mountaineerman/KCP2/Checklists/3_KeyBindings.pdf

d = default, dm = default(mod), nd = not default
Ca tegory | Key | ^ | Effect
| S | d | Rotate part up
| W | d | Rotate part down
| A | d | Rotate part left (flat)
| D | d | Rotate part right (flat)
| Q | d | Rotate part left
| E | d | Rotate part right
| Shift + W/S/A/D/Q/E | d | Rotate parts in 5° instead of 90° steps
| ` (back quote) | d | Search part
| Delete | d | Delete selected part
| L | dm | Toggle day/night mode & part lights (LightsOut)
| U | dm | Toggle all part lights (LightsOut)
| 1 | d | Place Mode
| 2 | d | Offset Mode
| 3 | d | Rotate Mode
| 4 | d | Root Mode
| 5 | dm | Part Scale Mode (TweakScale)
| 6 | dm | Open RCS Build Aid
| I/J/K/L/H/N | dm | Visualize RCS (RCS Build Aid)
| LeftCtrl (hold) | dm | Override “match node size (TweakScale)
| M | dm | Toggle “match node size (TweakScale)
| F | d | In Place mode: Toggle Symmetry between vessel or parent part
| F | d | In Offset mode: Toggle between absolute or load centered offset
| F | d | In Rotate mode: Toggle between absolute or relative rotation
| Ctrl + Z | d | Undo last action
| Ctrl + Y | d | Redo last action
| LeftAlt (hold) | d | Disable surface attach/exclusively use node attach
| Shift + Left-click | d | Move the entire ship
| Control + Left-click | d | Toggle part for snap and show part name
| LeftAlt + Left-click | d | Duplicate part or assembly in VAB
| Page Up/Down | d | Scroll view up/down
| Scroll Wheel | d
| R | d | Toggle Symmetry Method between mirror or radial
| X | d | Cycle symmetry settings (next)
| Shift + X | d | Cycle symmetry settings (previous)
| C | d | Toggle Angle Snap: next
| Shift + C | d | Toggle Angle Snap: previous
| LeftAlt + Shift + Left Click | dm | Strip symmetry from part
| V | dm | Vertically center part
| H | dm | Horizontally center part
| U | dm | ?
| T | dm | Toggle surface/node attachment mode
| Alt + Z | dm | Toggle part clipping
| Space (no part selected) | dm | Reset camera pitch & heading
| In Offset Mode, open EEX > Fine Adjustments, ↑/↓/←/→/Rshift/Rctrl | dm | Move or Rotate part

VAB/SPH Controls

Editor Extensions Redux

Ca tegory | Key | ^ | Effect
| F1 | d | Screenshot
| F2 | d | Toggle UI visibility
| F3 | d | Toggle results screen
| F4 | d | Toggle ship labels & docking target/distance indicators
| F5 | d | Quicksave
| RightShift + F5 | d | Quicksave (choose name)
| F6 | d | Previous action set
| F7 | d | Next action set
| F9 (Hold) | d | Load quicksave
| RightShift + F9 | d | Load a specific quicksave
| F10 | d | Toggle temperature gauges
| RightShift + F10 | dm | Open Contract Configurator window
| F11 | d | Toggle temperatures overlay
| F12 | d | Toggle aerodynamic forces overlay
| LeftAlt + F12 | d | Debug/cheat menu
| Escape | d | Pause Menu
| F (Hold) | d | Invert SAS state
| C | d | Toggle IVA view
| V | d | Toggle camera view (auto/free/orbital/chase)
| ` (back quote) | d | Reset camera
| \ | d | Toggle camera movement with mouse
| LeftAlt + . (period) | d | Forced time warp increase (Physical time warp)
| LeftAlt + , (comma) | d | Forced time warp decrease (Physical time warp)
| / | d | Stop time warp
| - (minus) | nd | Toggle navball
| ] | d | Focus through ships (next)
| [ | d | Cycle through ships (previous)
| 1-9, 0 | d | Activate custom action group 1-10
| LeftAlt + W/S/A/D/Q/E | d | Trim pitch/yaw/roll
| LeftAlt + X | d | Reset trim
| Right-click | d | Open part info window
| LeftAlt + Right-click | d | Open multiple info windows for fuel transfer
| LeftAlt + N | dm | Toggle maneuver node gizmo
| Tab | d | Cycle focus in orbital map
| Shift + Tab | d | Reverse cycle focus in orbital map
| ` (back quote) | d | Reset focus in orbital map
| W | d | Walk/jetpack forward
| S | d | Walk/jetpack backwards
| A | d | Walk/jetpack left
| D | d | Walk/jetpack right
| R | d | Toggle jetpack
| Q | d | Jetpack rotate left
| E | d | Jetpack rotate right
| Left-Shift | d | Jetpack up
| Left-Control | d | Jetpack down
| Left-click and drag left | d | Jet counter clockwise
| Left-click and drag right | d | Jet clockwise
| Left-click and drag up | d | Pitch down by jet
| Left-click and drag down | d | Pitch up by jet
| Space | d | Jetpack - Reorient camera
| Space | d | Jump
| LeftShift (hold) | d | Run
| F | d | Use part
| F | dm | Toggle desire to grab ladder (Easyboard)
| I | d | Toggle EVA Construction Mode
| B | d | Board
| B | dm | Toggle desire to board (Easyboard)
| U | d | Toggle lights
| O | d | Toggle helmet
| P | d | Deploy parachute
| Shift + (W/S/A/D) + Space | d | Jump to different directions when on ladders

Flight – System

Settings

Flight Controls

Map

EVA

Controls
