mountaineerman/KCP2/KCP2-physical/Documentation/ScrewDimensions.png

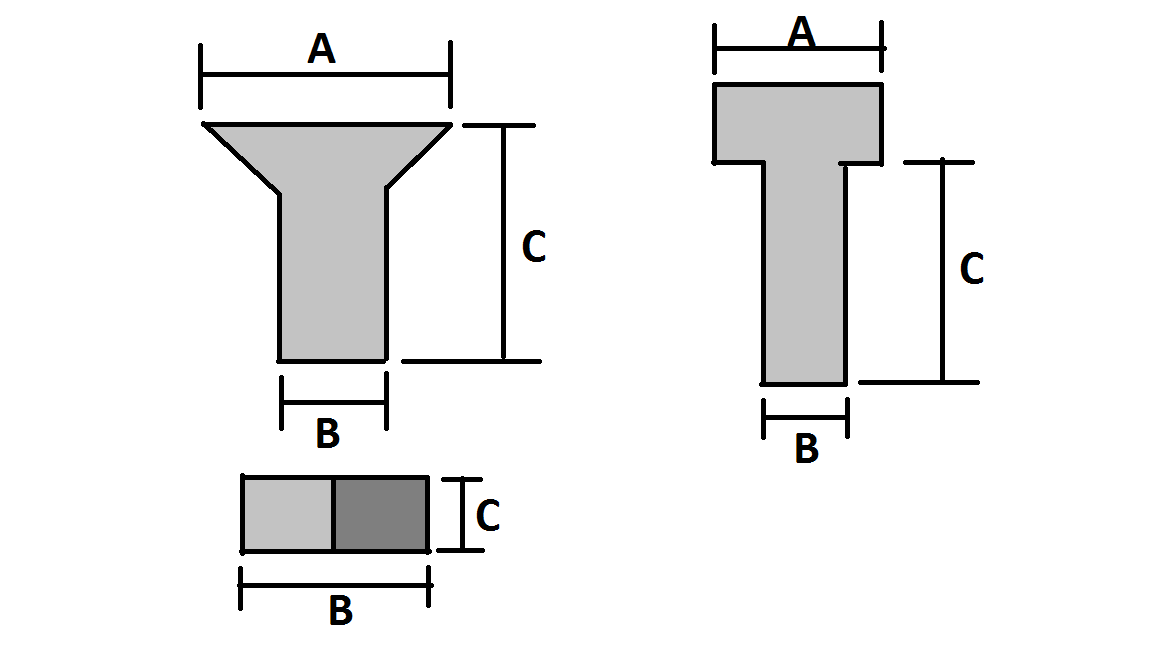
KCP2-physical/Documentation/ScrewDimensions.png
