mountaineerman/KCP2/KCP2-physical/GaugeBackgrounds/Navball.PNG

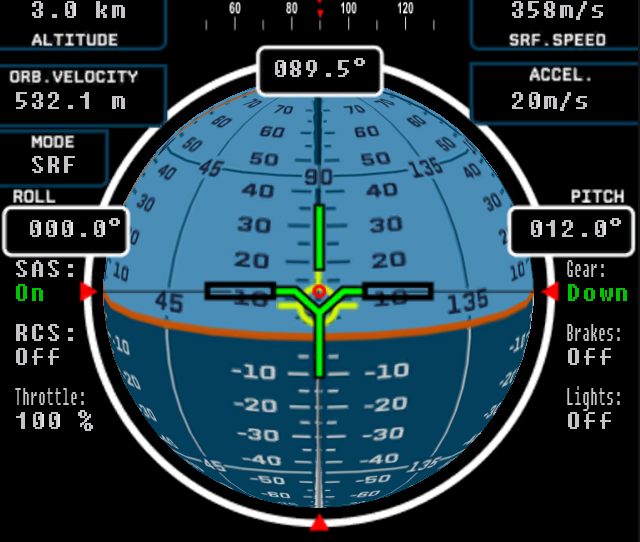
KCP2-physical/GaugeBackgrounds/Navball.PNG
