mountaineerman/KCP2/KCP2-physical/Ideas/deltaV map - new.png

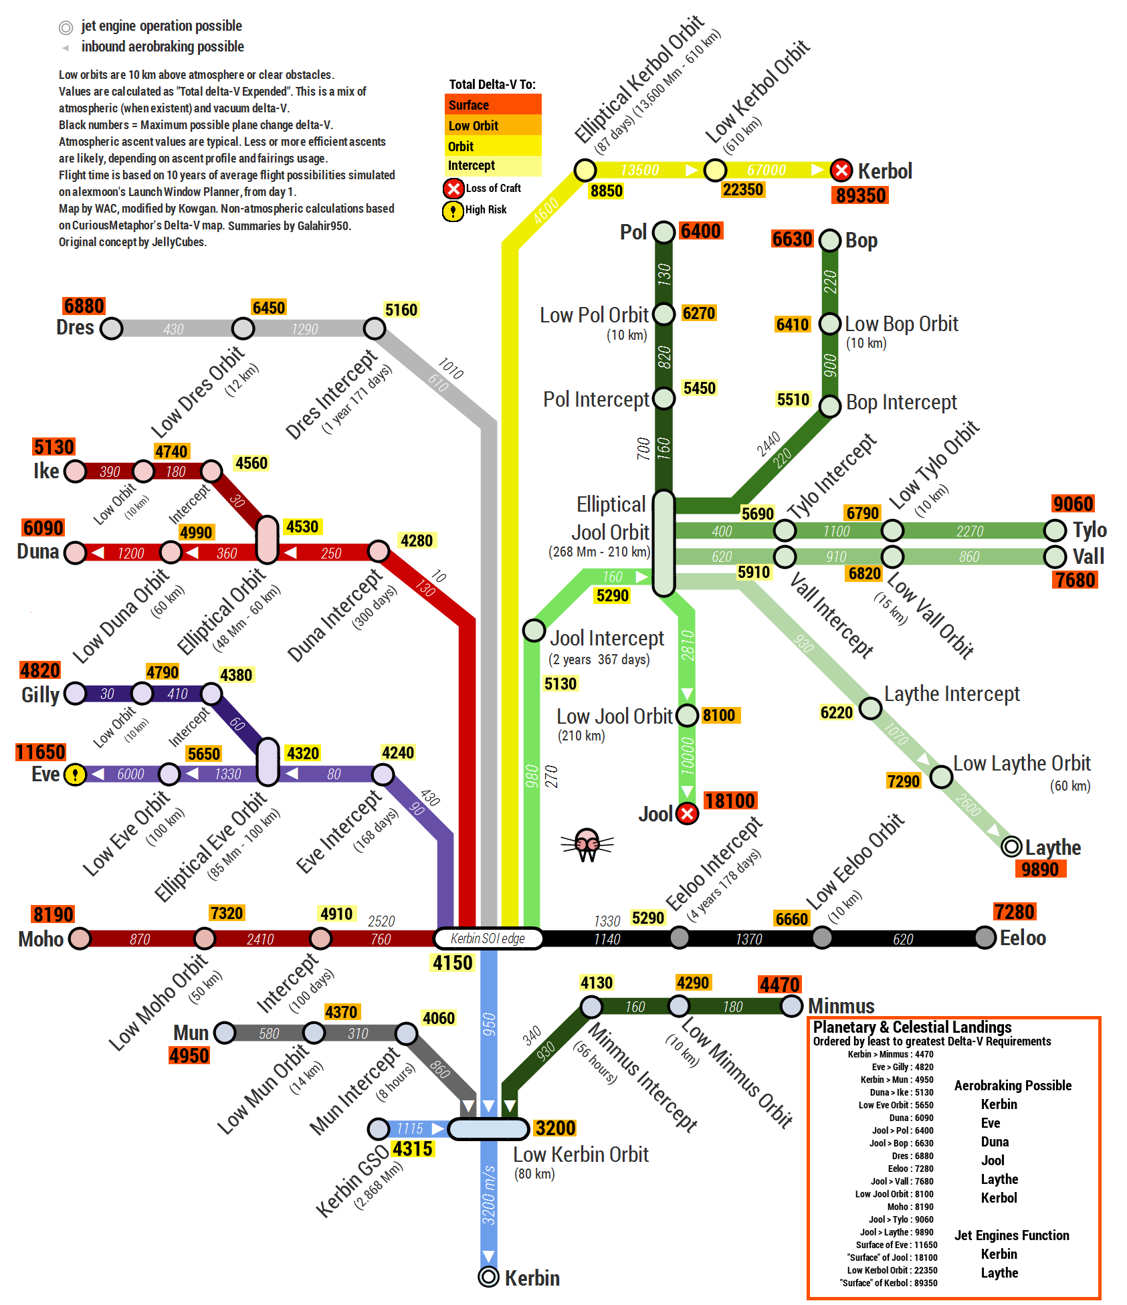
KCP2-physical/Ideas/deltaV map - new.png
