mountaineerman/KCP2/KCP2-physical/Ideas/KSP_reticules.jpg

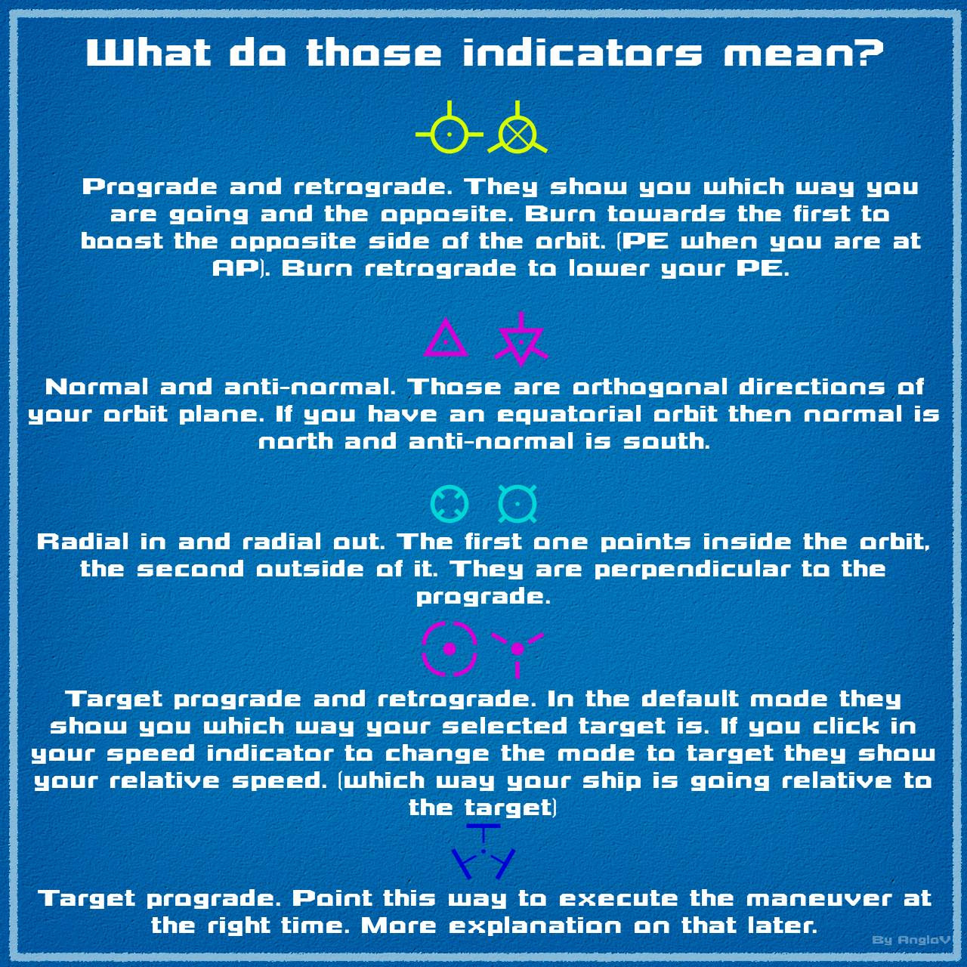
KCP2-physical/Ideas/KSP_reticules.jpg
