mountaineerman/KCP2/KCP2-physical/Photos/2020-05-01.PNG

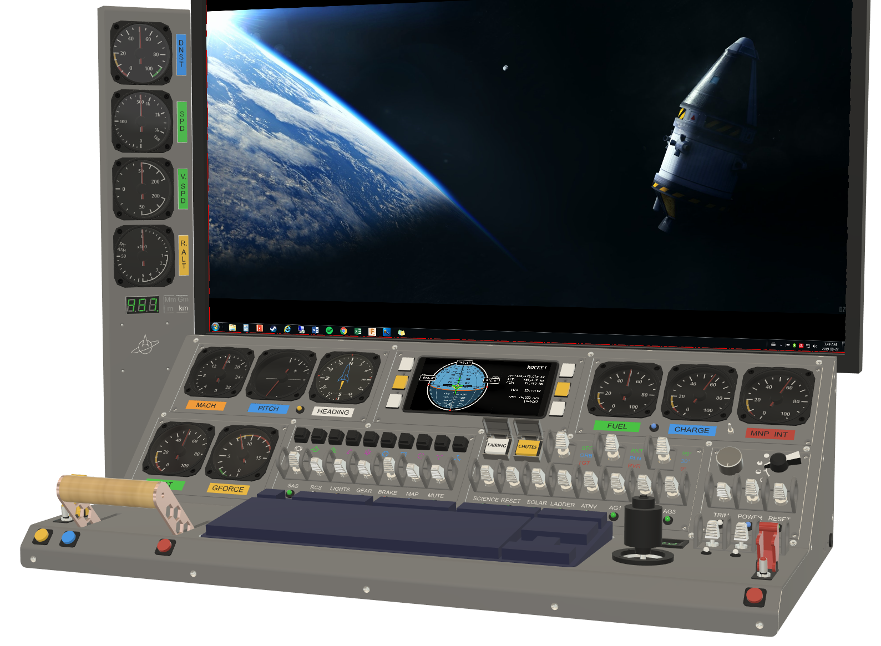
KCP2-physical/Photos/2020-05-01.PNG
