mountaineerman/KCP2/KCP2-physical/Photos/2020-08-04.PNG

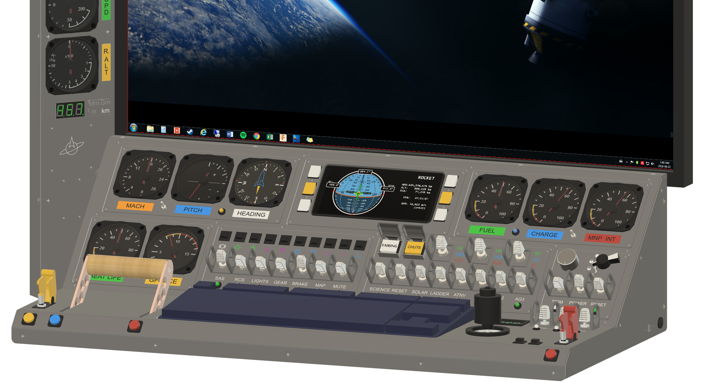
KCP2-physical/Photos/2020-08-04.PNG
