mountaineerman/KCP2/KCP2-physical/Photos/2020-10-26.PNG

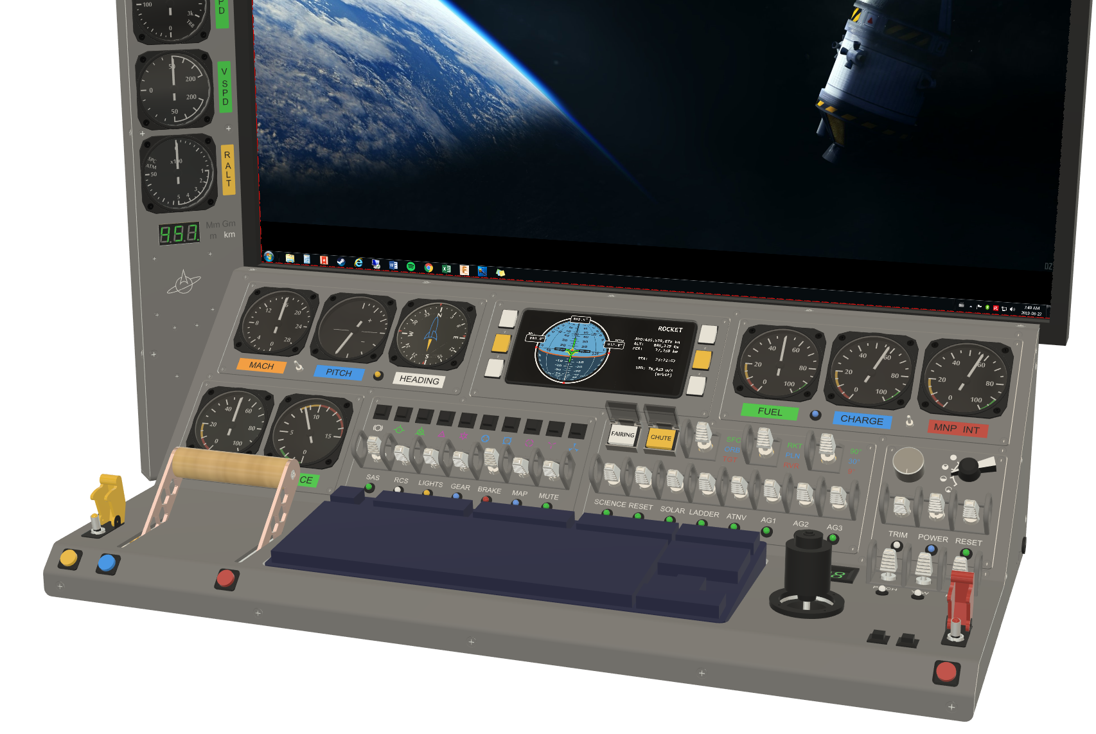
KCP2-physical/Photos/2020-10-26.PNG
