mountaineerman/KCP2/KCP2-physical/Photos/2020-11-08.PNG

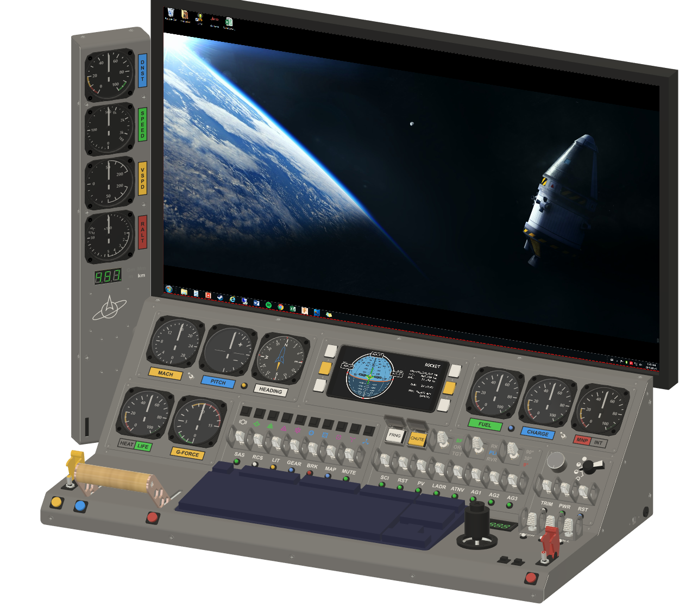
KCP2-physical/Photos/2020-11-08.PNG
