mountaineerman/KCP2/KCP2-physical/Photos/Brackets.PNG

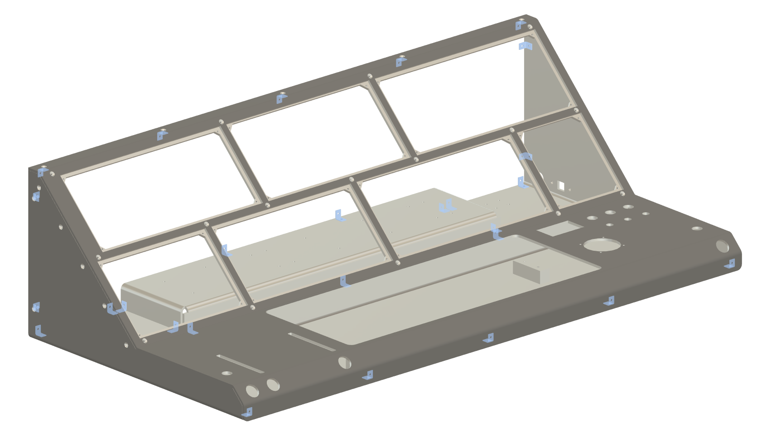
KCP2-physical/Photos/Brackets.PNG
