mountaineerman/KCP2/KCP2-physical/Photos/CAD Progress 2.JPG

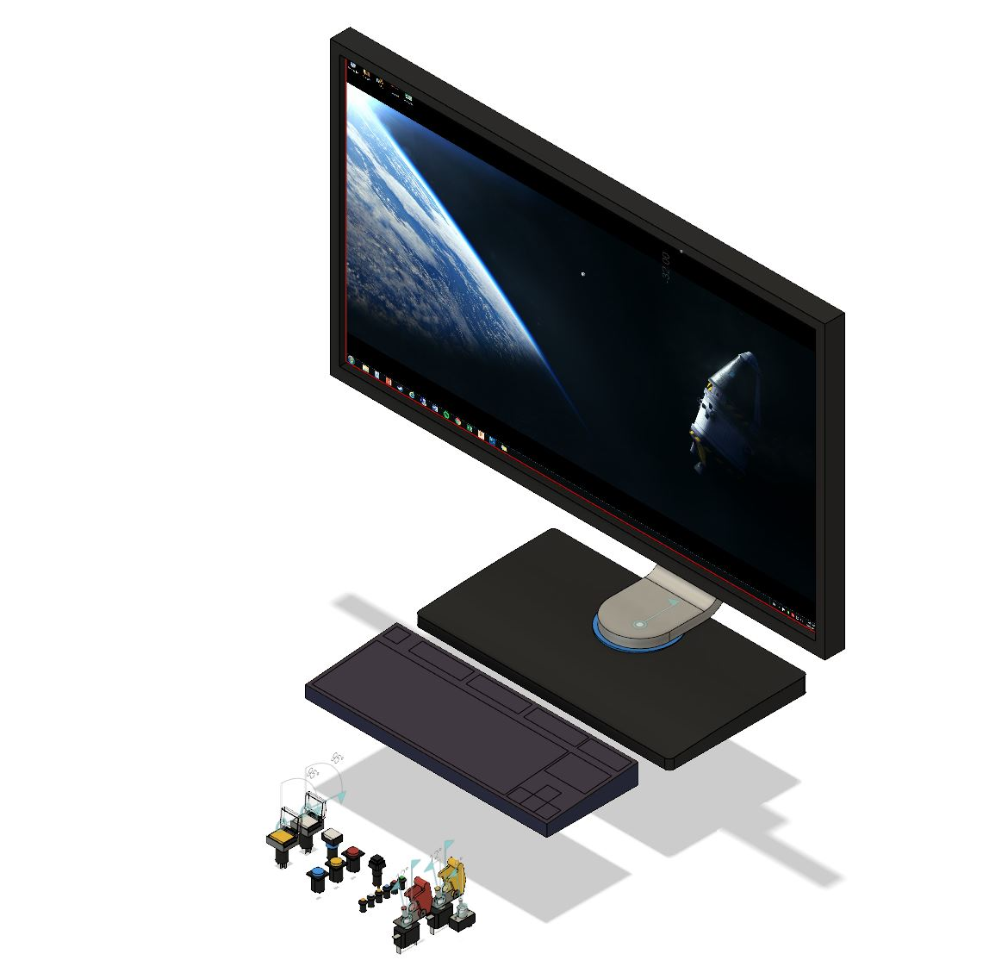
KCP2-physical/Photos/CAD Progress 2.JPG
