mountaineerman/KCP2/KCP2-physical/Photos/CAD Progress 3.JPG

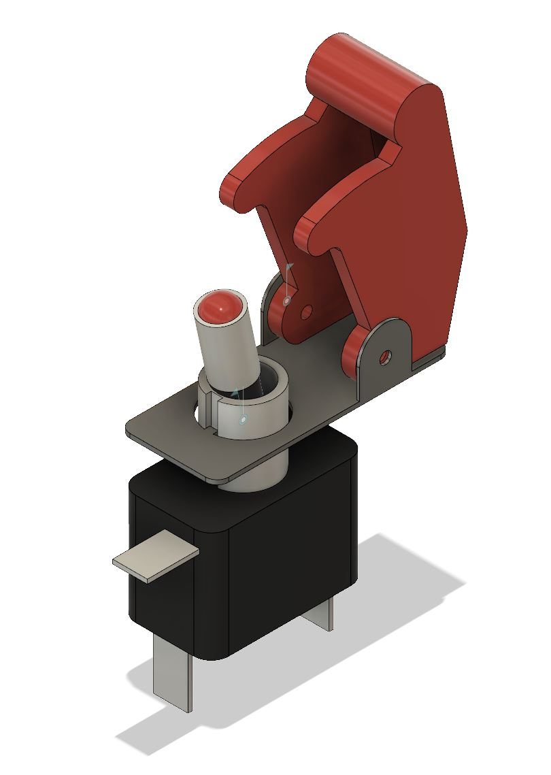
KCP2-physical/Photos/CAD Progress 3.JPG
