mountaineerman/KCP2/KCP2-physical/Photos/CAD progress.JPG

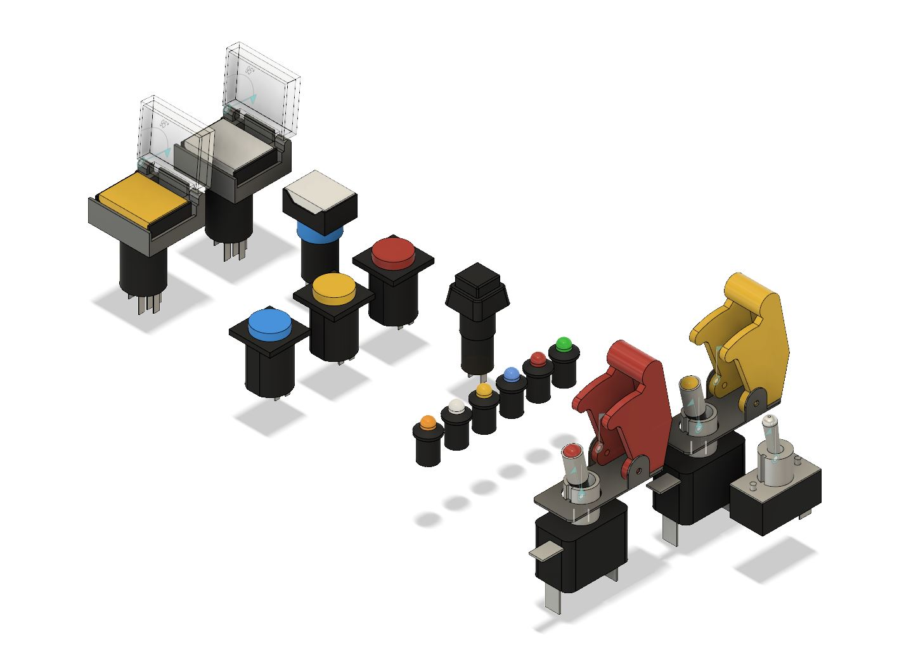
KCP2-physical/Photos/CAD progress.JPG
