mountaineerman/KCP2/KCP2-physical/Photos/Columns.PNG

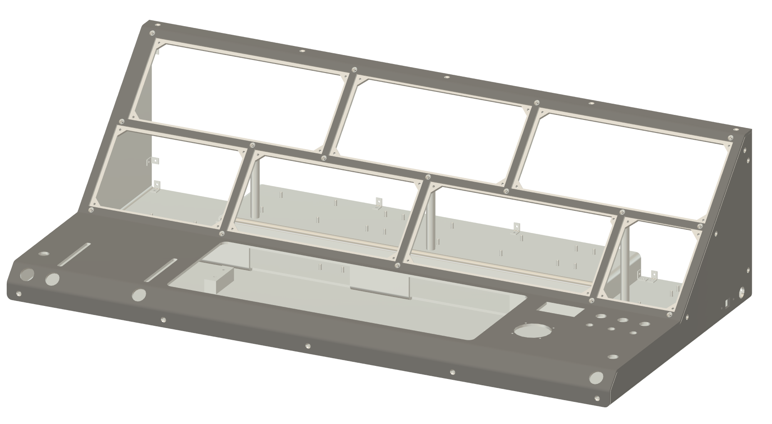
KCP2-physical/Photos/Columns.PNG
