mountaineerman/KCP2/KCP2-physical/Photos/Complete_Autopilot.PNG

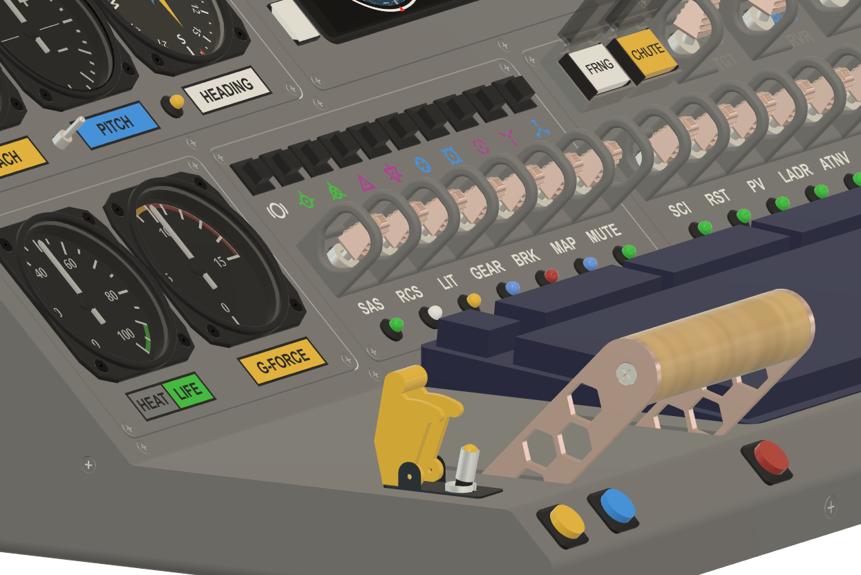
KCP2-physical/Photos/Complete_Autopilot.PNG
