mountaineerman/KCP2/KCP2-physical/Photos/Complete_Gauges.PNG

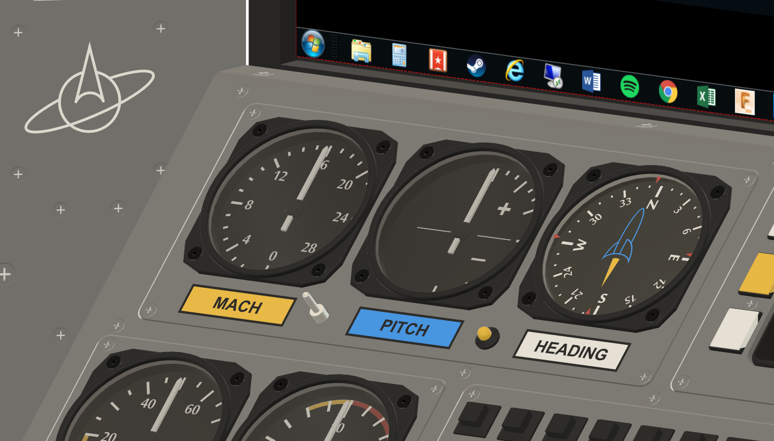
KCP2-physical/Photos/Complete_Gauges.PNG
