mountaineerman/KCP2/KCP2-physical/Photos/Complete_Whole.PNG

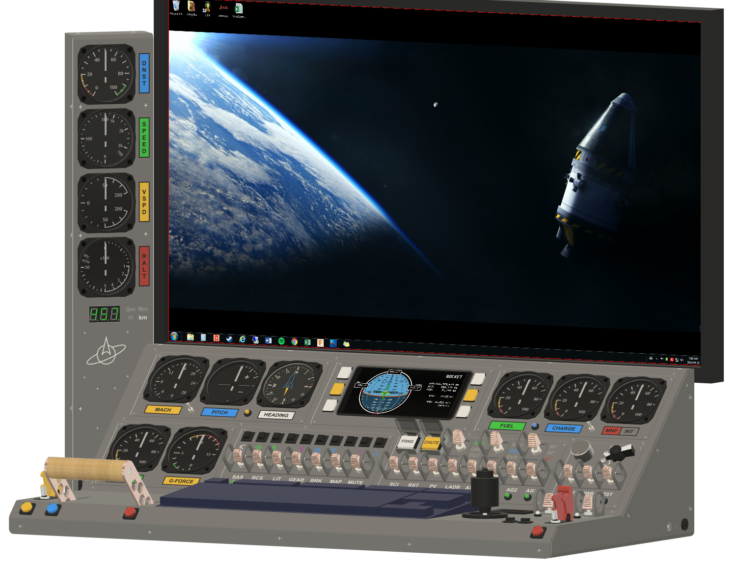
KCP2-physical/Photos/Complete_Whole.PNG
