mountaineerman/KCP2/KCP2-physical/Photos/FromFront.PNG

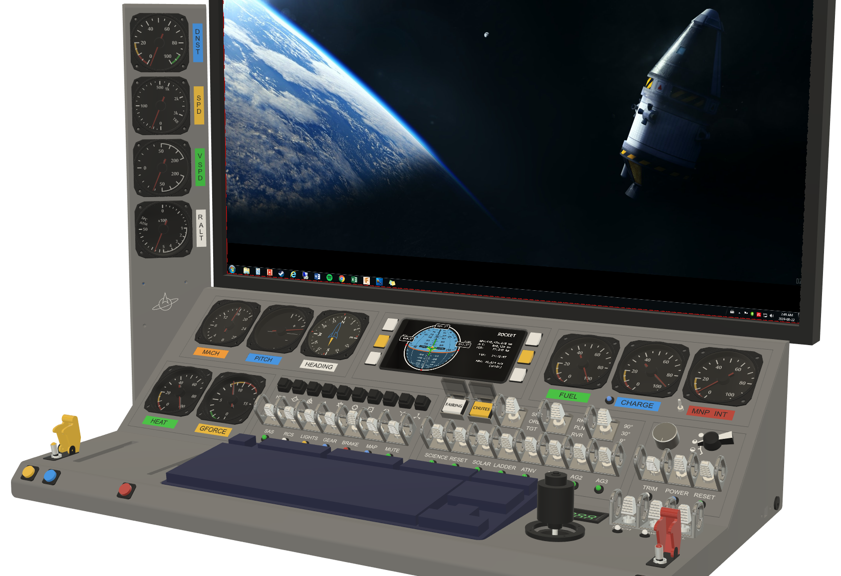
KCP2-physical/Photos/FromFront.PNG
