mountaineerman/KCP2/KCP2-physical/Photos/GaugeTowerAdapters.PNG

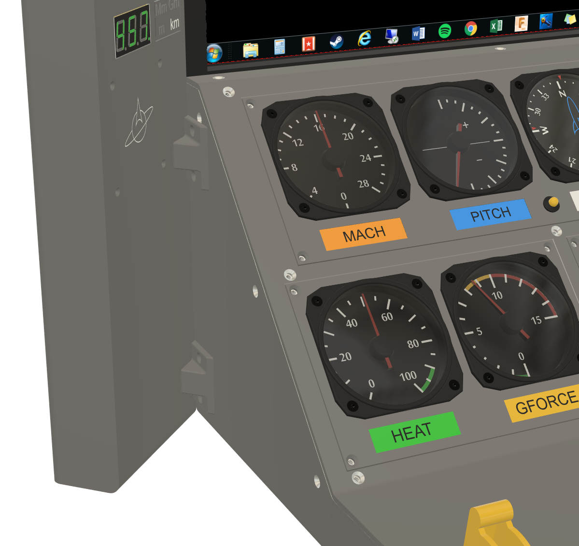
KCP2-physical/Photos/GaugeTowerAdapters.PNG
