mountaineerman/KCP2/KCP2-physical/Photos/GaugeTowerCasing.PNG

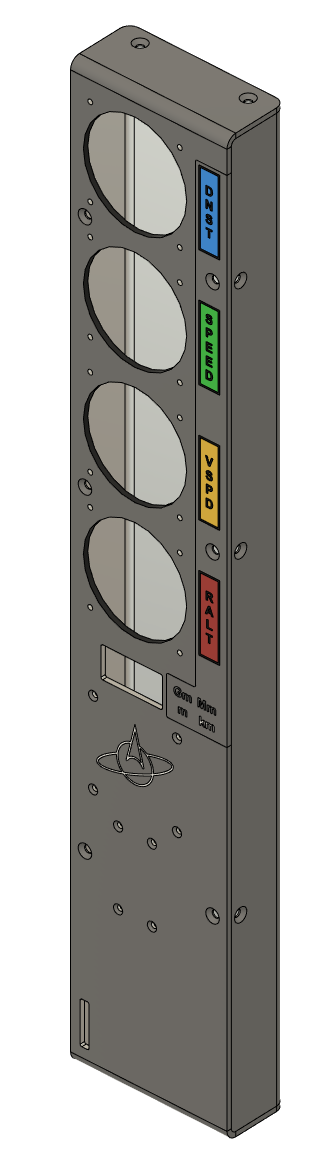
KCP2-physical/Photos/GaugeTowerCasing.PNG
