mountaineerman/KCP2/KCP2-physical/Photos/P1040881.JPG

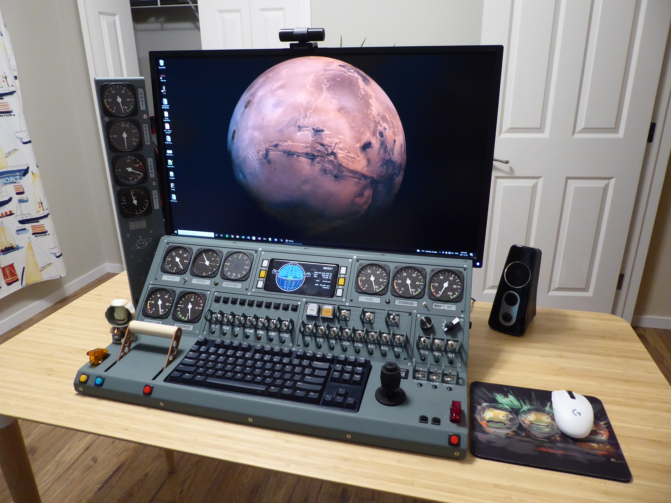
KCP2-physical/Photos/P1040881.JPG
