mountaineerman/KCP2/KCP2-physical/Photos/P1040882.JPG

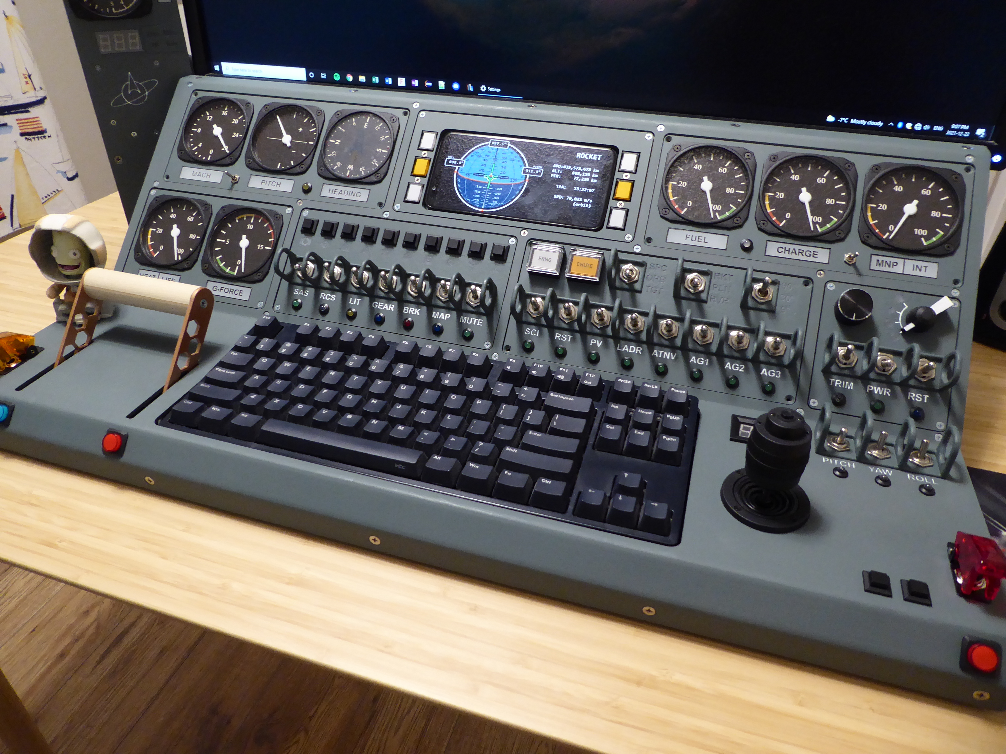
KCP2-physical/Photos/P1040882.JPG
