mountaineerman/KCP2/KCP2-physical/Photos/Render1.PNG

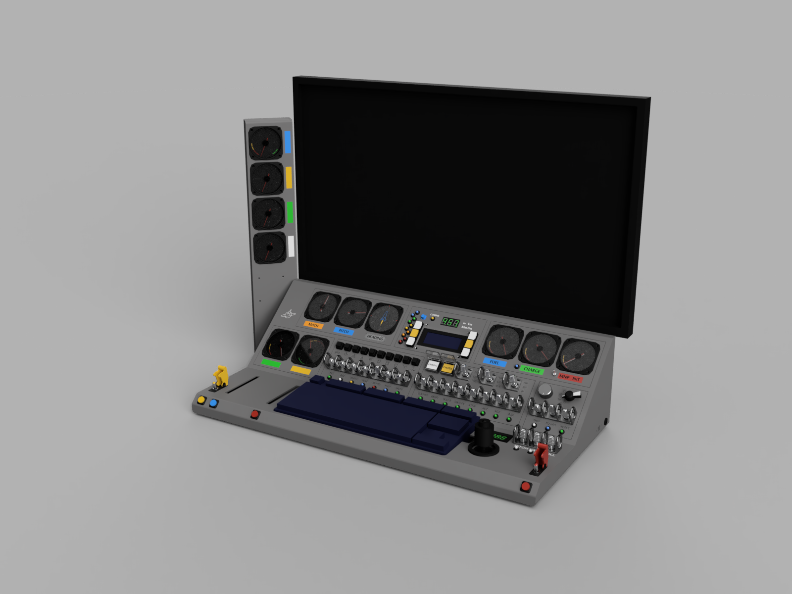
KCP2-physical/Photos/Render1.PNG
