mountaineerman/KCP2/KCP2-physical/Photos/ShowingOffNewNeedles.PNG

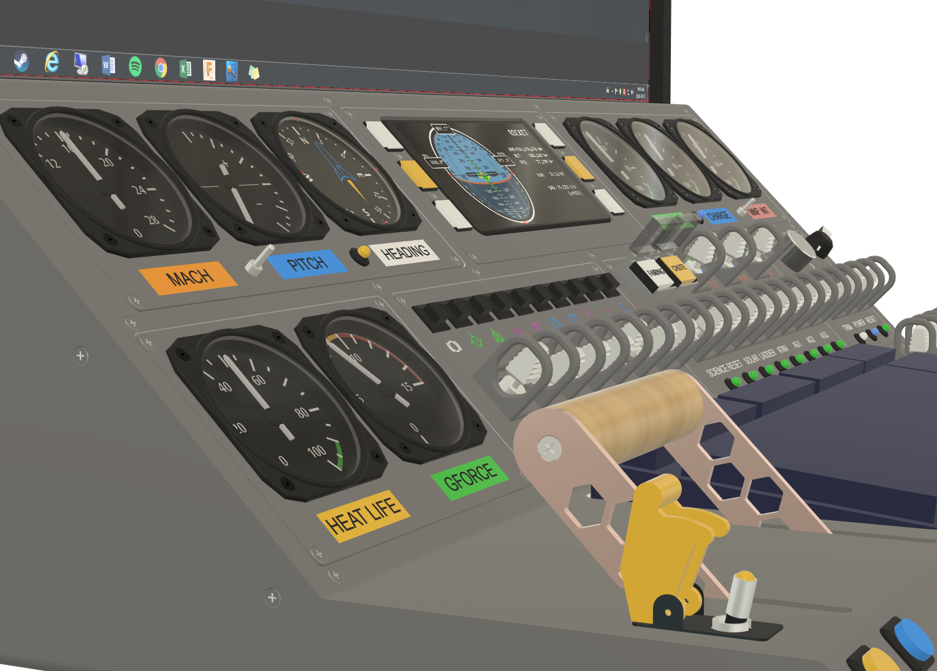
KCP2-physical/Photos/ShowingOffNewNeedles.PNG
