mountaineerman/KCP2/KCP2-physical/Photos/Summary/E.PNG

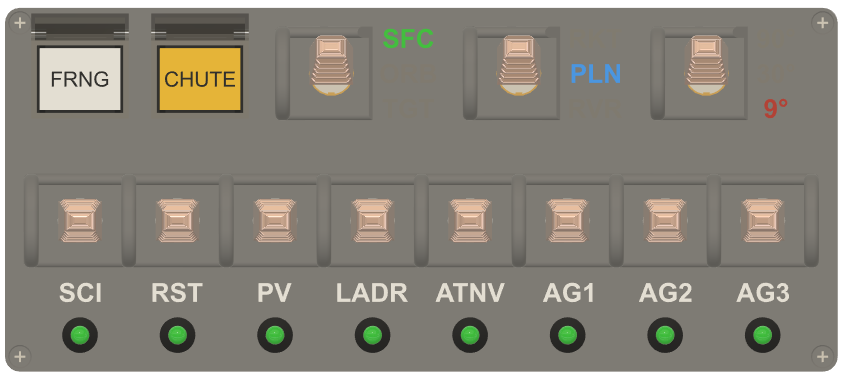
KCP2-physical/Photos/Summary/E.PNG
