mountaineerman/KCP2/KCP2-physical/Photos/Summary/z_GT_Backside.PNG

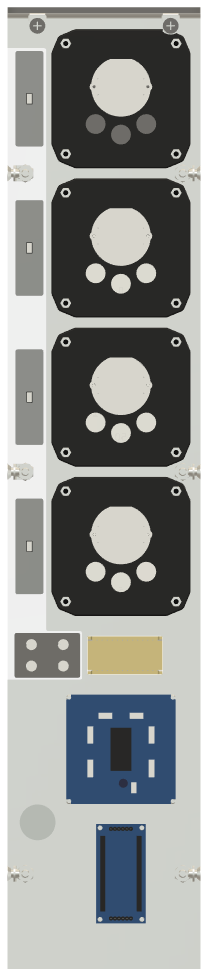
KCP2-physical/Photos/Summary/z_GT_Backside.PNG
