mountaineerman/KCP2/KCP2-physical/Photos/Update.PNG

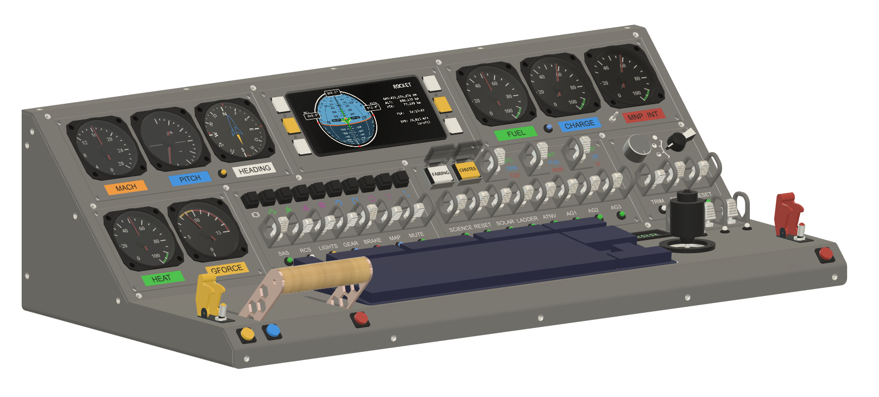
KCP2-physical/Photos/Update.PNG
