mountaineerman/KCP2/KCP2-physical/Photos/WIP_RenderSnip.PNG

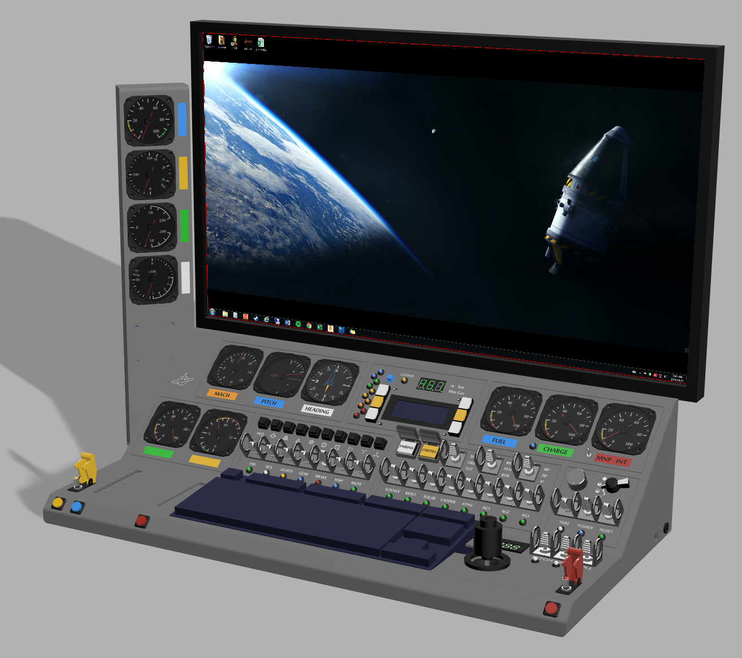
KCP2-physical/Photos/WIP_RenderSnip.PNG
