mountaineerman/KCP2/KCP2-physical/CAD/ForManufacture/Aluminum/Long Column/LongColumn_v91.step

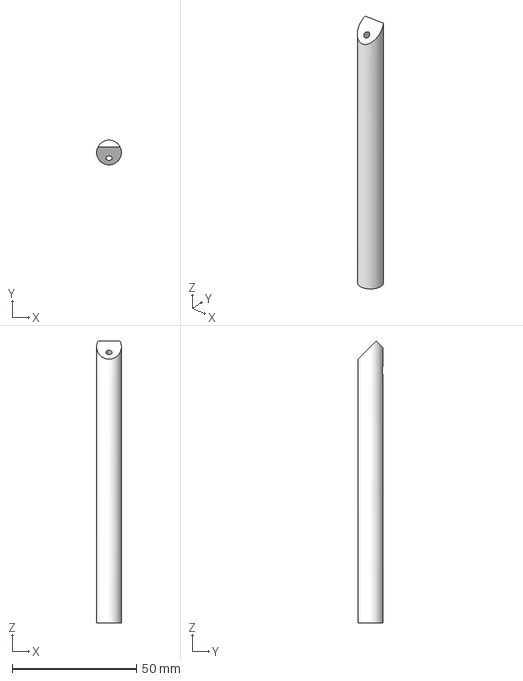
[picture p72: CAD file, 2026-02-16]
KCP2-physical/CAD/ForManufacture/Aluminum/Long Column/LongColumn_v91.step
10.00 x 10.00 x 113.7 mm
