mountaineerman/KCP2/KCP2-physical/CAD/ForManufacture/Aluminum/Panel Dodge Plate/Panel_DodgePlate_v95_Folded.step

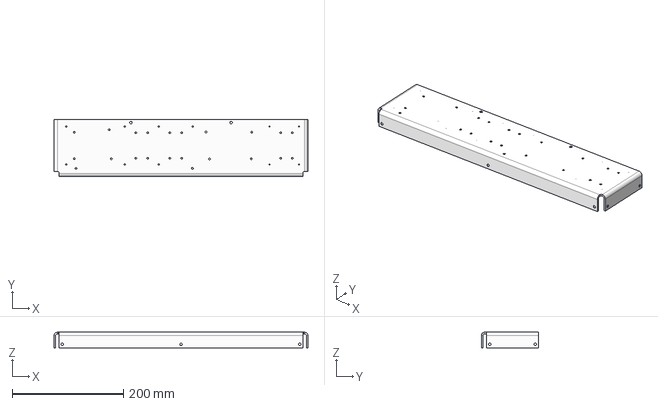
[picture p73: CAD file, 2026-02-16]
KCP2-physical/CAD/ForManufacture/Aluminum/Panel Dodge Plate/Panel_DodgePlate_v95_Folded.step
456.0 x 103.0 x 28.0 mm
