mountaineerman/KCP2/KCP2-physical/CAD/ForManufacture/Aluminum/Panel Mounting Plate/Panel_MountingPlate_v96_FlatPattern.step

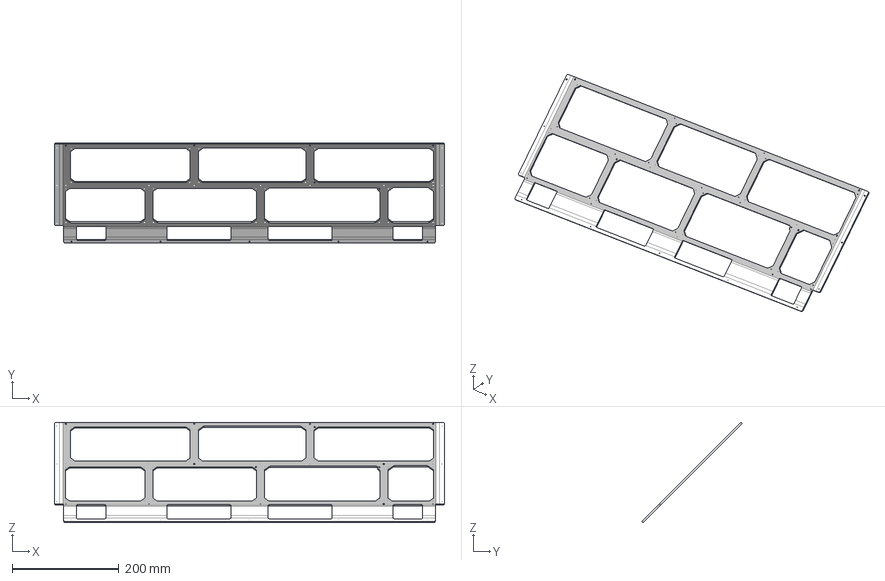
[picture p74: CAD file, 2026-02-16]
KCP2-physical/CAD/ForManufacture/Aluminum/Panel Mounting Plate/Panel_MountingPlate_v96_FlatPattern.step
730.6 x 187.6 x 187.6 mm
