mountaineerman/KCP2/KCP2-physical/CAD/ForManufacture/Aluminum/Panel Top Plate/Panel_TopPlate_v96.dxf

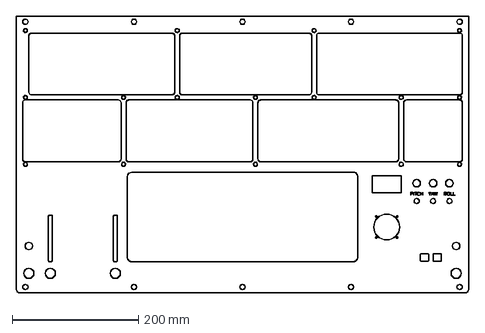
[picture p75: CAD file, 2026-02-16]
KCP2-physical/CAD/ForManufacture/Aluminum/Panel Top Plate/Panel_TopPlate_v96.dxf
717.0 x 438.7 mm
