mountaineerman/KCP2/KCP2-physical/CAD/ForManufacture/Aluminum/Short Column/ShortColumn_v91.step

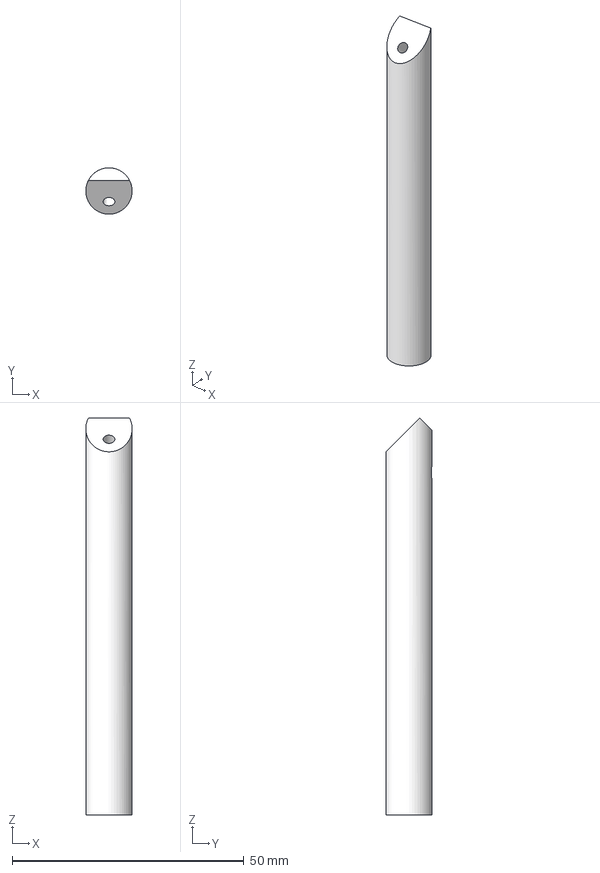
[picture p76: CAD file, 2026-02-16]
KCP2-physical/CAD/ForManufacture/Aluminum/Short Column/ShortColumn_v91.step
9.99 x 10.00 x 85.7 mm
