mountaineerman/KCP2/KCP2-physical/CAD/ForManufacture/Aluminum/Throttle Bracket/ThrottleBracket_v38_Folded.step

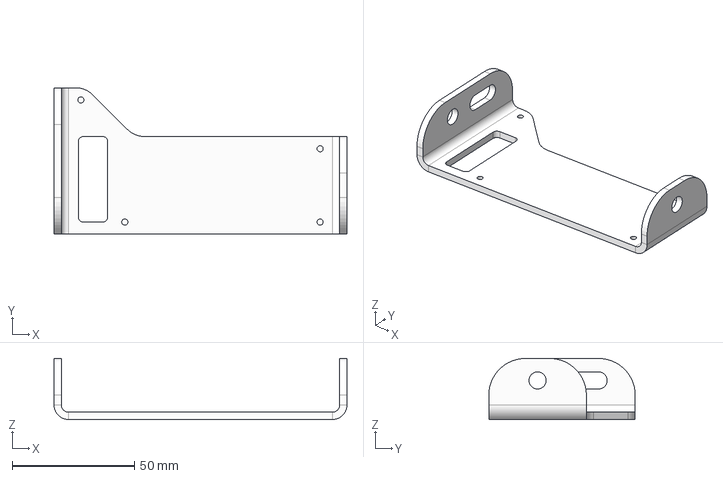
[picture p77: CAD file, 2026-02-16]
KCP2-physical/CAD/ForManufacture/Aluminum/Throttle Bracket/ThrottleBracket_v38_Folded.step
120.0 x 60.0 x 25.0 mm
