mountaineerman/KCP2/KCP2-physical/CAD/ForManufacture/Aluminum/Throttle Handlebar/ThrottleHandlebar_v38.step

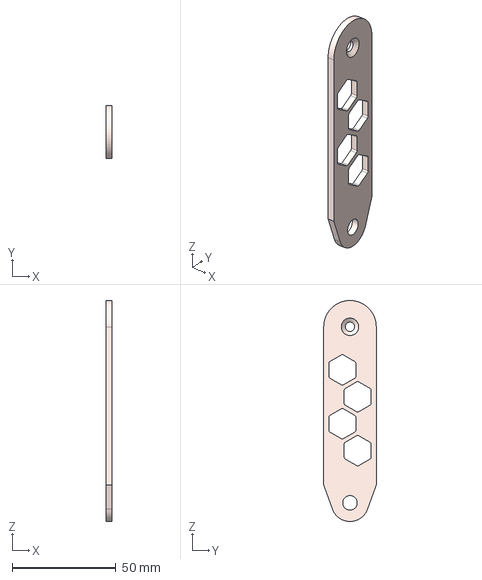
[picture p78: CAD file, 2026-02-16]
KCP2-physical/CAD/ForManufacture/Aluminum/Throttle Handlebar/ThrottleHandlebar_v38.step
3.00 x 25.4 x 106.7 mm
