mountaineerman/KCP2/KCP2-physical/CAD/ForManufacture/ClearAcrylic/Gauge Tower Acrylic Panel/GaugeTower_AcrylicPlate_v18.step

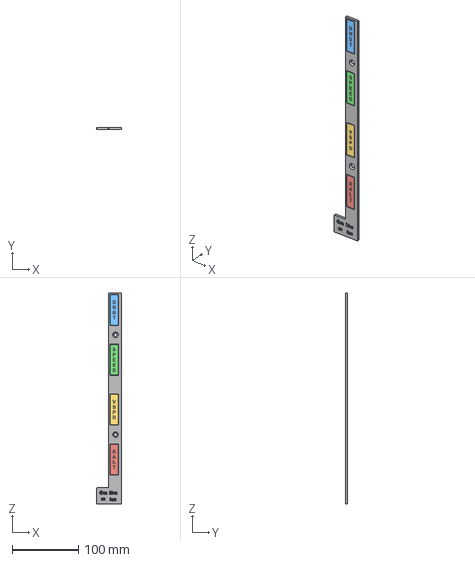
[picture p79: CAD file, 2026-02-16]
KCP2-physical/CAD/ForManufacture/ClearAcrylic/Gauge Tower Acrylic Panel/GaugeTower_AcrylicPlate_v18.step
37.5 x 3.02 x 317.5 mm
