mountaineerman/KCP2/KCP2-physical/CAD/ForManufacture/ClearAcrylic/Module C/ModuleC_v4.step

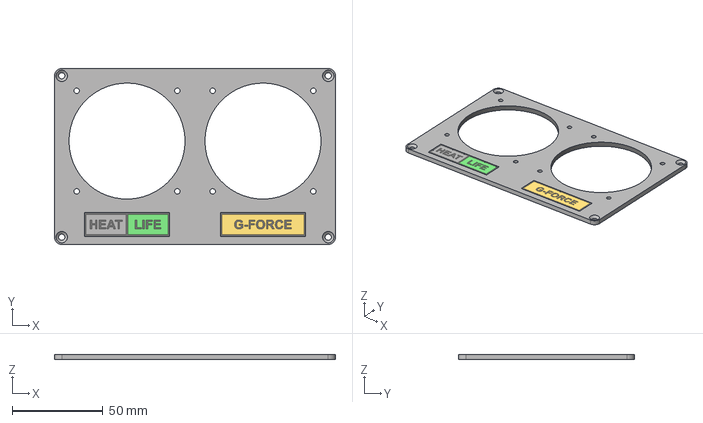
[picture p80: CAD file, 2026-02-16]
KCP2-physical/CAD/ForManufacture/ClearAcrylic/Module C/ModuleC_v4.step
155.0 x 97.0 x 3.02 mm
