mountaineerman/KCP2/KCP2-physical/CAD/ForManufacture/ClearAcrylic/Module D/ModuleD_v6.step

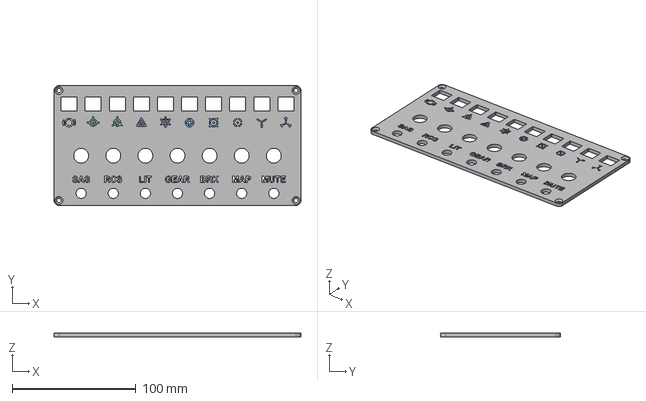
[picture p81: CAD file, 2026-02-16]
KCP2-physical/CAD/ForManufacture/ClearAcrylic/Module D/ModuleD_v6.step
200.0 x 97.0 x 3.02 mm
Autopilot Labels
Labels
