mountaineerman/KCP2/KCP2-physical/CAD/ForManufacture/ClearAcrylic/Module E/ModuleE_v9.step

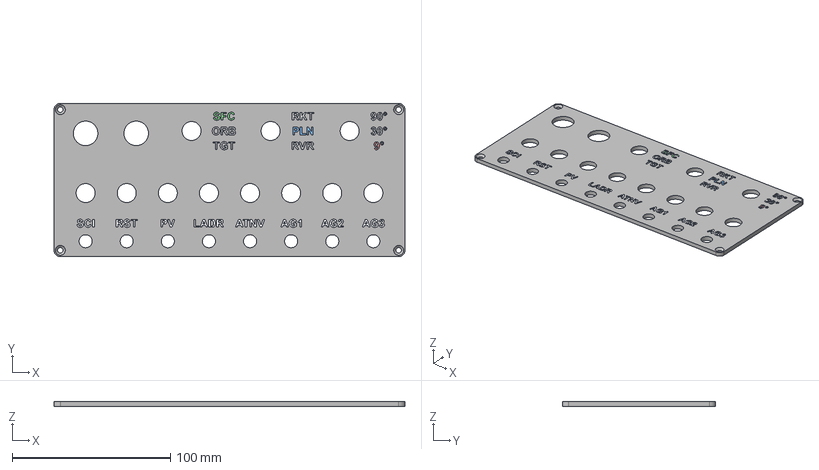
[picture p82: CAD file, 2026-02-16]
KCP2-physical/CAD/ForManufacture/ClearAcrylic/Module E/ModuleE_v9.step
222.0 x 97.0 x 3.02 mm
