mountaineerman/KCP2/KCP2-physical/CAD/ForManufacture/ClearAcrylic/Module F/ModuleF_v4.step

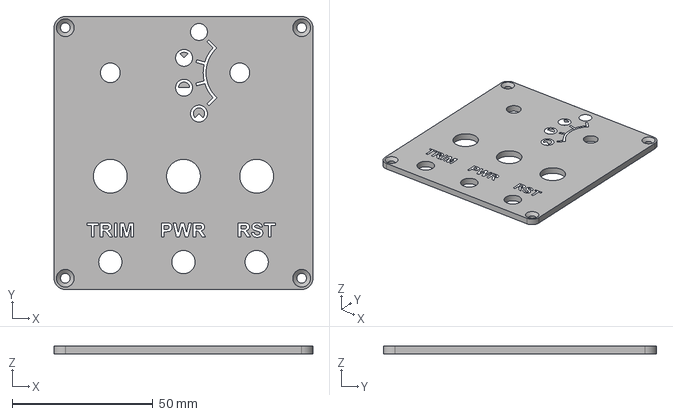
[picture p83: CAD file, 2026-02-16]
KCP2-physical/CAD/ForManufacture/ClearAcrylic/Module F/ModuleF_v4.step
92.0 x 97.0 x 3.02 mm
