mountaineerman/KCP2/KCP2-physical/CAD/ForManufacture/ClearAcrylic/Module G/ModuleG_v2.step

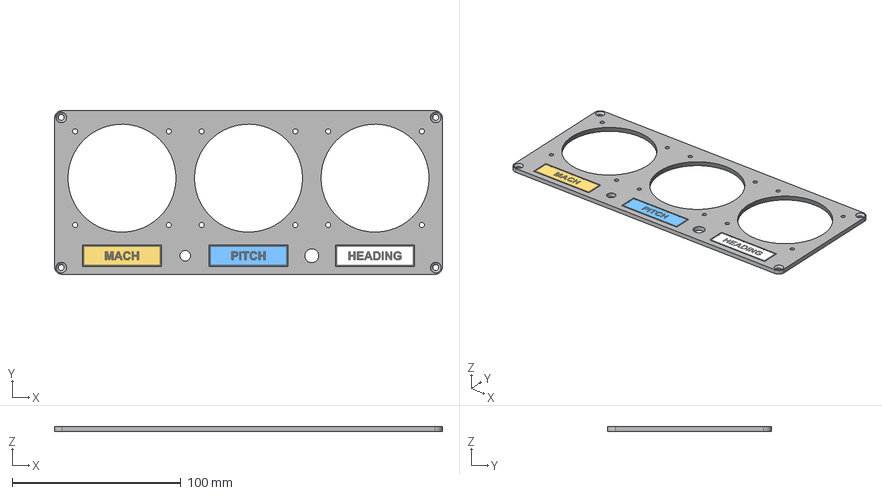
[picture p84: CAD file, 2026-02-16]
KCP2-physical/CAD/ForManufacture/ClearAcrylic/Module G/ModuleG_v2.step
230.0 x 97.0 x 3.02 mm
