mountaineerman/KCP2/KCP2-physical/CAD/ForManufacture/ClearAcrylic/Module H/ModuleH_v30.step

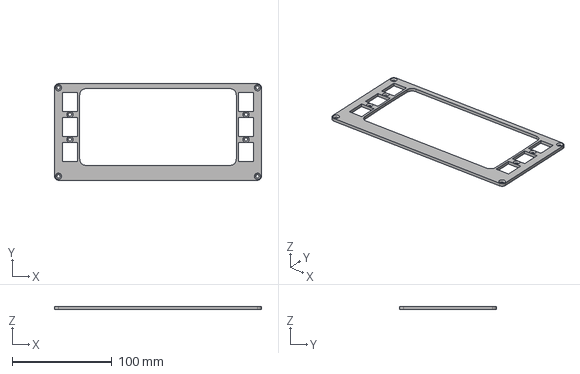
[picture p85: CAD file, 2026-02-16]
KCP2-physical/CAD/ForManufacture/ClearAcrylic/Module H/ModuleH_v30.step
208.0 x 97.0 x 3.00 mm
