mountaineerman/KCP2/KCP2-physical/CAD/ForManufacture/Revisions_2021-03-29/GaugeTower_FrontPanel_v21_Folded.step

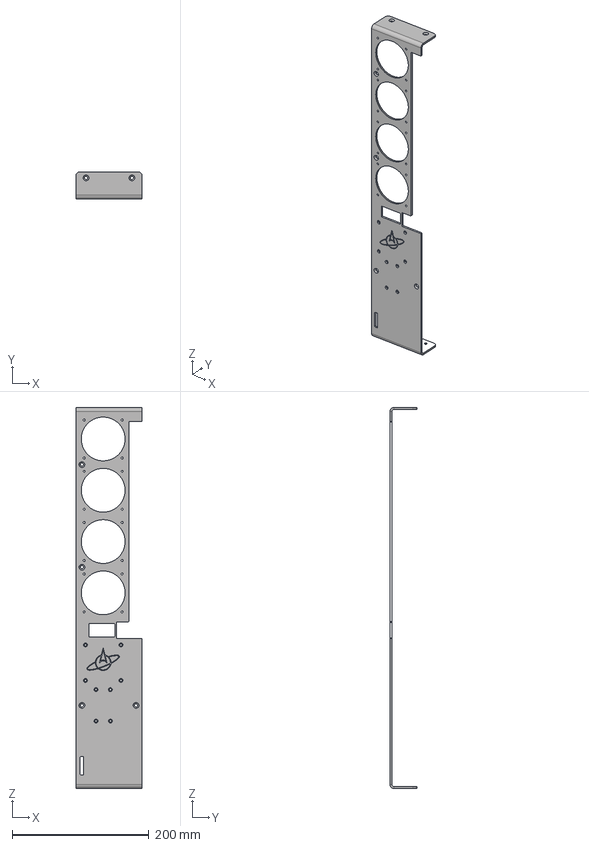
[picture p86: CAD file, 2026-02-16]
KCP2-physical/CAD/ForManufacture/Revisions_2021-03-29/GaugeTower_FrontPanel_v21_Folded.step
97.0 x 40.0 x 557.0 mm
