mountaineerman/KCP2/KCP2-physical/CAD/KerbalControlPanel/ForManufacture/Aluminum/Gauge Tower Back Panel/GaugeTower_BackPanel_v20_Folded.step

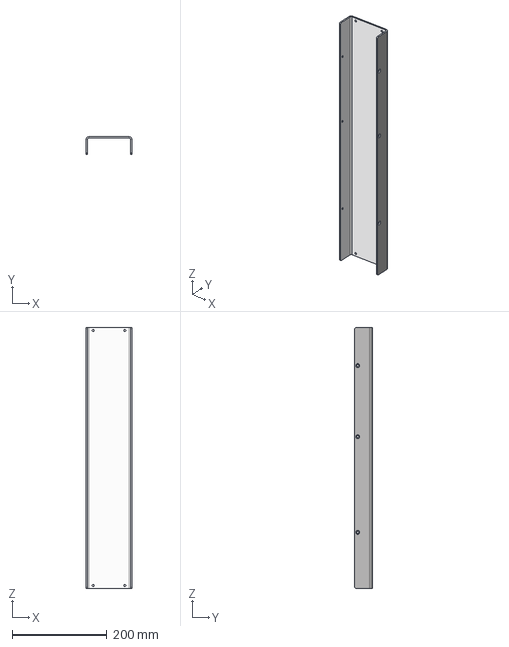
[picture p87: CAD file, 2026-02-16]
KCP2-physical/CAD/KerbalControlPanel/ForManufacture/Aluminum/Gauge Tower Back Panel/GaugeTower_BackPanel_v20_Folded.step
97.0 x 37.0 x 551.0 mm
