mountaineerman/KCP2/KCP2-physical/CAD/KerbalControlPanel/ForManufacture/Aluminum/Gauge Tower Front Panel/GaugeTower_FrontPanel_v18.dxf

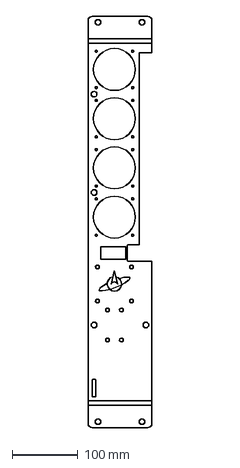
[picture p88: CAD file, 2026-02-16]
KCP2-physical/CAD/KerbalControlPanel/ForManufacture/Aluminum/Gauge Tower Front Panel/GaugeTower_FrontPanel_v18.dxf
97.0 x 626.6 mm
