mountaineerman/KCP2/KCP2-physical/CAD/KerbalControlPanel/ForManufacture/Aluminum/Panel Back Plate/Panel_BackPlate_v95.step

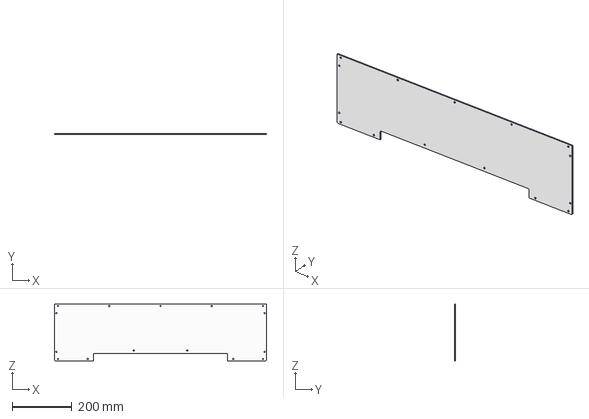
[picture p89: CAD file, 2026-02-16]
KCP2-physical/CAD/KerbalControlPanel/ForManufacture/Aluminum/Panel Back Plate/Panel_BackPlate_v95.step
711.0 x 3.00 x 189.8 mm
