mountaineerman/KCP2/KCP2-physical/CAD/KerbalControlPanel/ForManufacture/Aluminum/Panel Bottom Plate/Panel_BottomPlate_v96_Folded.step

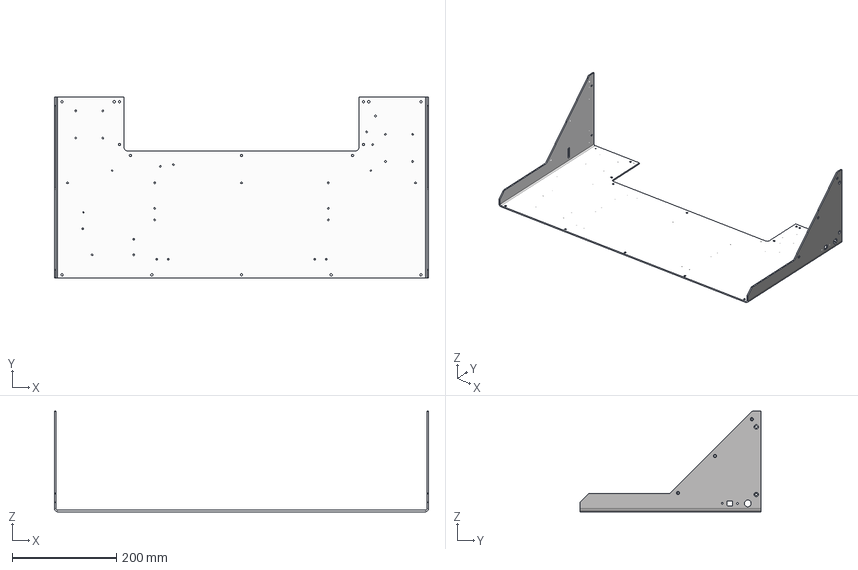
[picture p90: CAD file, 2026-02-16]
KCP2-physical/CAD/KerbalControlPanel/ForManufacture/Aluminum/Panel Bottom Plate/Panel_BottomPlate_v96_Folded.step
717.0 x 346.6 x 192.8 mm
