mountaineerman/KCP2/KCP2-physical/CAD/KerbalControlPanel/ForManufacture/Aluminum/Panel Dodge Plate/Panel_DodgePlate_v95_FlatPattern.step

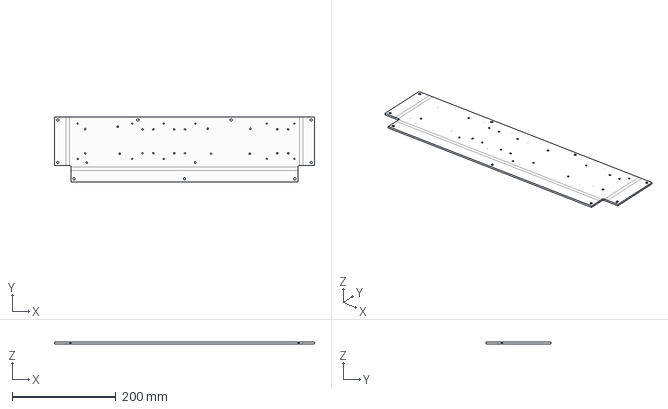
[picture p91: CAD file, 2026-02-16]
KCP2-physical/CAD/KerbalControlPanel/ForManufacture/Aluminum/Panel Dodge Plate/Panel_DodgePlate_v95_FlatPattern.step
501.6 x 125.8 x 3.00 mm
