mountaineerman/KCP2/KCP2-physical/CAD/KerbalControlPanel/ForManufacture/Aluminum/Panel Top Plate/Panel_TopPlate_v96_FlatPattern.step

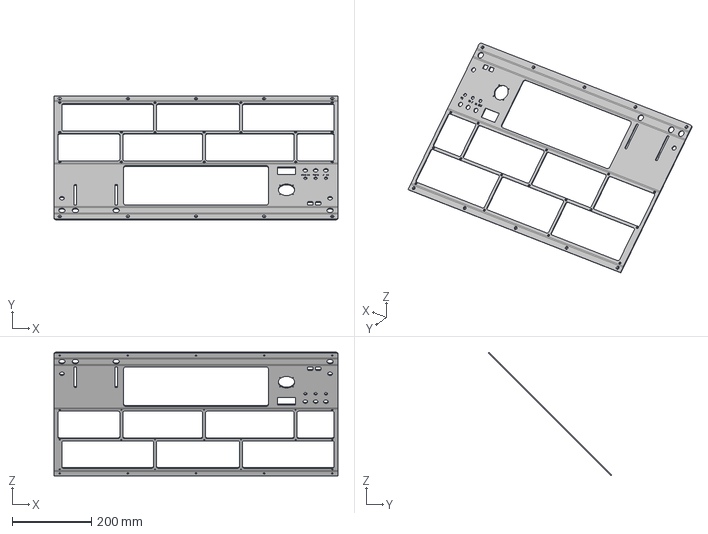
[picture p92: CAD file, 2026-02-16]
KCP2-physical/CAD/KerbalControlPanel/ForManufacture/Aluminum/Panel Top Plate/Panel_TopPlate_v96_FlatPattern.step
717.0 x 312.3 x 312.3 mm
