mountaineerman/KCP2/KCP2-physical/CAD/KerbalControlPanel/ForManufacture/Aluminum/Throttle Bracket/ThrottleBracket_v38_FlatPattern.step

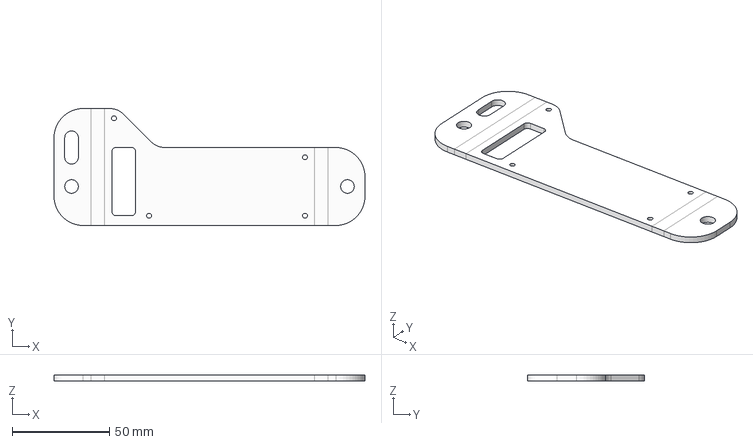
[picture p93: CAD file, 2026-02-16]
KCP2-physical/CAD/KerbalControlPanel/ForManufacture/Aluminum/Throttle Bracket/ThrottleBracket_v38_FlatPattern.step
159.6 x 60.0 x 3.00 mm
