mountaineerman/KCP2/KCP2-physical/CAD/KerbalControlPanel/ForManufacture/ClearAcrylic/Module C/ModuleC_v3.dxf

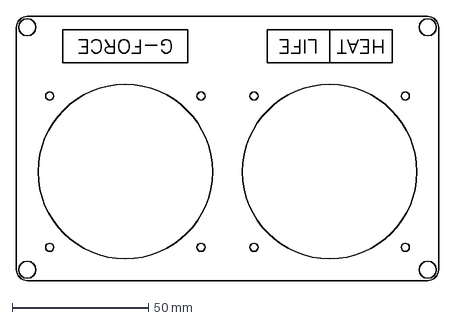
[picture p94: CAD file, 2026-02-16]
KCP2-physical/CAD/KerbalControlPanel/ForManufacture/ClearAcrylic/Module C/ModuleC_v3.dxf
155.0 x 97.0 mm
