mountaineerman/KCP2/KCP2-physical/Documentation/Switch Guards & Toggle Tips - ideas/NASA_switchguard_plain_withholes.stl

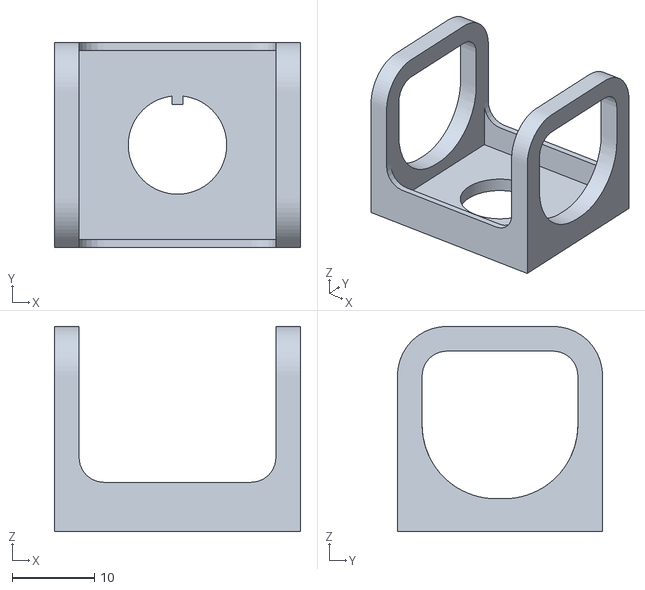
[picture p95: CAD file, 2026-02-16]
KCP2-physical/Documentation/Switch Guards & Toggle Tips - ideas/NASA_switchguard_plain_withholes.stl
30.0 x 25.0 x 25.0
