mountaineerman/KCP2/KCP2-physical/3DPrint/2020-02-05/Switch Guard - 3 v5.stl

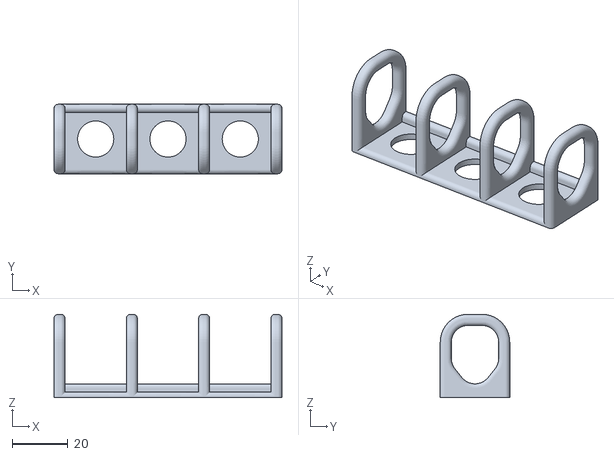
[picture p96: CAD file, 2026-02-16]
KCP2-physical/3DPrint/2020-02-05/Switch Guard - 3 v5.stl
82.0 x 25.0 x 30.0
