mountaineerman/KCP2/KCP2-physical/3DPrint/2020-02-06/v2_HeadingGaugeAdapter.stl

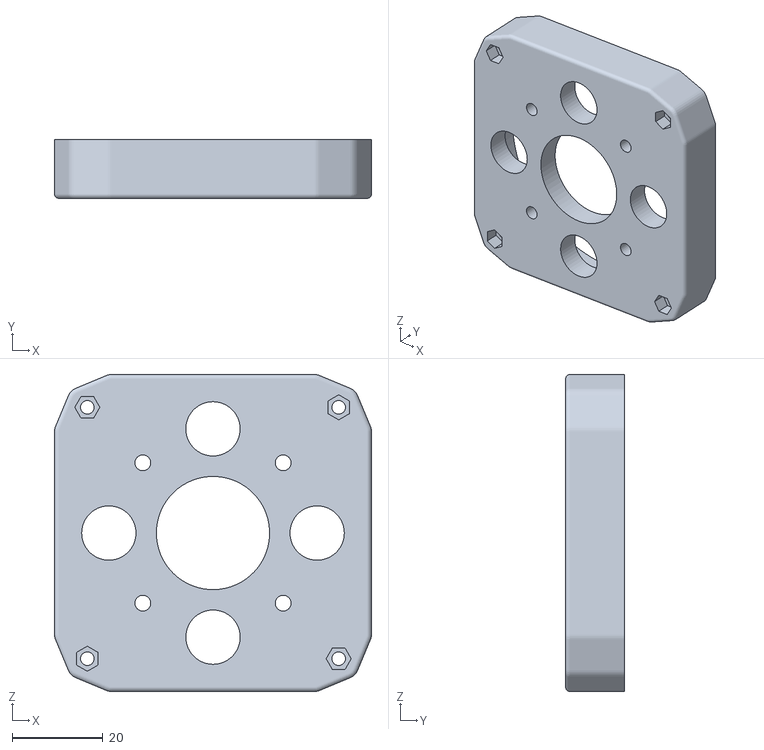
[picture p97: CAD file, 2026-02-16]
KCP2-physical/3DPrint/2020-02-06/v2_HeadingGaugeAdapter.stl
70.0 x 13.0 x 70.0
