mountaineerman/KCP2/KCP2-physical/3DPrint/2020-03-28/PercentLightbox_v3.stl

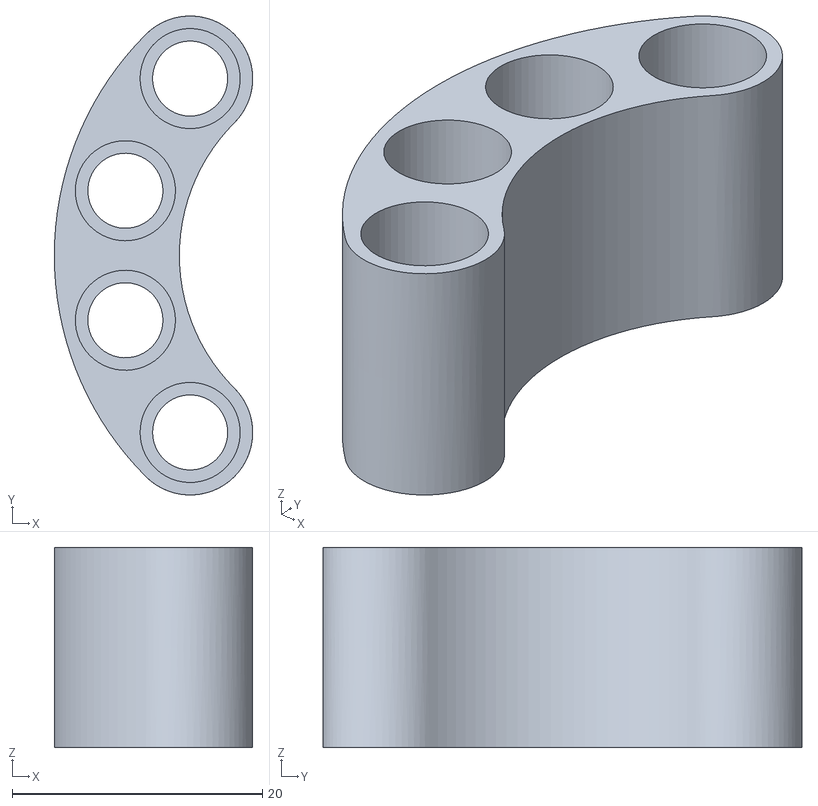
[picture p98: CAD file, 2026-02-16]
KCP2-physical/3DPrint/2020-03-28/PercentLightbox_v3.stl
15.9 x 38.3 x 16.0
