mountaineerman/KCP2/KCP2-physical/3DPrint/2020-11-14/HeadingGaugeBackplate_v7.stl

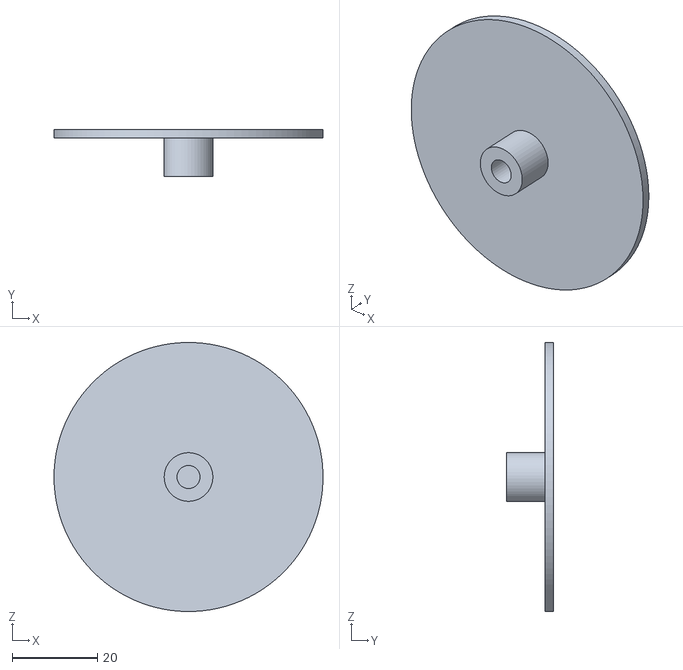
[picture p99: CAD file, 2026-02-16]
KCP2-physical/3DPrint/2020-11-14/HeadingGaugeBackplate_v7.stl
63.0 x 11.0 x 63.0
