mountaineerman/KCP2/KCP2-physical/3DPrint/2020-12-15/CustomNeedle_v11_HoleProto.stl

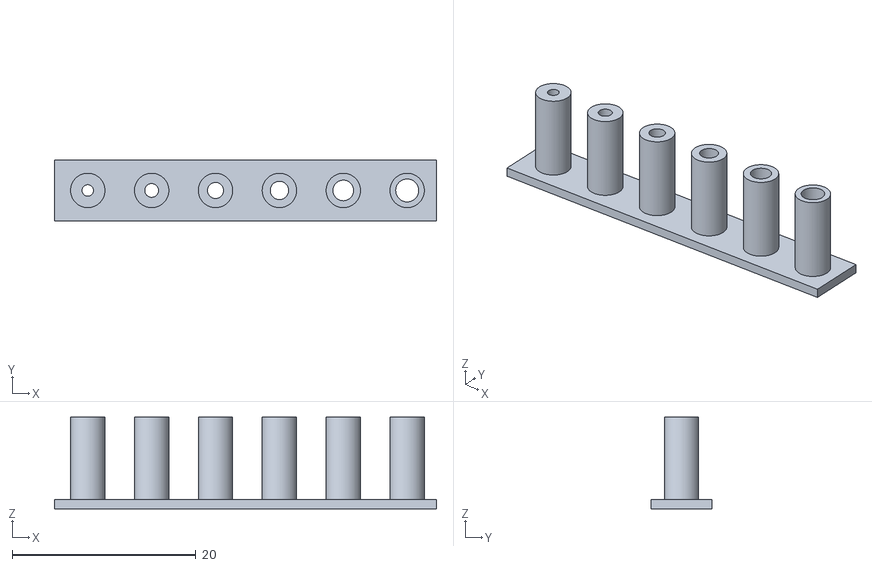
[picture p100: CAD file, 2026-02-16]
KCP2-physical/3DPrint/2020-12-15/CustomNeedle_v11_HoleProto.stl
41.6 x 6.61 x 10.0
