mountaineerman/KCP2/KCP2-physical/3DPrint/2021-01-11/2x_SwitchGuard-1Unit_v4.stl

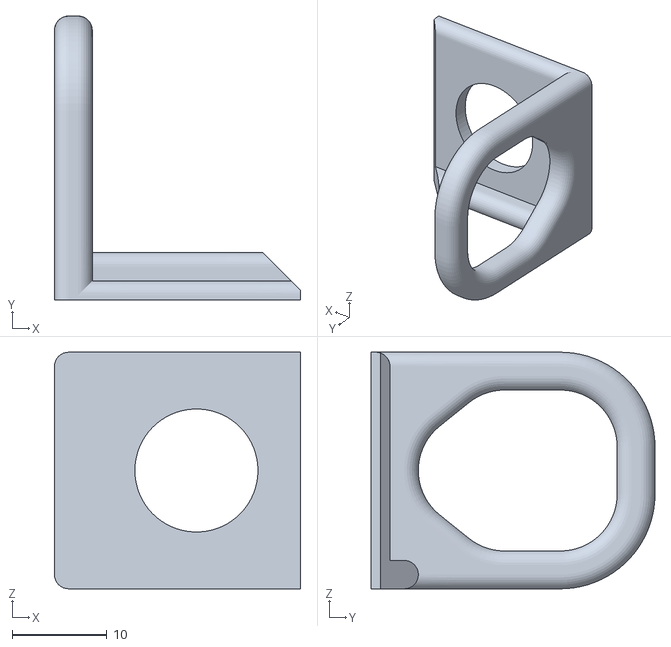
[picture p101: CAD file, 2026-02-16]
KCP2-physical/3DPrint/2021-01-11/2x_SwitchGuard-1Unit_v4.stl
26.0 x 30.0 x 25.0
