mountaineerman/KCP2/KCP2-physical/3DPrint/TBD/15xNeedle.stl

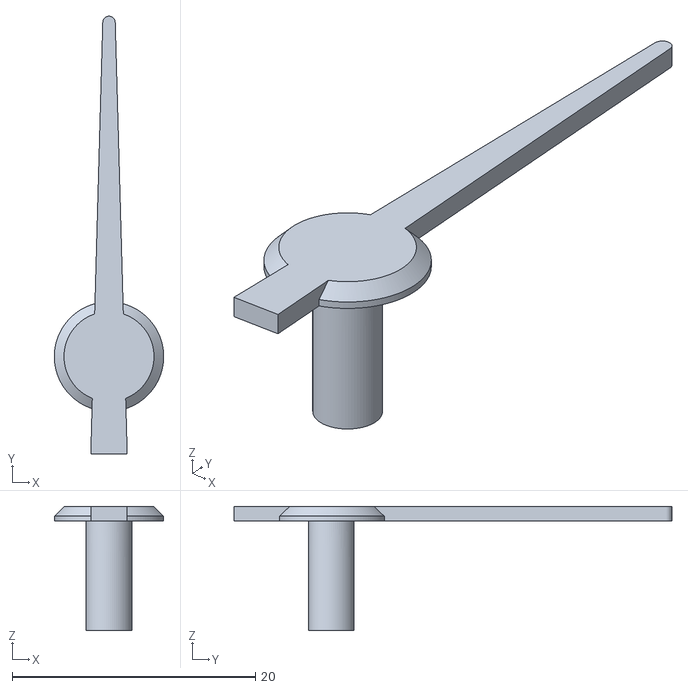
[picture p102: CAD file, 2026-02-16]
KCP2-physical/3DPrint/TBD/15xNeedle.stl
9.00 x 36.0 x 10.2
