mountaineerman/KCP2/KCP2-physical/CAD/ForManufacture/Aluminum/Panel Mounting Plate/Panel_MountingPlate_v96_Folded.step

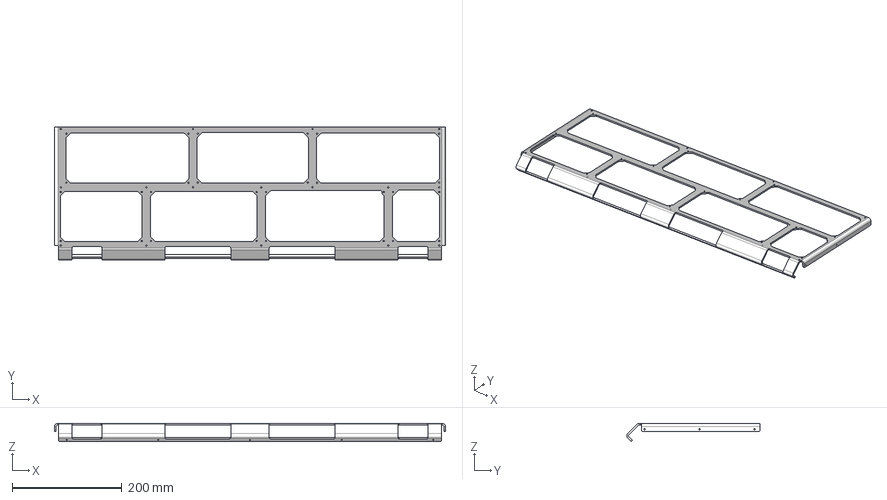
[picture p103: CAD file, 2026-02-16]
KCP2-physical/CAD/ForManufacture/Aluminum/Panel Mounting Plate/Panel_MountingPlate_v96_Folded.step
711.0 x 242.4 x 33.0 mm
