mountaineerman/KCP2/KCP2-physical/CAD/KerbalControlPanel/ForManufacture/Aluminum/Panel Bottom Plate/Panel_BottomPlate_v96_FlatPattern.step

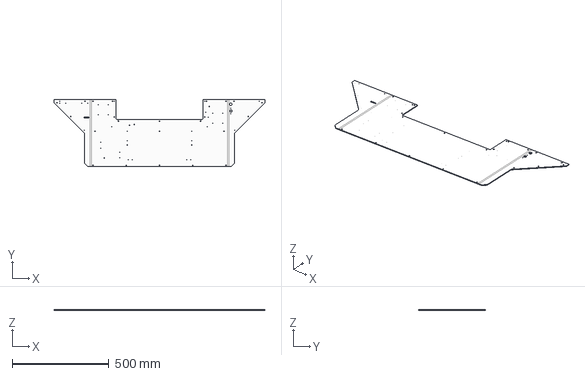
[picture p104: CAD file, 2026-02-16]
KCP2-physical/CAD/KerbalControlPanel/ForManufacture/Aluminum/Panel Bottom Plate/Panel_BottomPlate_v96_FlatPattern.step
1092.2 x 346.6 x 3.00 mm
