mountaineerman/KCP2/KCP2-physical/3DPrint/2020-02-06/v2_HeadingGaugeCover.stl

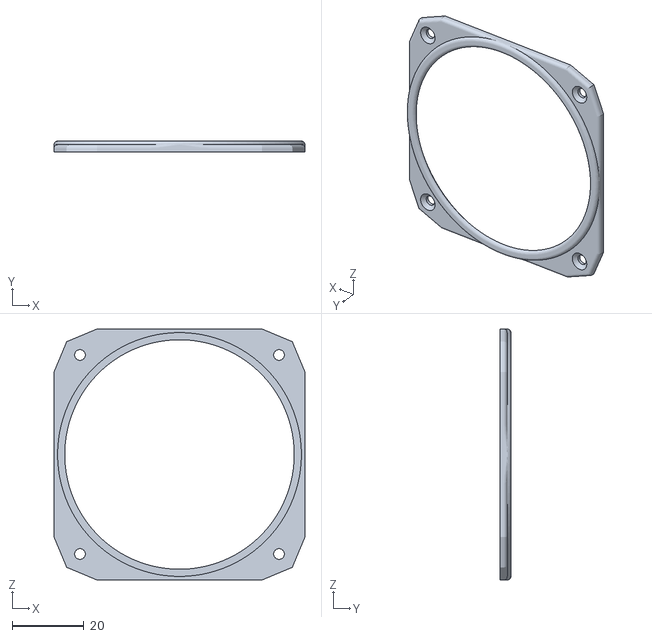
[picture p106: CAD file, 2026-02-16]
KCP2-physical/3DPrint/2020-02-06/v2_HeadingGaugeCover.stl
70.0 x 3.00 x 70.0
