mountaineerman/KCP2/KCP2-physical/3DPrint/2020-03-28/3POSNarrowLightbox_v4.stl

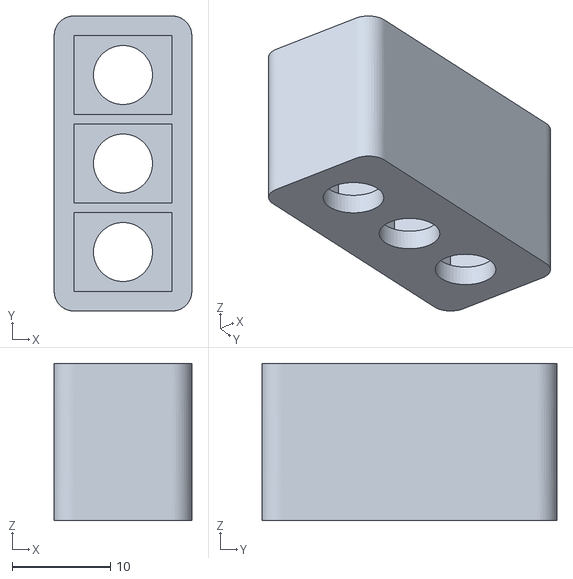
[picture p107: CAD file, 2026-02-16]
KCP2-physical/3DPrint/2020-03-28/3POSNarrowLightbox_v4.stl
14.0 x 30.0 x 16.0
