mountaineerman/KCP2/KCP2-physical/3DPrint/2020-10-25/4POSTwistSwitchHandle_v2.stl

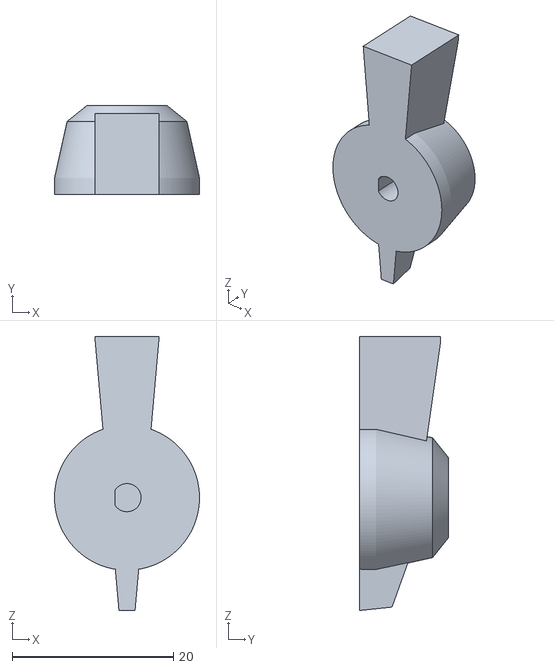
[picture p108: CAD file, 2026-02-16]
KCP2-physical/3DPrint/2020-10-25/4POSTwistSwitchHandle_v2.stl
18.0 x 11.0 x 34.0
