mountaineerman/KCP2/KCP2-physical/3DPrint/2020-11-14/4POS_Handle_v4.stl

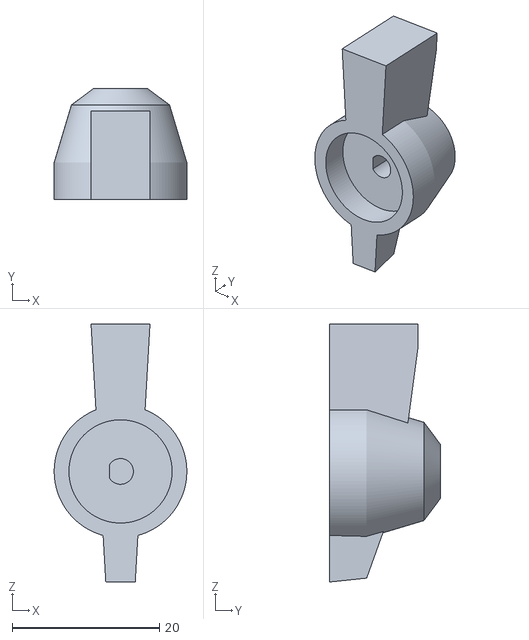
[picture p109: CAD file, 2026-02-16]
KCP2-physical/3DPrint/2020-11-14/4POS_Handle_v4.stl
18.0 x 15.0 x 35.0
