mountaineerman/KCP2/KCP2-physical/3DPrint/2020-12-15/CustomNeedle_v11_Proto2.stl

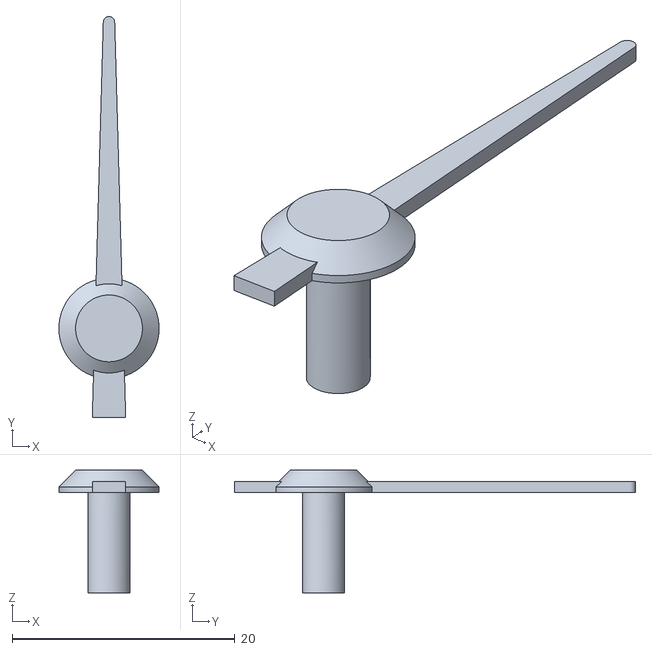
[picture p110: CAD file, 2026-02-16]
KCP2-physical/3DPrint/2020-12-15/CustomNeedle_v11_Proto2.stl
9.00 x 36.0 x 11.0
