mountaineerman/KCP2/KCP2-physical/CAD/ForManufacture/Aluminum/Panel Top Plate/Panel_TopPlate_v96_Folded.step

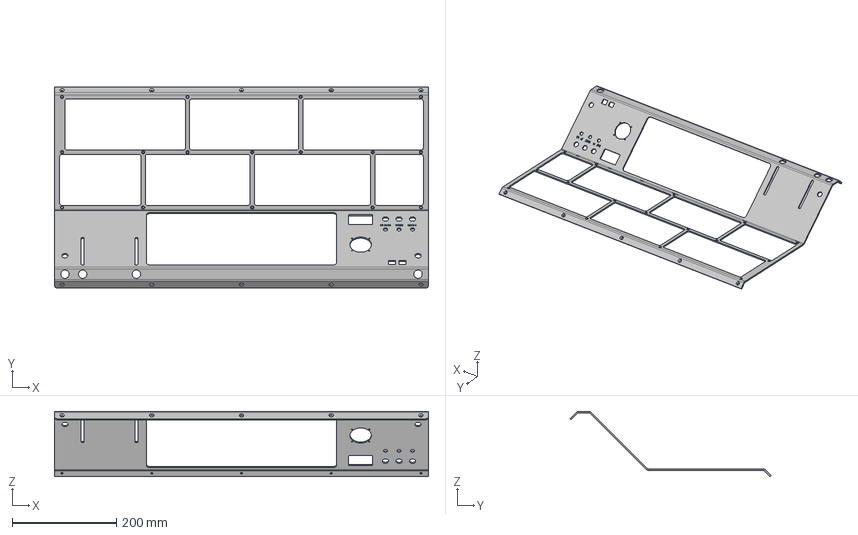
[picture p111: CAD file, 2026-02-16]
KCP2-physical/CAD/ForManufacture/Aluminum/Panel Top Plate/Panel_TopPlate_v96_Folded.step
717.0 x 385.7 x 125.0 mm
