mountaineerman/KCP2/KCP2-physical/Documentation/Switch Guards & Toggle Tips - ideas/NASA_switchtip_plain.stl

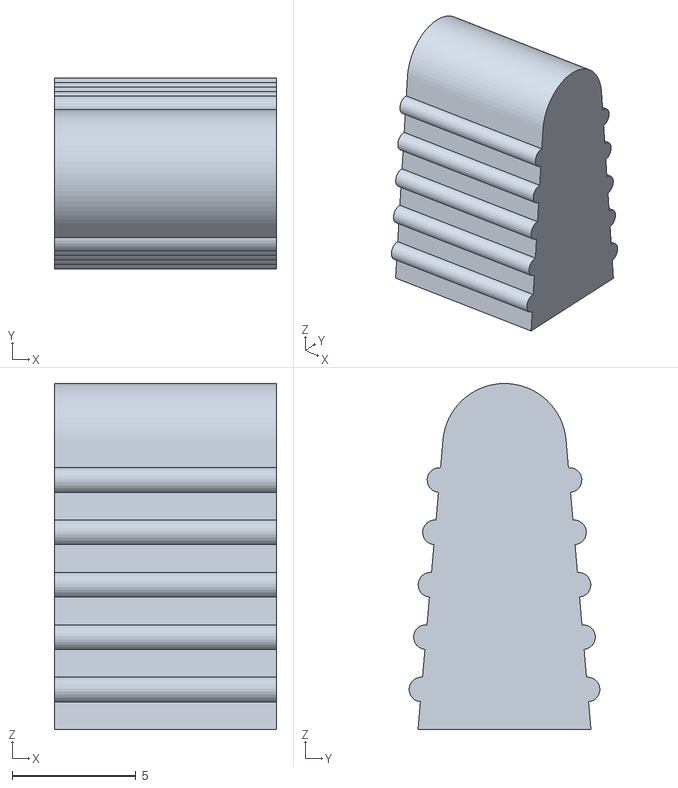
[picture p112: CAD file, 2026-02-16]
KCP2-physical/Documentation/Switch Guards & Toggle Tips - ideas/NASA_switchtip_plain.stl
9.00 x 7.72 x 14.0
