mountaineerman/KCP2/KCP2-physical/3DPrint/2020-02-05/Switch Guard - 7 v3.stl

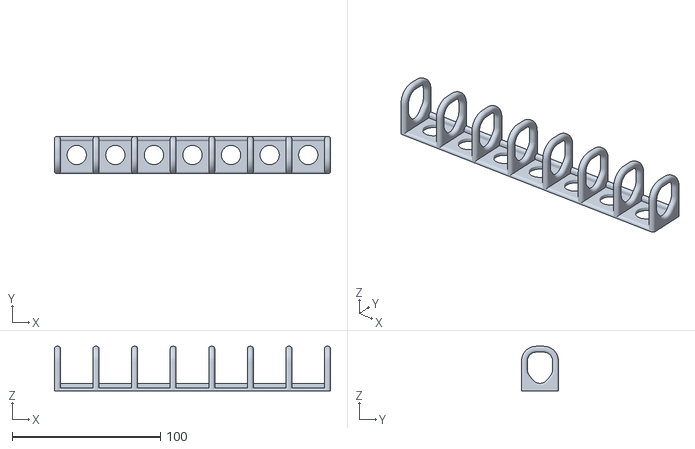
[picture p113: CAD file, 2026-02-16]
KCP2-physical/3DPrint/2020-02-05/Switch Guard - 7 v3.stl
186.0 x 25.0 x 30.0
