mountaineerman/KCP2/KCP2-physical/3DPrint/2020-03-28/Gauge1Lightbox_v5.stl

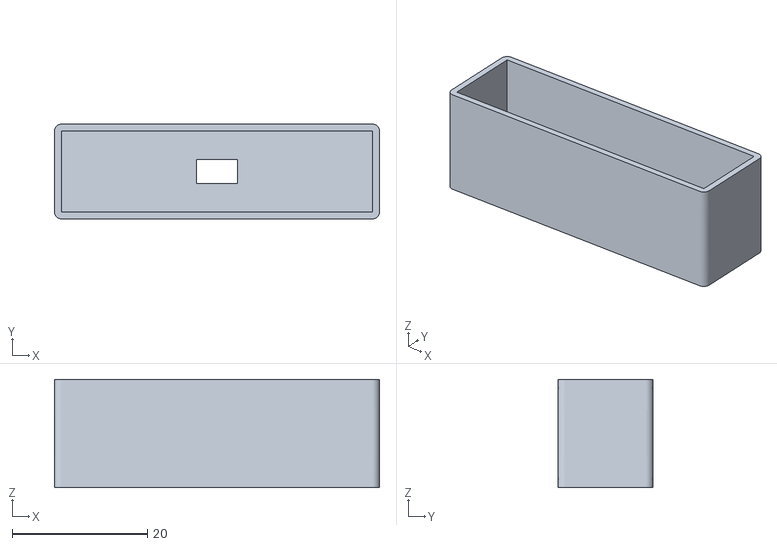
[picture p116: CAD file, 2026-02-16]
KCP2-physical/3DPrint/2020-03-28/Gauge1Lightbox_v5.stl
48.0 x 14.0 x 16.0
