mountaineerman/KCP2/KCP2-physical/3DPrint/2020-11-14/Lightbox_Altitude_v9.stl

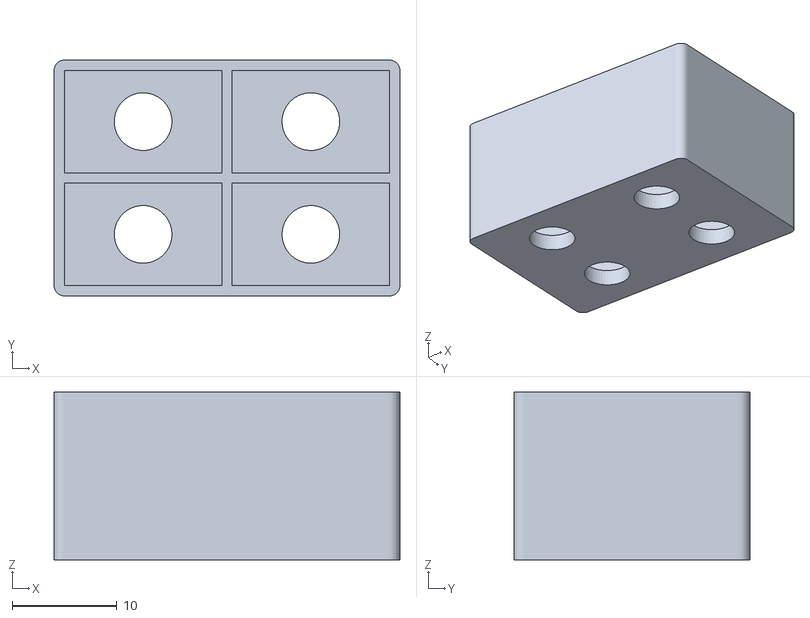
[picture p118: CAD file, 2026-02-16]
KCP2-physical/3DPrint/2020-11-14/Lightbox_Altitude_v9.stl
33.0 x 22.5 x 16.0
