mountaineerman/KCP2/KCP2-physical/Documentation/Switch Guards & Toggle Tips - ideas/NASA_switchguard_smooth_regpin.stl

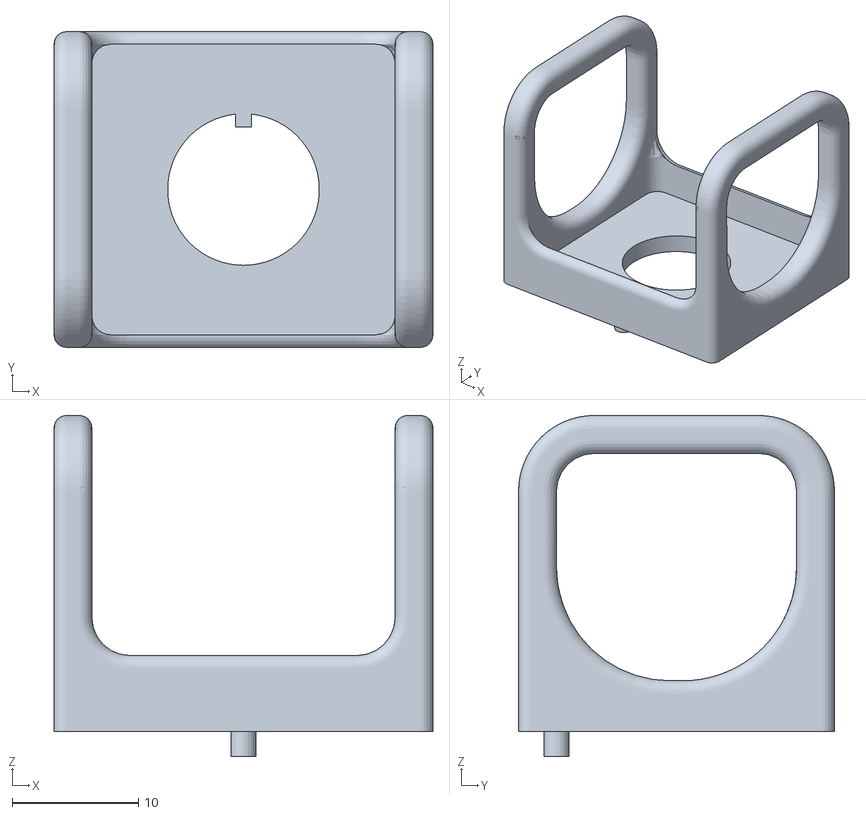
[picture p119: CAD file, 2026-02-16]
KCP2-physical/Documentation/Switch Guards & Toggle Tips - ideas/NASA_switchguard_smooth_regpin.stl
30.0 x 25.0 x 27.0
