mountaineerman/KCP2/KCP2-physical/3DPrint/2020-02-06/Switch Tip (S).stl

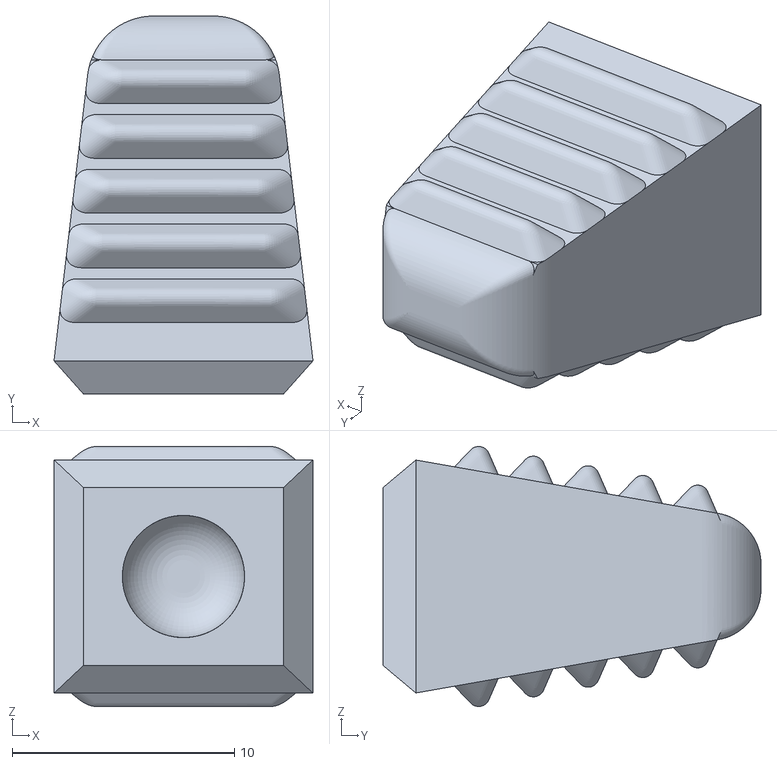
[picture p120: CAD file, 2026-02-16]
KCP2-physical/3DPrint/2020-02-06/Switch Tip (S).stl
11.6 x 17.0 x 11.7
