mountaineerman/KCP2/KCP2-physical/3DPrint/2020-03-28/3POSWideLightbox_v1.stl

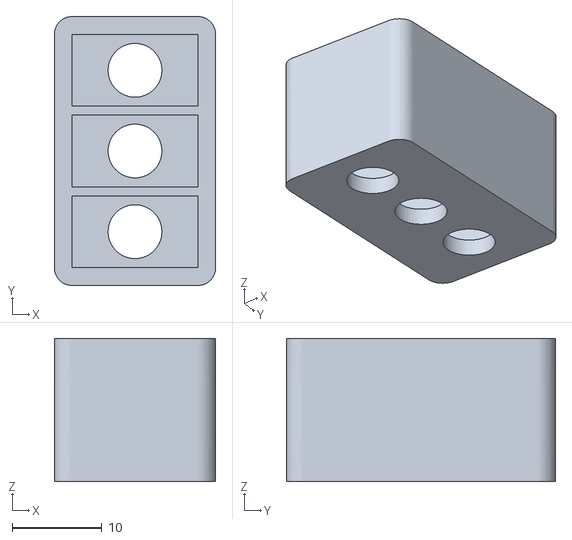
[picture p121: CAD file, 2026-02-16]
KCP2-physical/3DPrint/2020-03-28/3POSWideLightbox_v1.stl
18.0 x 30.0 x 16.0
