mountaineerman/KCP2/KCP2-physical/3DPrint/2020-10-25/Lightbox2Light_v6.stl

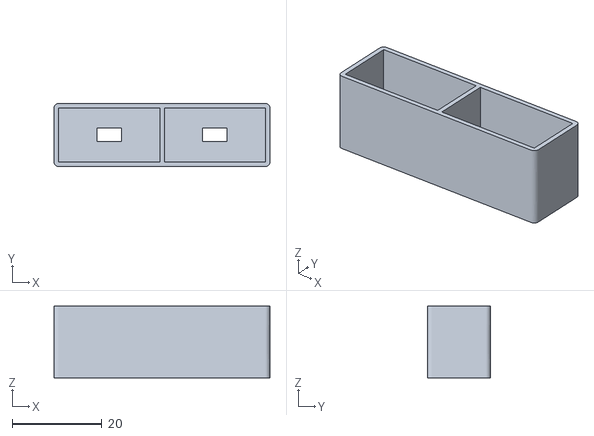
[picture p122: CAD file, 2026-02-16]
KCP2-physical/3DPrint/2020-10-25/Lightbox2Light_v6.stl
48.0 x 14.0 x 16.0
