mountaineerman/KCP2/KCP2-physical/3DPrint/2021-01-11/1x_LightboxPercent_v5.stl

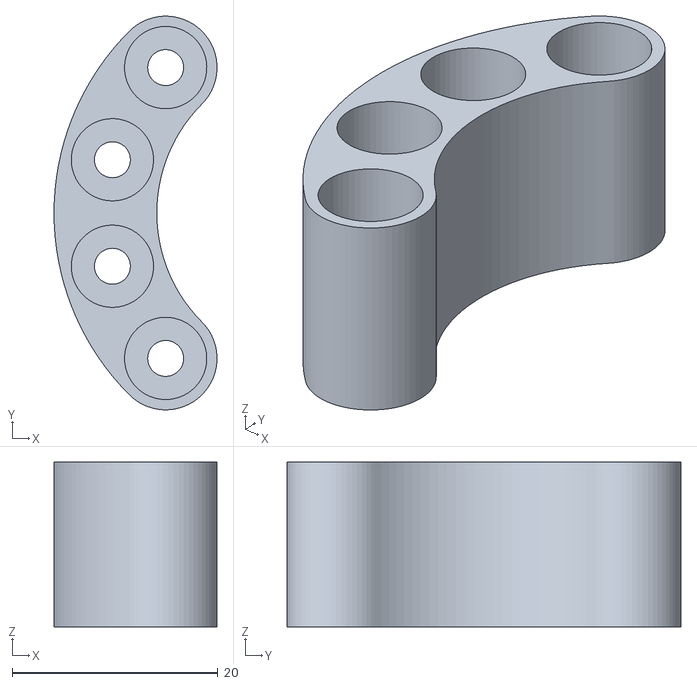
[picture p123: CAD file, 2026-02-16]
KCP2-physical/3DPrint/2021-01-11/1x_LightboxPercent_v5.stl
15.9 x 38.3 x 16.0
