mountaineerman/KCP2/KCP2-physical/3DPrint/2020-02-06/v2_AnalogGaugeAdapter.stl

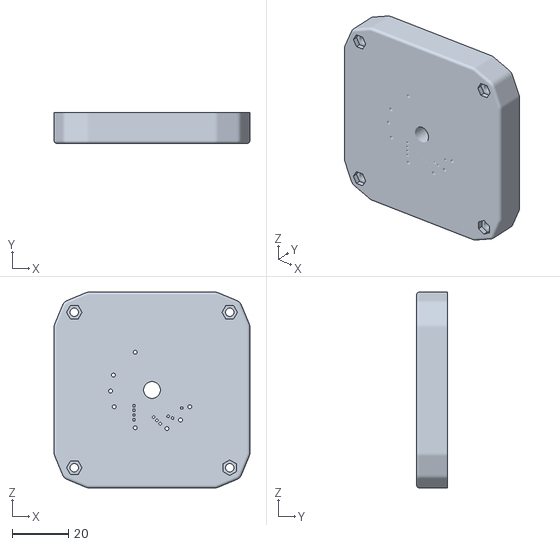
[picture p124: CAD file, 2026-02-16]
KCP2-physical/3DPrint/2020-02-06/v2_AnalogGaugeAdapter.stl
70.0 x 11.0 x 70.0
