mountaineerman/KCP2/KCP2-physical/3DPrint/2020-03-28/AltitudeLightbox_v5.stl

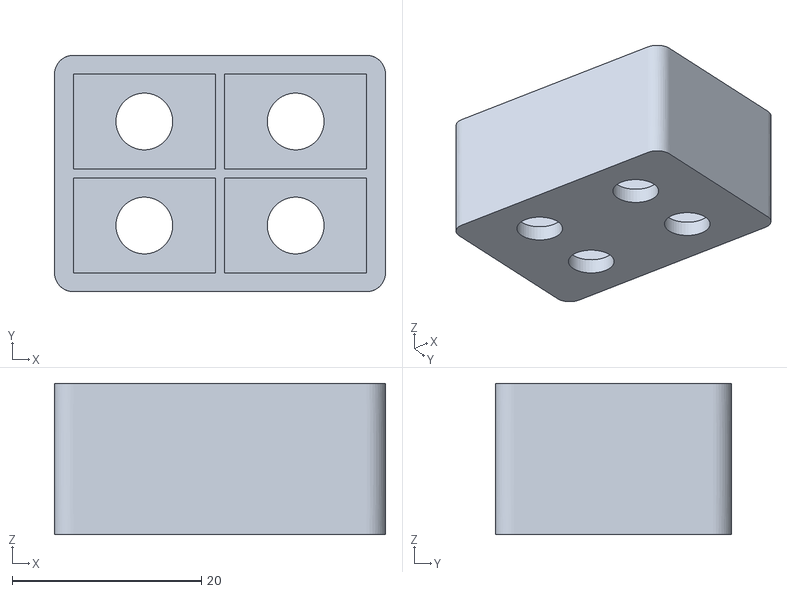
[picture p125: CAD file, 2026-02-16]
KCP2-physical/3DPrint/2020-03-28/AltitudeLightbox_v5.stl
35.0 x 25.0 x 16.0
