mountaineerman/KCP2/KCP2-physical/3DPrint/2020-10-25/Lightbox3POSNarrow_v5.stl

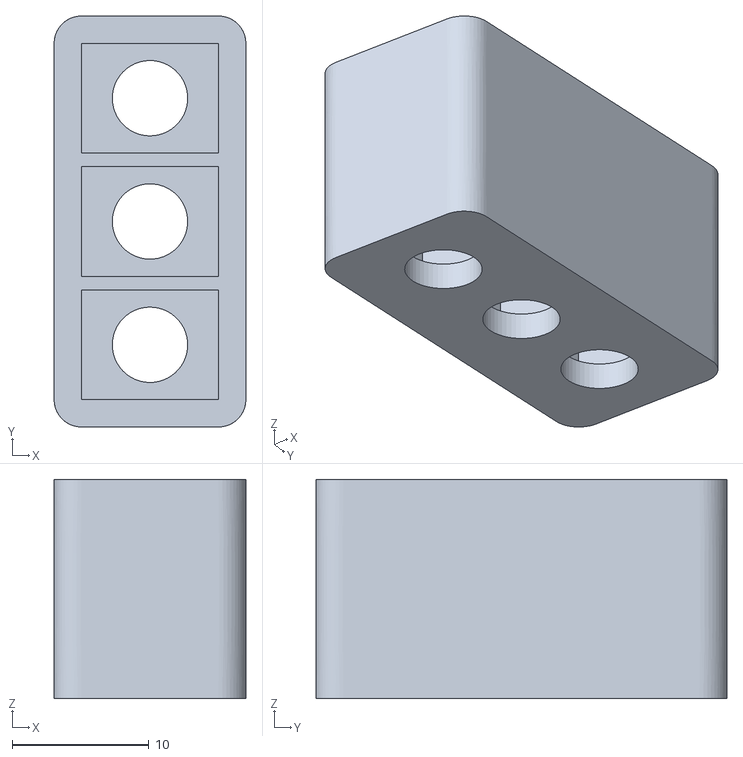
[picture p126: CAD file, 2026-02-16]
KCP2-physical/3DPrint/2020-10-25/Lightbox3POSNarrow_v5.stl
14.0 x 30.0 x 16.0
