mountaineerman/KCP2/KCP2-physical/3DPrint/2020-10-25/LightboxAltitude_v6.stl

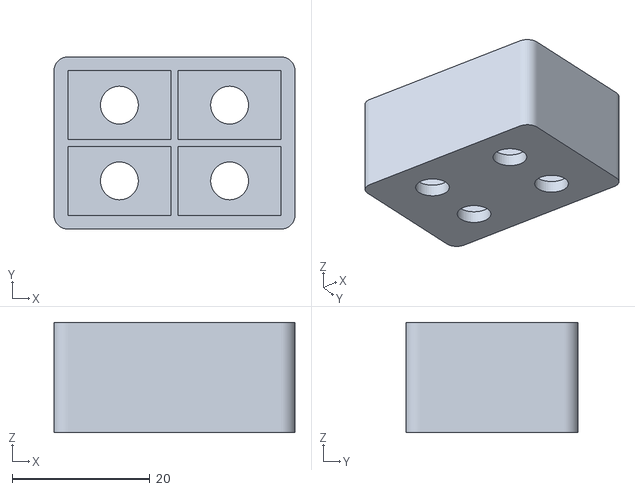
[picture p127: CAD file, 2026-02-16]
KCP2-physical/3DPrint/2020-10-25/LightboxAltitude_v6.stl
35.0 x 25.0 x 16.0
