mountaineerman/KCP2/KCP2-physical/3DPrint/2020-10-25/CustomNeedle_v6_Proto2.stl

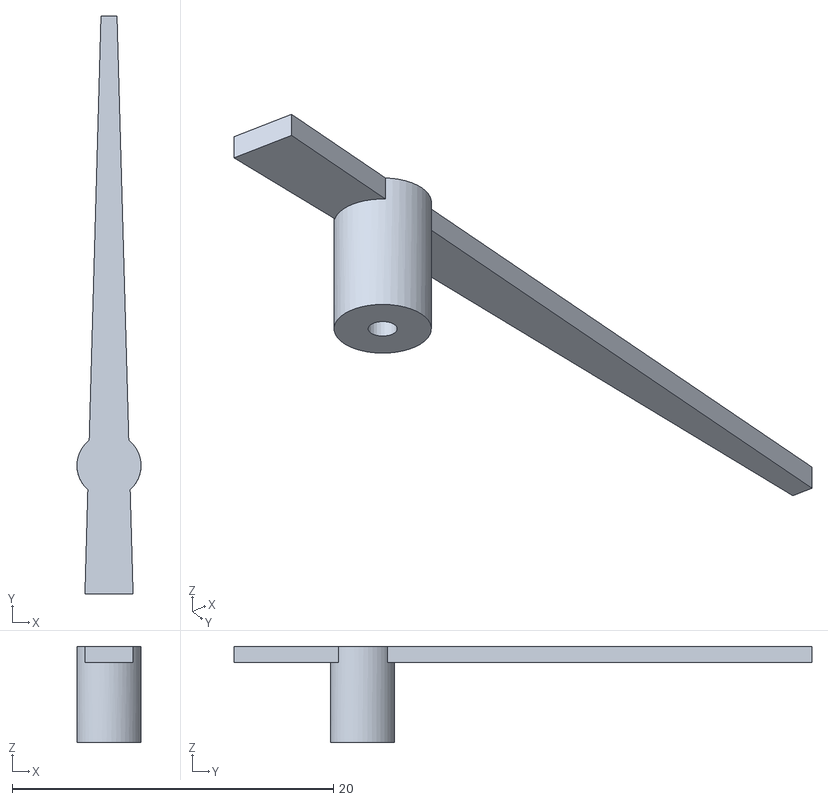
[picture p128: CAD file, 2026-02-16]
KCP2-physical/3DPrint/2020-10-25/CustomNeedle_v6_Proto2.stl
4.00 x 36.0 x 6.00
