mountaineerman/KCP2/KCP2-physical/3DPrint/2020-10-25/CustomNeedle_v6_Proto1.stl

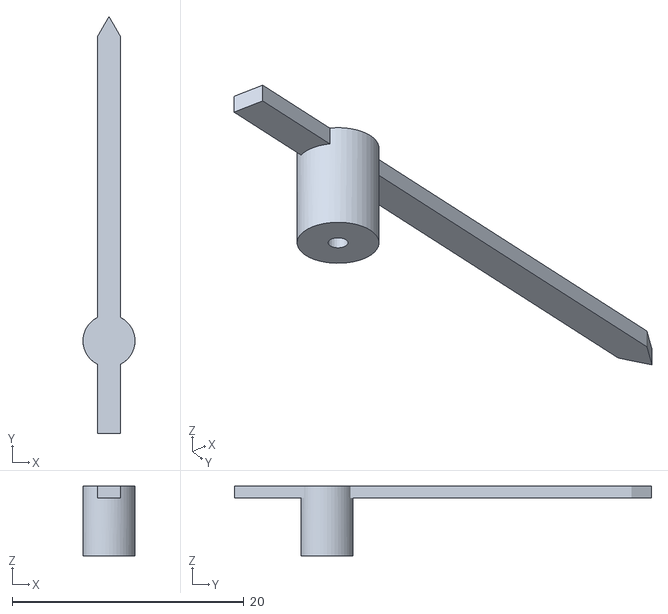
[picture p129: CAD file, 2026-02-16]
KCP2-physical/3DPrint/2020-10-25/CustomNeedle_v6_Proto1.stl
4.50 x 36.0 x 6.00
