mountaineerman/KCP2/KCP2-physical/PrintForWorkshop/FastenerConversionChart_ImperialMetric.PNG

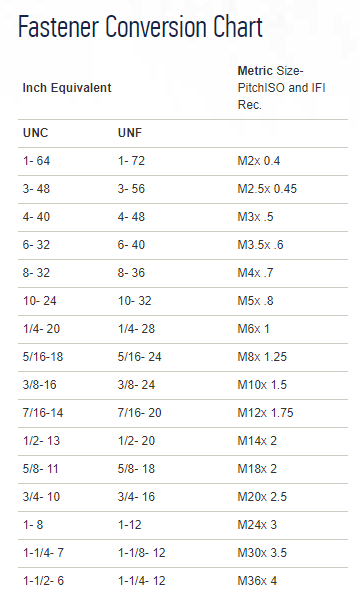
KCP2-physical/PrintForWorkshop/FastenerConversionChart_ImperialMetric.PNG
