mountaineerman/KCP2/KCP2-physical/Photos/Siegfried'sFixes.PNG

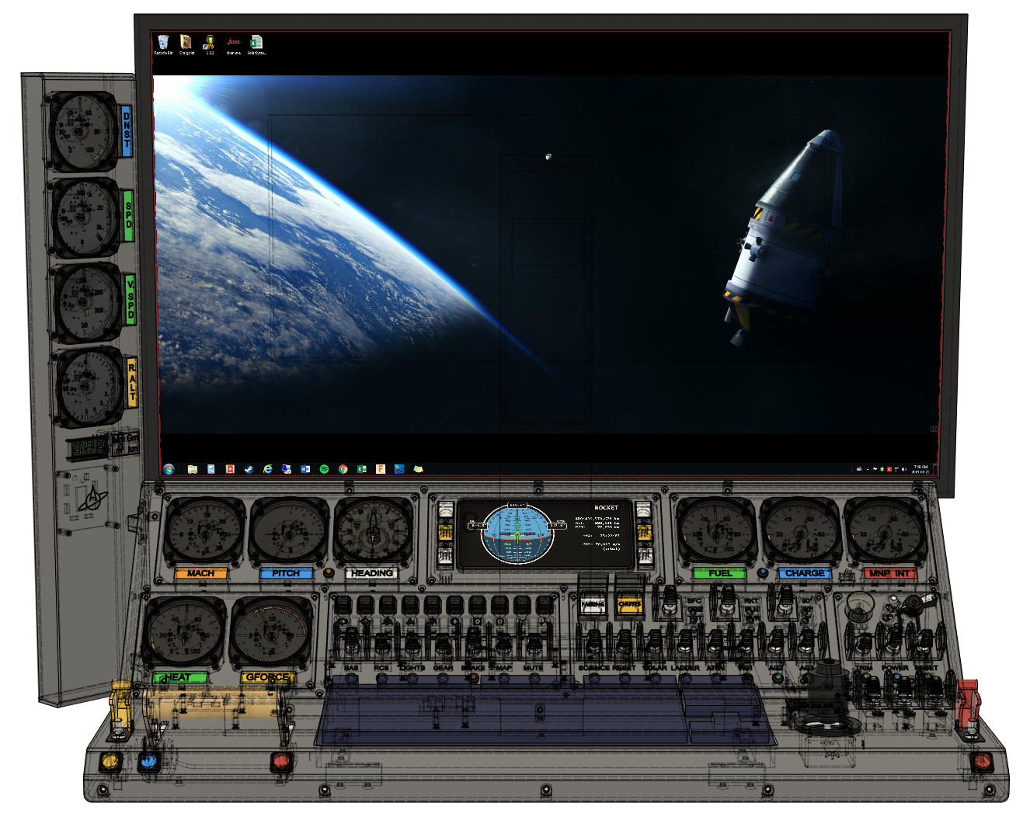
KCP2-physical/Photos/Siegfried'sFixes.PNG
