mountaineerman/KCP2/KCP2-physical/CAD/ForManufacture/ClearAcrylic/AnalogGaugeClusterScreen_Rev0_v3.pdf

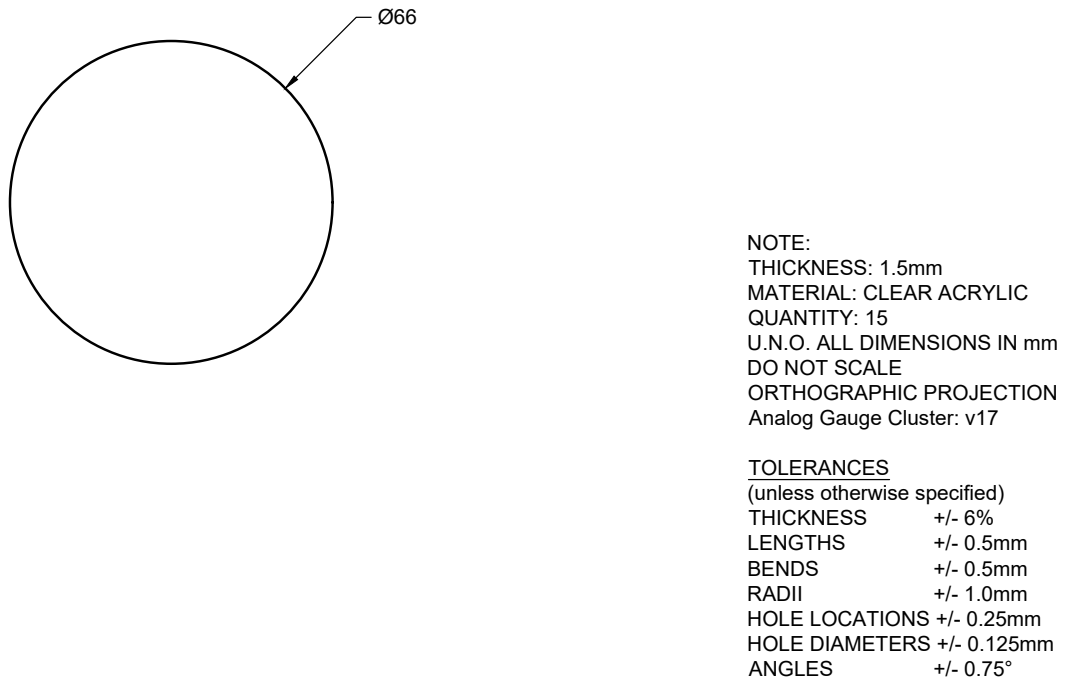
[picture p138: page 1]
SCALE 1:1; DRAWN 2020-11-13; REV 0; SHEET 1/1; THICKNESS; LENGTHS; BENDS; RADII; ANGLES

NOTE:
THICKNESS: 1.5mm
MATERIAL: CLEAR ACRYLIC
QUANTITY: 15
U.N.O. ALL DIMENSIONS IN mm
DO NOT SCALE
ORTHOGRAPHIC PROJECTION
Analog Gauge Cluster: v17

TOLERANCES
(unless otherwise specified)
HOLE LOCATIONS +/- 0.25mm
HOLE DIAMETERS +/- 0.125mm

PROJECT
Kerbal Control Panel - Mk II

TITLE
Analog Gauge Cluster Screen
