mountaineerman/KCP2/KCP2-physical/CAD/ForManufacture/Wood/ThrottleHandle_Rev0_v5.pdf

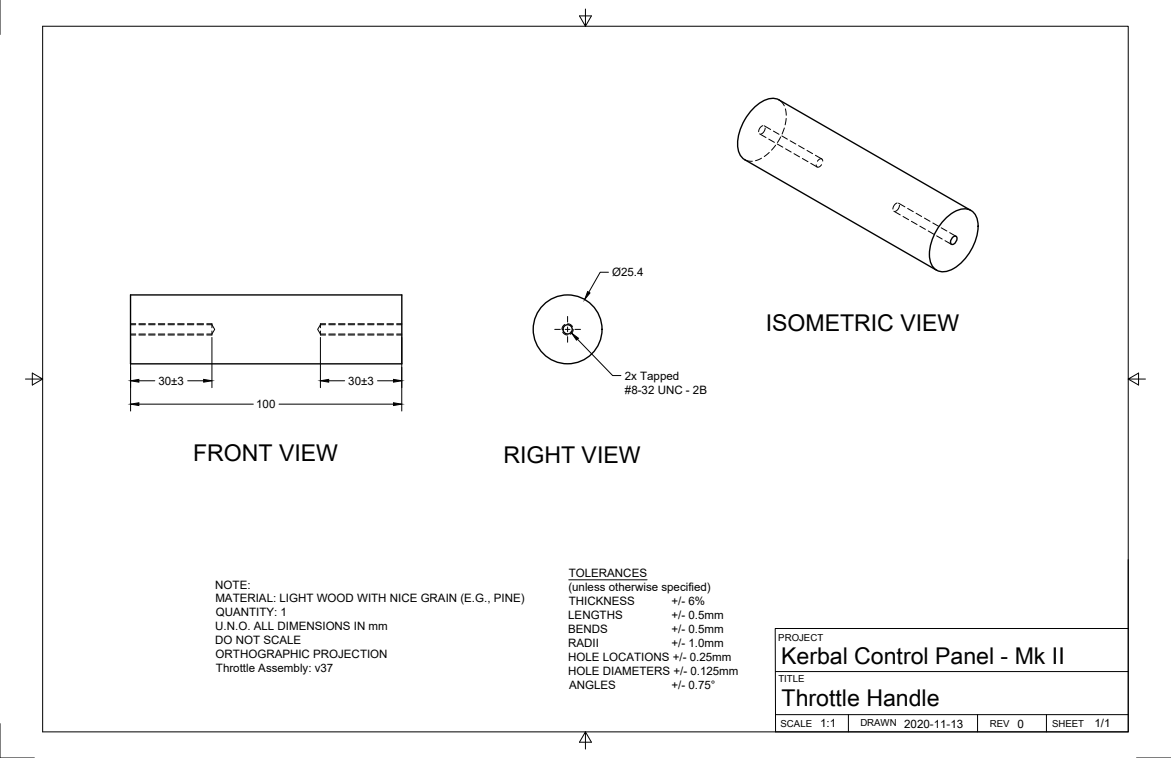
[picture p139: page 1]
SCALE 1:1; DRAWN 2020-11-13; REV 0; SHEET 1/1; Throttle Handle; THICKNESS; LENGTHS; BENDS; RADII; ANGLES; FRONT VIEW; RIGHT VIEW; ISOMETRIC VIEW; 2x Tapped #8-32 UNC - 2B

TOLERANCES
(unless otherwise specified)
HOLE LOCATIONS +/- 0.25mm
HOLE DIAMETERS +/- 0.125mm

NOTE:
MATERIAL: LIGHT WOOD WITH NICE GRAIN (E.G., PINE)
QUANTITY: 1
U.N.O. ALL DIMENSIONS IN mm
DO NOT SCALE
ORTHOGRAPHIC PROJECTION
Throttle Assembly: v37

PROJECT
Kerbal Control Panel - Mk II
