mountaineerman/KCP2/KCP2-physical/CAD/ForManufacture/Aluminum/Gauge Tower Back Panel/GaugeTower_BackPanel_Rev2_v5.pdf

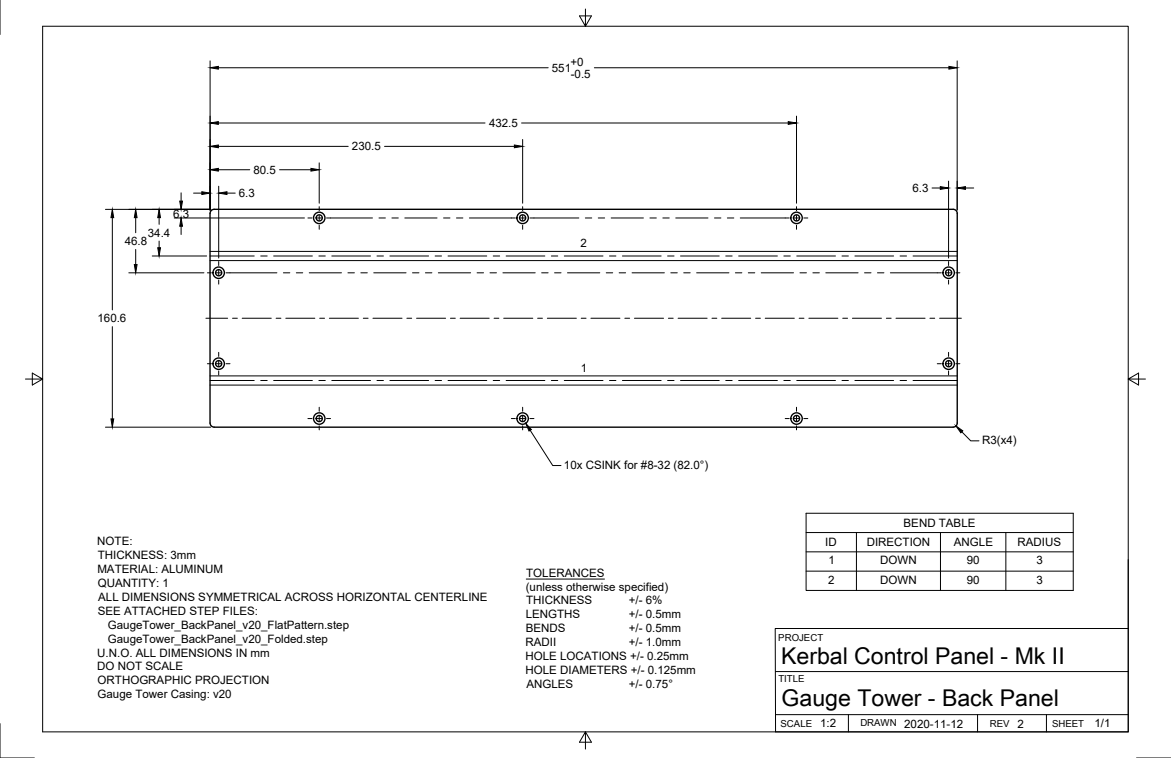
[picture p140: page 1]
SCALE 1:2; DRAWN 2020-11-12; REV 2; SHEET 1/1; THICKNESS; LENGTHS; BENDS; RADII; ANGLES; BEND TABLE; 10x CSINK for #8-32 (82.0°)

NOTE:
THICKNESS: 3mm
MATERIAL: ALUMINUM
QUANTITY: 1
ALL DIMENSIONS SYMMETRICAL ACROSS HORIZONTAL CENTERLINE
SEE ATTACHED STEP FILES:
GaugeTower_BackPanel_v20_FlatPattern.step
GaugeTower_BackPanel_v20_Folded.step
U.N.O. ALL DIMENSIONS IN mm
DO NOT SCALE
ORTHOGRAPHIC PROJECTION
Gauge Tower Casing: v20

ID | DIRECTION | ANGLE | RADIUS
1 | DOWN | 90 | 3
2 | DOWN | 90 | 3

TOLERANCES
(unless otherwise specified)
HOLE LOCATIONS +/- 0.25mm
HOLE DIAMETERS +/- 0.125mm

PROJECT
Kerbal Control Panel - Mk II

TITLE
Gauge Tower - Back Panel
