mountaineerman/KCP2/KCP2-physical/CAD/ForManufacture/Aluminum/Gauge Tower Front Panel/GaugeTower_FrontPanel_Rev2_v11.pdf

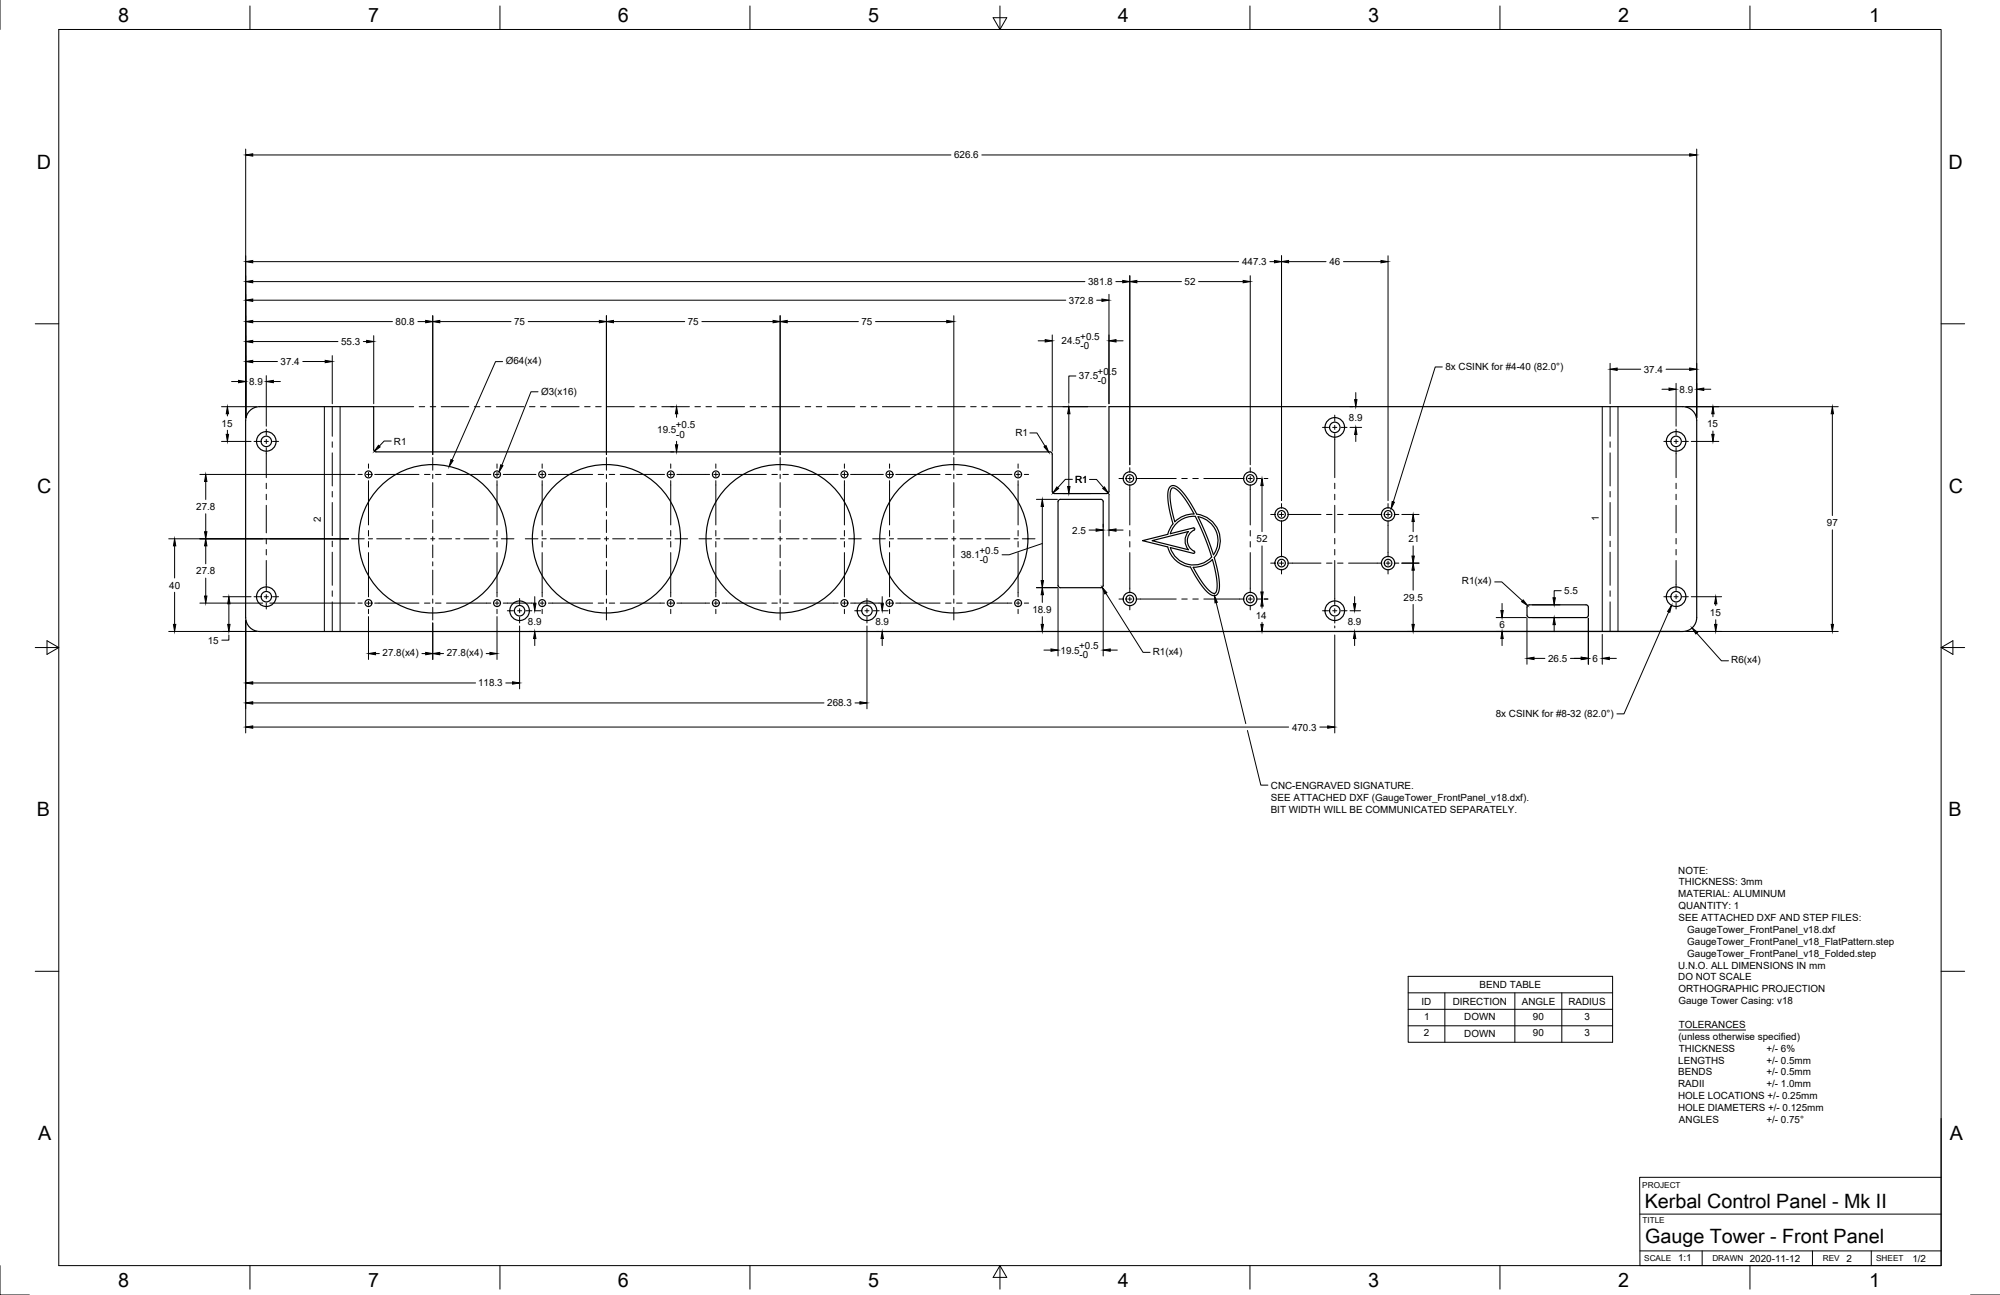
[picture p141: page 1]
SCALE 1:1; DRAWN 2020-11-12; REV 2; SHEET 1/2; BEND TABLE; THICKNESS; LENGTHS; BENDS; RADII; ANGLES; 8x CSINK for #4-40 (82.0°); 8x CSINK for #8-32 (82.0°)

CNC-ENGRAVED SIGNATURE.
SEE ATTACHED DXF (GaugeTower_FrontPanel_v18.dxf).
BIT WIDTH WILL BE COMMUNICATED SEPARATELY.

NOTE:
THICKNESS: 3mm
MATERIAL: ALUMINUM
QUANTITY: 1
SEE ATTACHED DXF AND STEP FILES:
GaugeTower_FrontPanel_v18.dxf
GaugeTower_FrontPanel_v18_FlatPattern.step
GaugeTower_FrontPanel_v18_Folded.step
U.N.O. ALL DIMENSIONS IN mm
DO NOT SCALE
ORTHOGRAPHIC PROJECTION
Gauge Tower Casing: v18

ID | DIRECTION | ANGLE | RADIUS
1 | DOWN | 90 | 3
2 | DOWN | 90 | 3

TOLERANCES
(unless otherwise specified)
HOLE LOCATIONS +/- 0.25mm
HOLE DIAMETERS +/- 0.125mm

PROJECT
Kerbal Control Panel - Mk II

TITLE
Gauge Tower - Front Panel

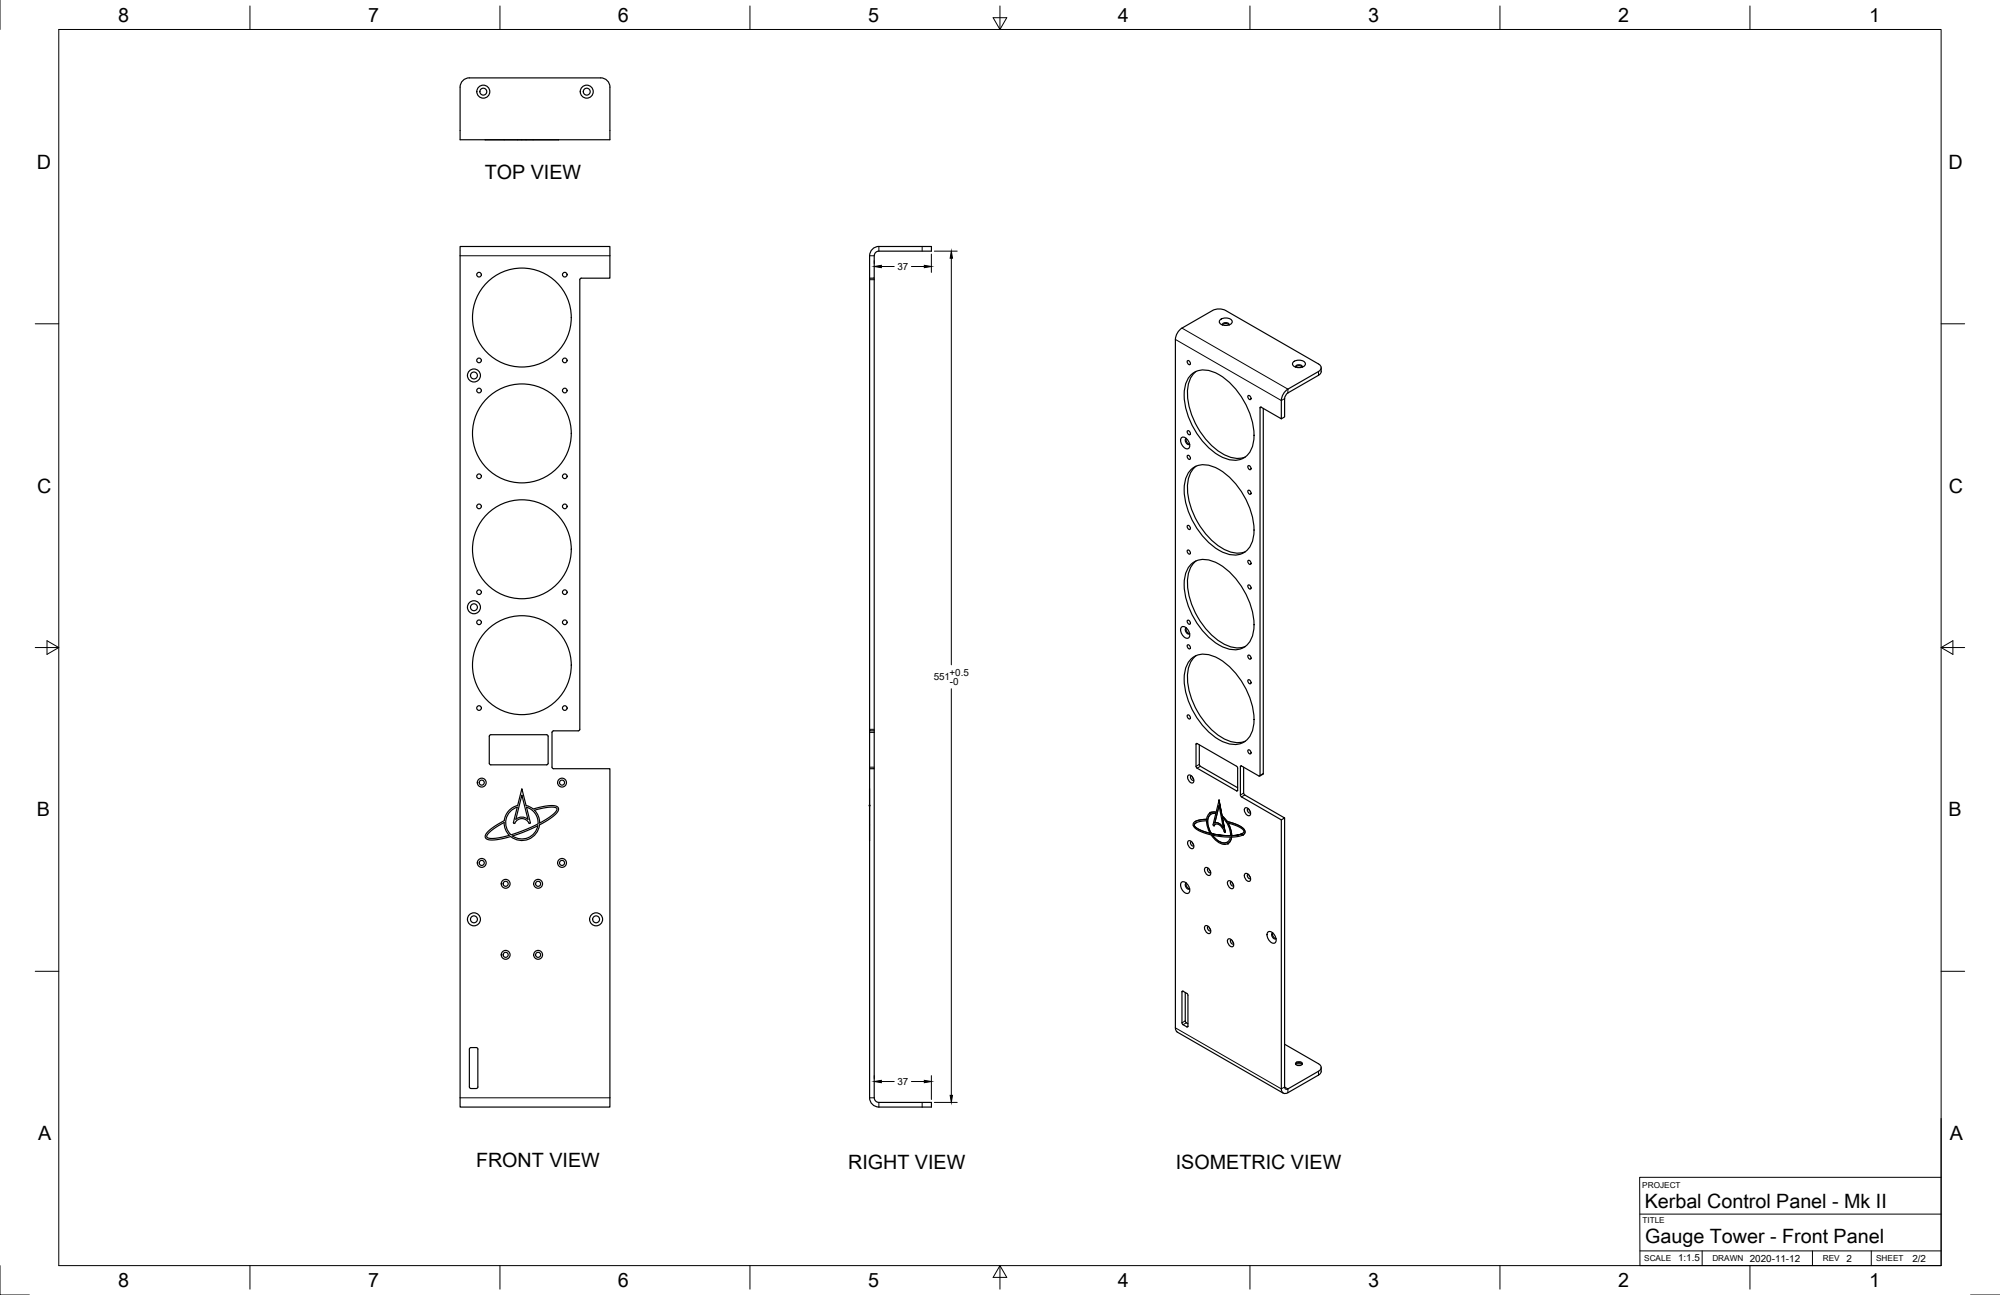
[picture p142: page 2]
SCALE 1:1.5; DRAWN 2020-11-12; REV 2; SHEET 2/2; FRONT VIEW; TOP VIEW; RIGHT VIEW; ISOMETRIC VIEW

PROJECT
Kerbal Control Panel - Mk II

TITLE
Gauge Tower - Front Panel
