mountaineerman/KCP2/KCP2-physical/CAD/ForManufacture/Aluminum/Keyboard Pillar/KeyboardPillar_Rev0_v5.pdf

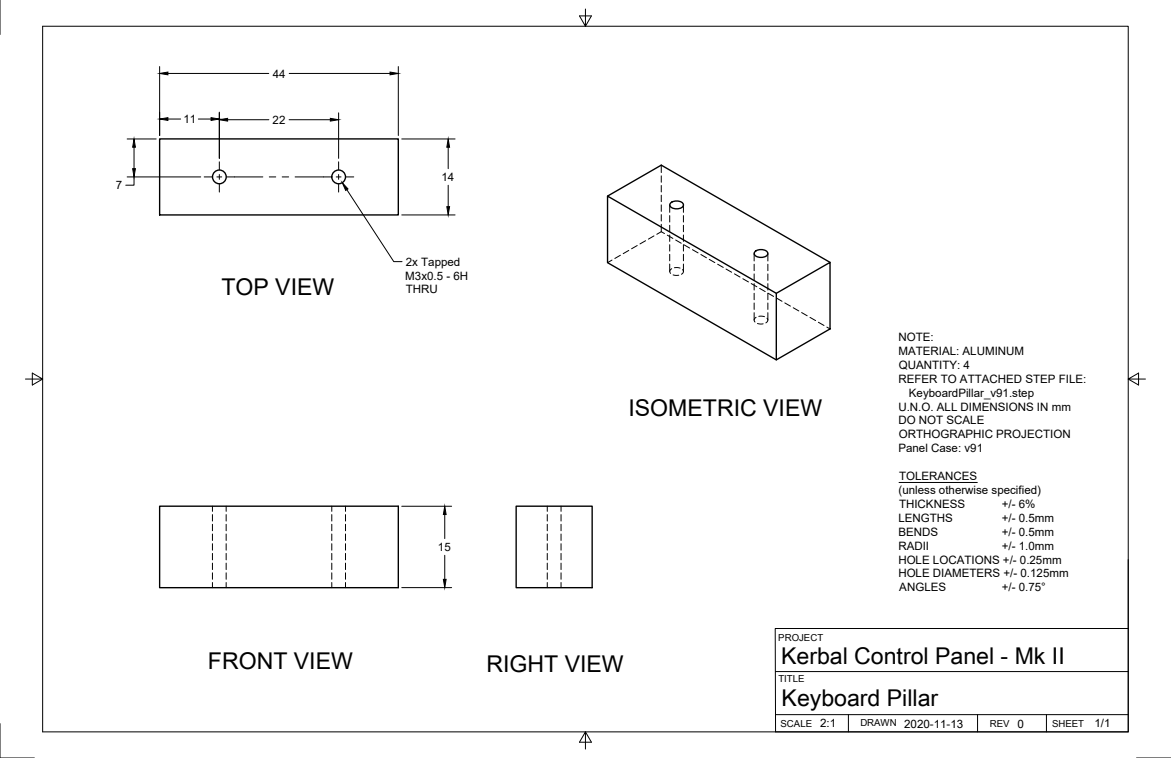
[picture p143: page 1]
SCALE 2:1; DRAWN 2020-11-13; REV 0; SHEET 1/1; Keyboard Pillar; THICKNESS; LENGTHS; BENDS; RADII; ANGLES; TOP VIEW; FRONT VIEW; RIGHT VIEW; ISOMETRIC VIEW; 2x Tapped M3x0.5 - 6H

NOTE:
MATERIAL: ALUMINUM
QUANTITY: 4
REFER TO ATTACHED STEP FILE:
KeyboardPillar_v91.step
U.N.O. ALL DIMENSIONS IN mm
DO NOT SCALE
ORTHOGRAPHIC PROJECTION
Panel Case: v91

TOLERANCES
(unless otherwise specified)
HOLE LOCATIONS +/- 0.25mm
HOLE DIAMETERS +/- 0.125mm

PROJECT
Kerbal Control Panel - Mk II
