mountaineerman/KCP2/KCP2-physical/CAD/ForManufacture/Aluminum/Long Column/LongColumn_Rev0_v5.pdf

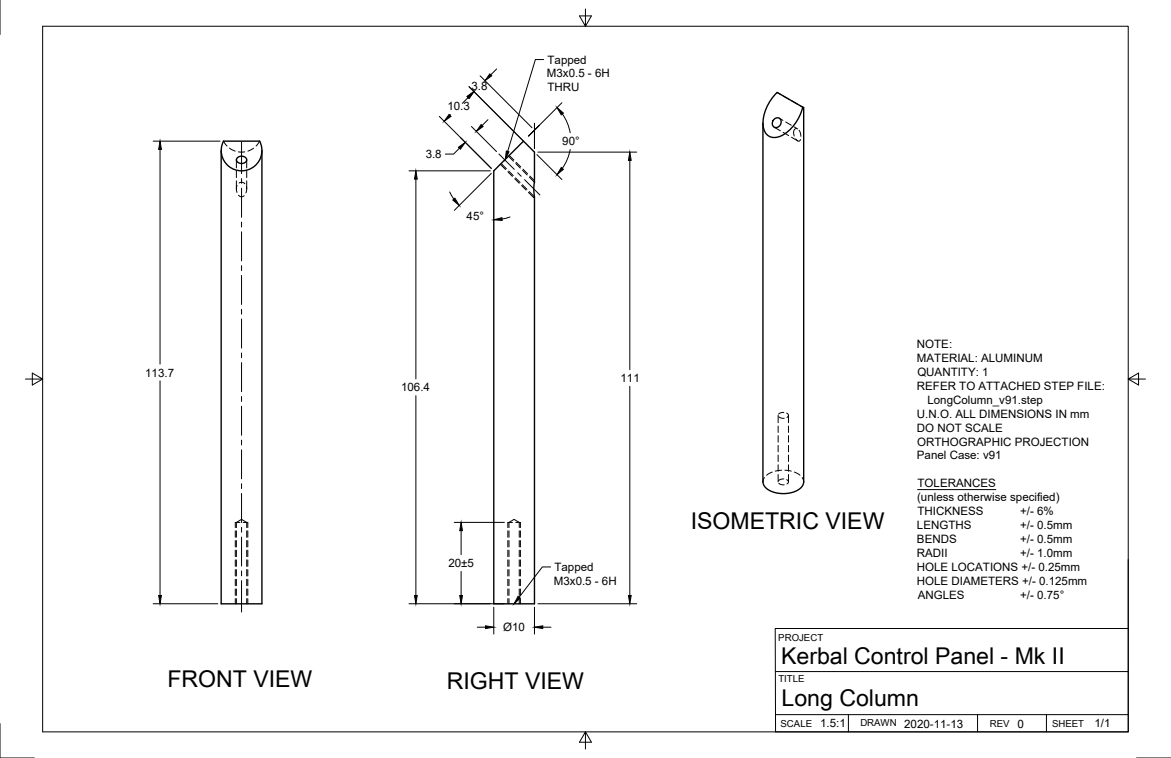
[picture p144: page 1]
SCALE 1.5:1; DRAWN 2020-11-13; REV 0; SHEET 1/1; Long Column; FRONT VIEW; RIGHT VIEW; ISOMETRIC VIEW; THICKNESS; LENGTHS; BENDS; RADII; ANGLES

NOTE:
MATERIAL: ALUMINUM
QUANTITY: 1
REFER TO ATTACHED STEP FILE:
LongColumn_v91.step
U.N.O. ALL DIMENSIONS IN mm
DO NOT SCALE
ORTHOGRAPHIC PROJECTION
Panel Case: v91

TOLERANCES
(unless otherwise specified)
HOLE LOCATIONS +/- 0.25mm
HOLE DIAMETERS +/- 0.125mm

PROJECT
Kerbal Control Panel - Mk II
