mountaineerman/KCP2/KCP2-physical/CAD/ForManufacture/Aluminum/Panel Bottom Plate/Panel_BottomPlate_Rev0_v21.pdf

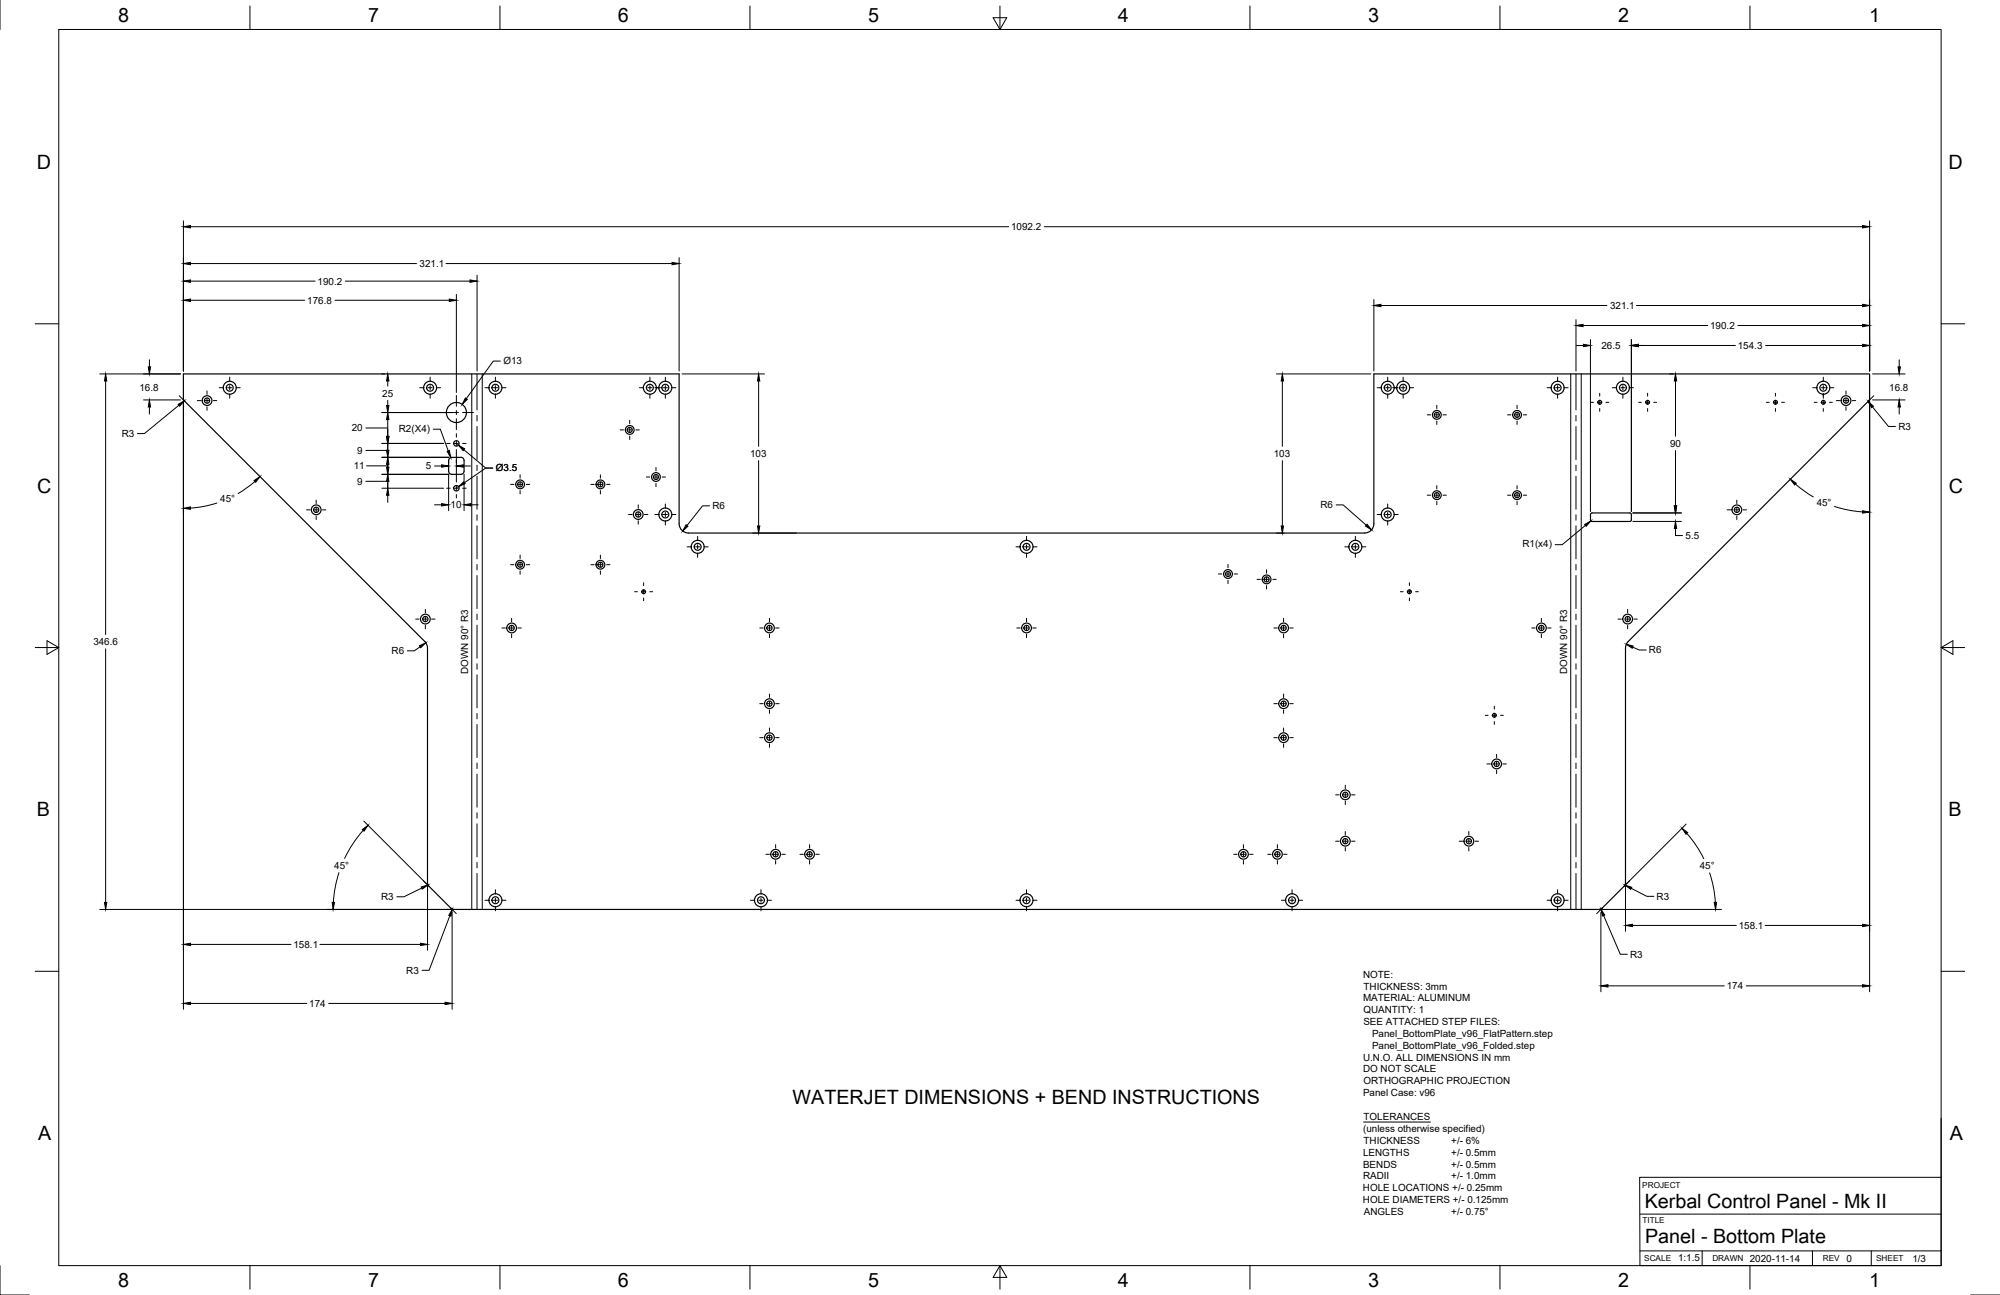
[picture p145: page 1]
SCALE 1:1.5; DRAWN 2020-11-14; REV 0; SHEET 1/3; THICKNESS; LENGTHS; BENDS; RADII; ANGLES; +/- 0.75° DOWN 90° R3; DOWN 90° R3

NOTE:
THICKNESS: 3mm
MATERIAL: ALUMINUM
QUANTITY: 1
SEE ATTACHED STEP FILES:
Panel_BottomPlate_v96_FlatPattern.step
Panel_BottomPlate_v96_Folded.step
U.N.O. ALL DIMENSIONS IN mm
DO NOT SCALE
ORTHOGRAPHIC PROJECTION
Panel Case: v96

WATERJET DIMENSIONS + BEND INSTRUCTIONS

TOLERANCES
(unless otherwise specified)
HOLE LOCATIONS +/- 0.25mm
HOLE DIAMETERS +/- 0.125mm

PROJECT
Kerbal Control Panel - Mk II

TITLE
Panel - Bottom Plate

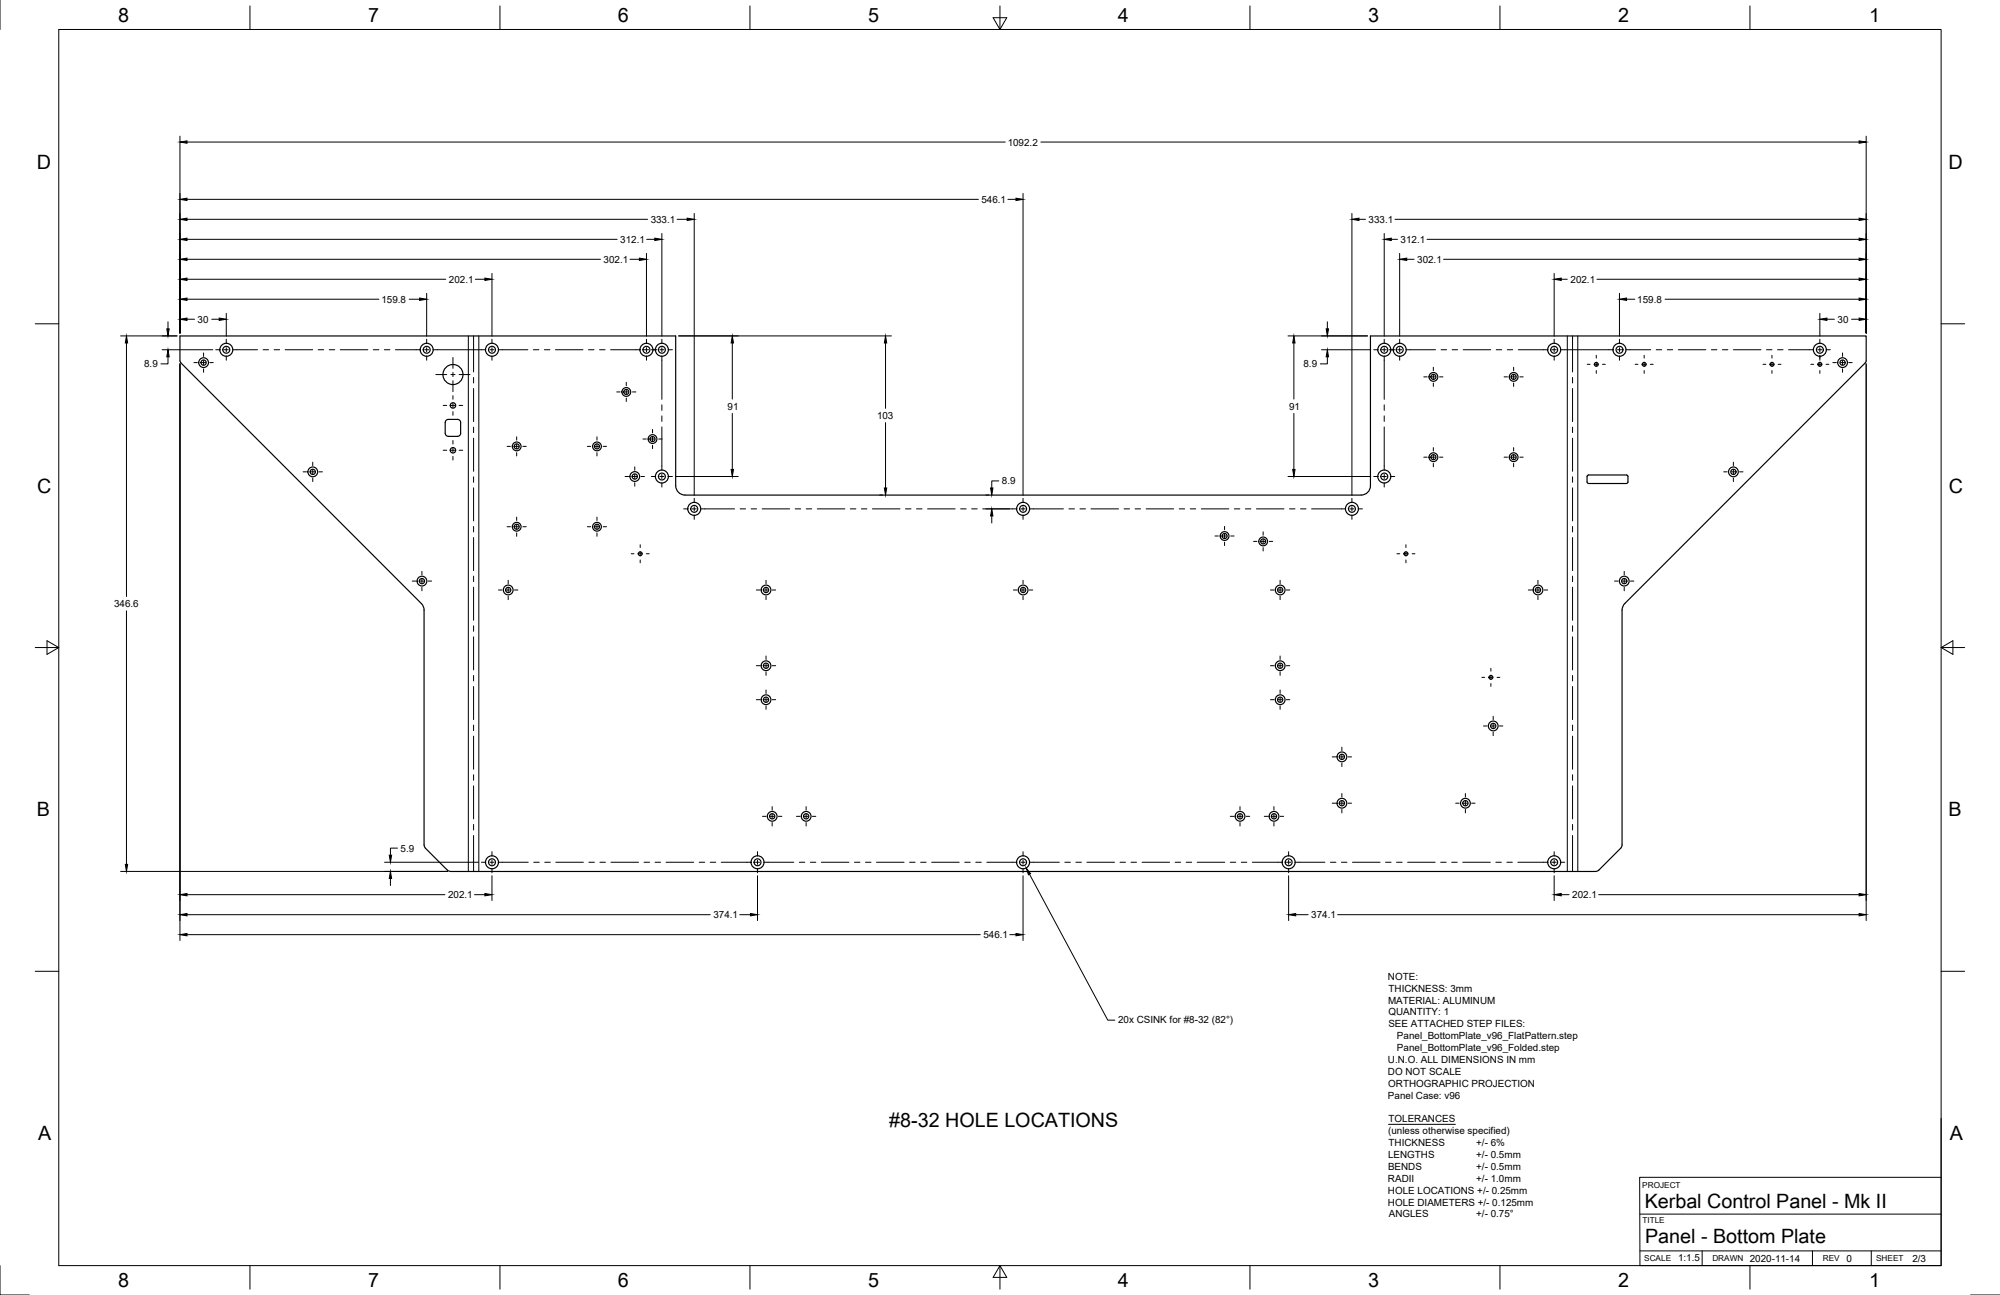
[picture p146: page 2]
SCALE 1:1.5; DRAWN 2020-11-14; REV 0; SHEET 2/3; #8-32 HOLE LOCATIONS; 20x CSINK for #8-32 (82°); THICKNESS; LENGTHS; BENDS; RADII; ANGLES

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

TOLERANCES
(unless otherwise specified)

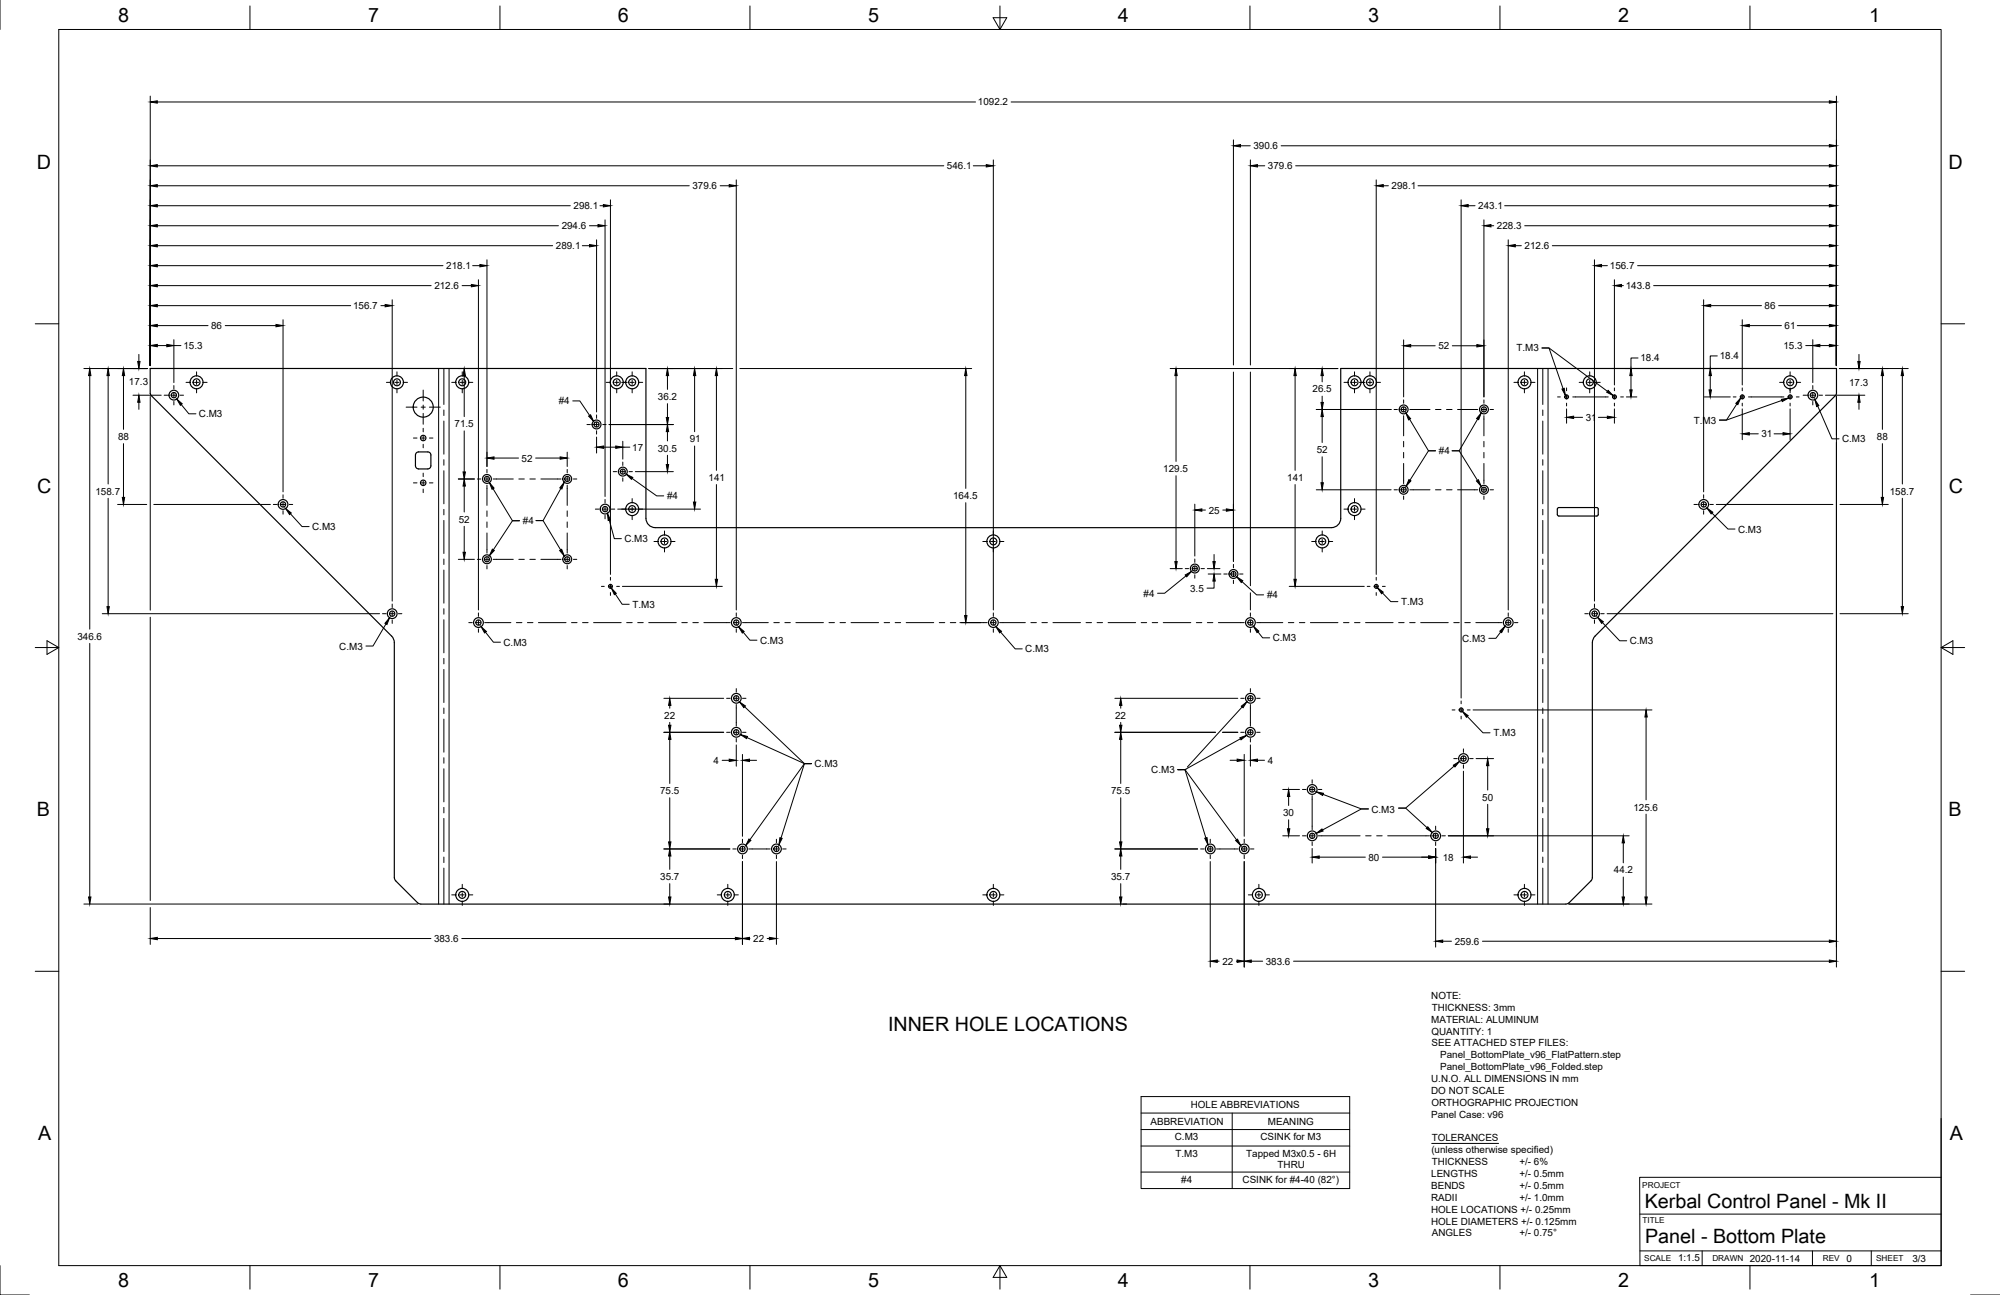
[picture p147: page 3]
SCALE 1:1.5; DRAWN 2020-11-14; REV 0; SHEET 3/3; THICKNESS; LENGTHS; BENDS; RADII; ANGLES; HOLE ABBREVIATIONS

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

INNER HOLE LOCATIONS

ABBREVIATION | MEANING
C.M3 | CSINK for M3
T.M3 | Tapped M3x0.5 - 6H THRU

TOLERANCES
(unless otherwise specified)

#4 | CSINK for #4-40 (82°)
