mountaineerman/KCP2/KCP2-physical/CAD/ForManufacture/Aluminum/Panel Dodge Plate/Panel_DodgePlate_Rev0_v16.pdf

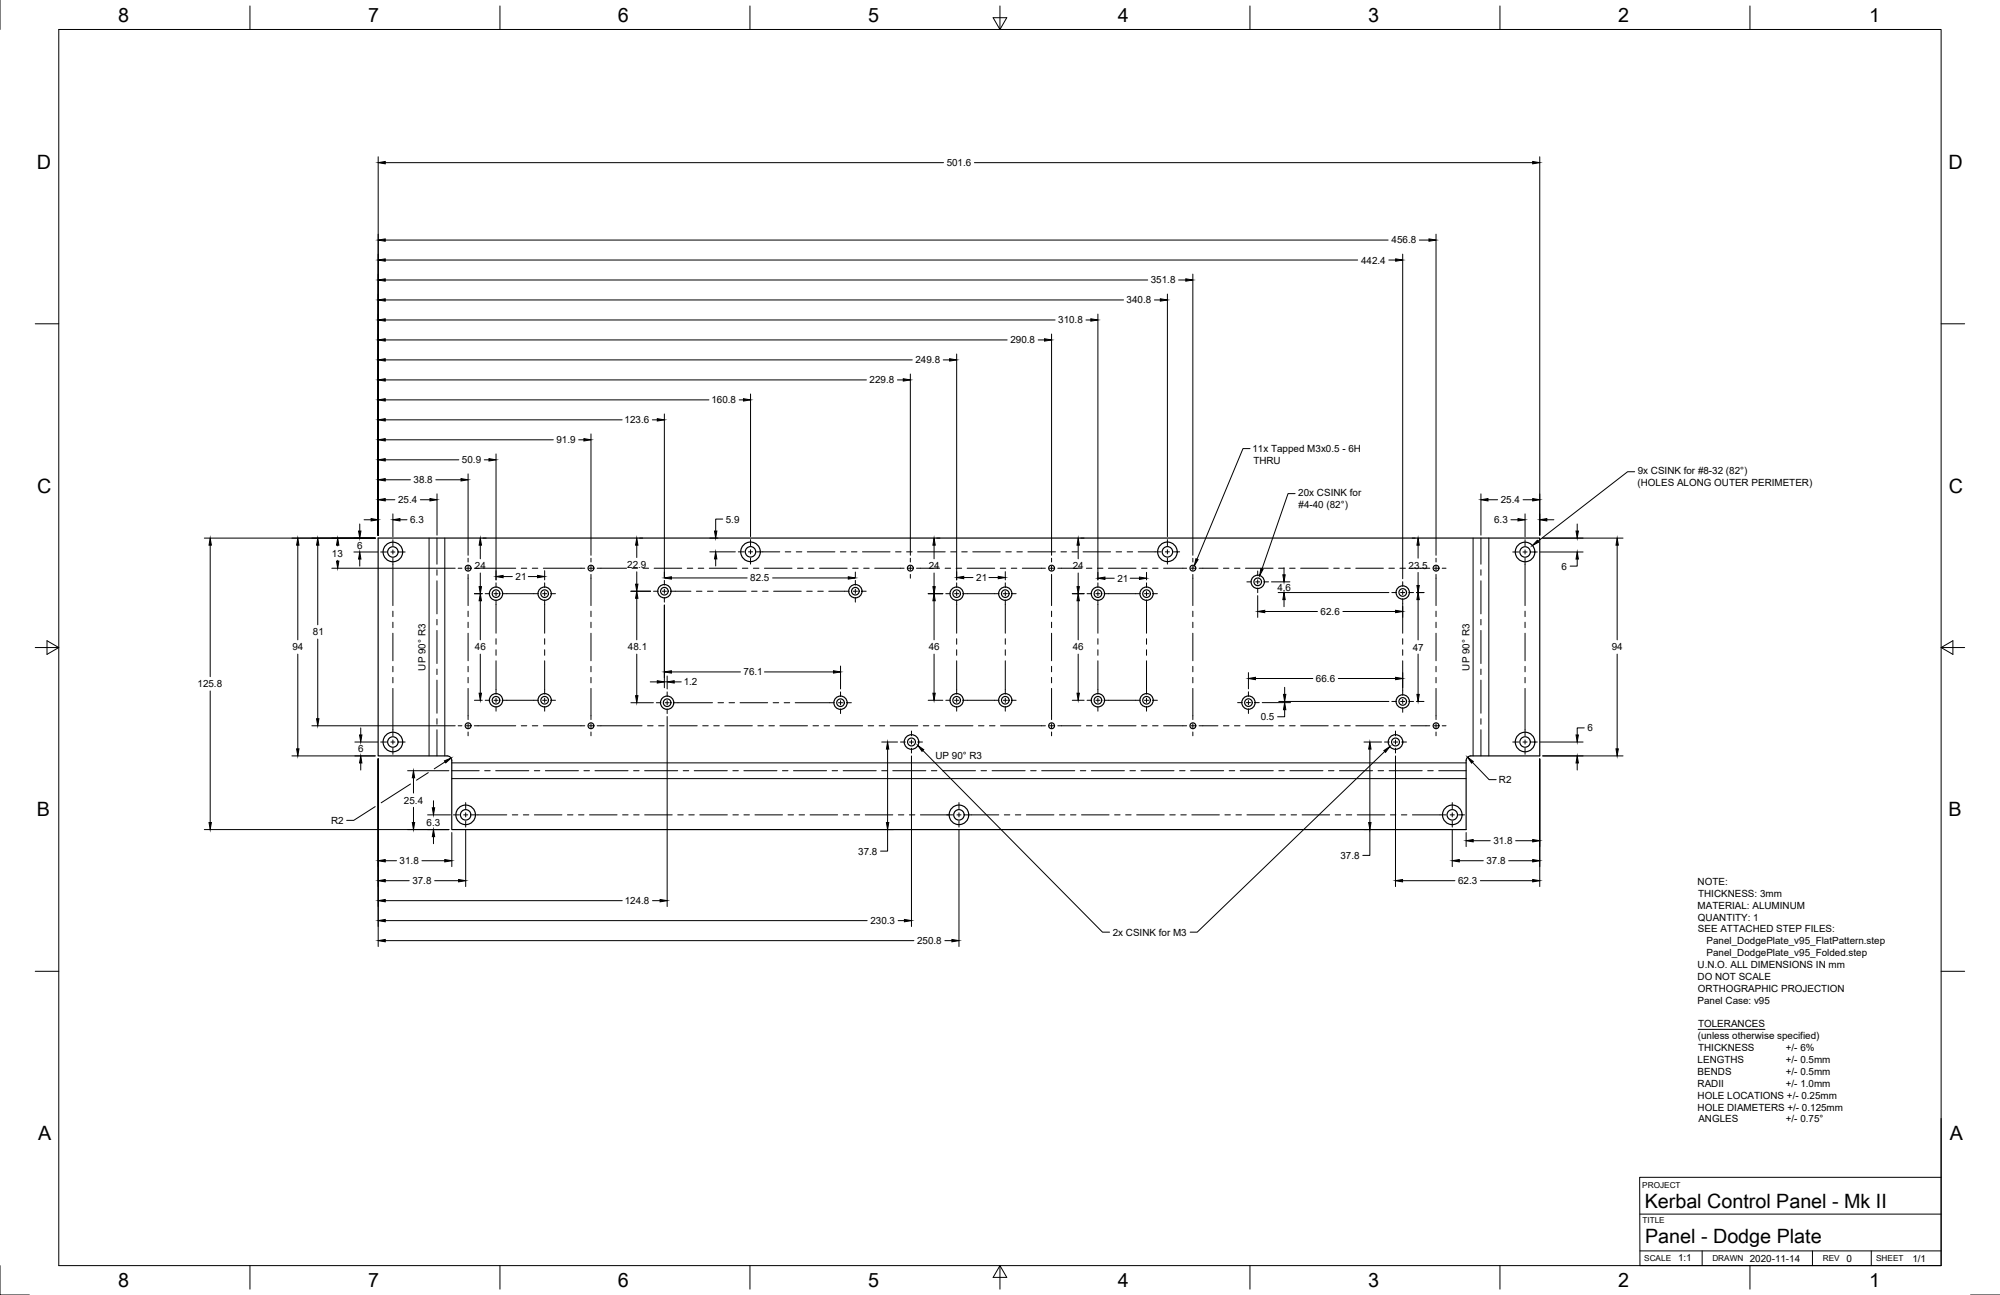
[picture p148: page 1]
SCALE 1:1; DRAWN 2020-11-14; REV 0; SHEET 1/1; THICKNESS; LENGTHS; BENDS; RADII; ANGLES; 2x CSINK for M3; 11x Tapped M3x0.5 - 6H; 20x CSINK for #4-40 (82°)

9x CSINK for #8-32 (82°)
(HOLES ALONG OUTER PERIMETER)

NOTE:
THICKNESS: 3mm
MATERIAL: ALUMINUM
QUANTITY: 1
SEE ATTACHED STEP FILES:
Panel_DodgePlate_v95_FlatPattern.step
Panel_DodgePlate_v95_Folded.step
U.N.O. ALL DIMENSIONS IN mm
DO NOT SCALE
ORTHOGRAPHIC PROJECTION
Panel Case: v95

TOLERANCES
(unless otherwise specified)
HOLE LOCATIONS +/- 0.25mm
HOLE DIAMETERS +/- 0.125mm

PROJECT
Kerbal Control Panel - Mk II

TITLE
Panel - Dodge Plate
