mountaineerman/KCP2/KCP2-physical/CAD/ForManufacture/Aluminum/Panel Mounting Plate/Panel_MountingPlate_Rev0_v11.pdf

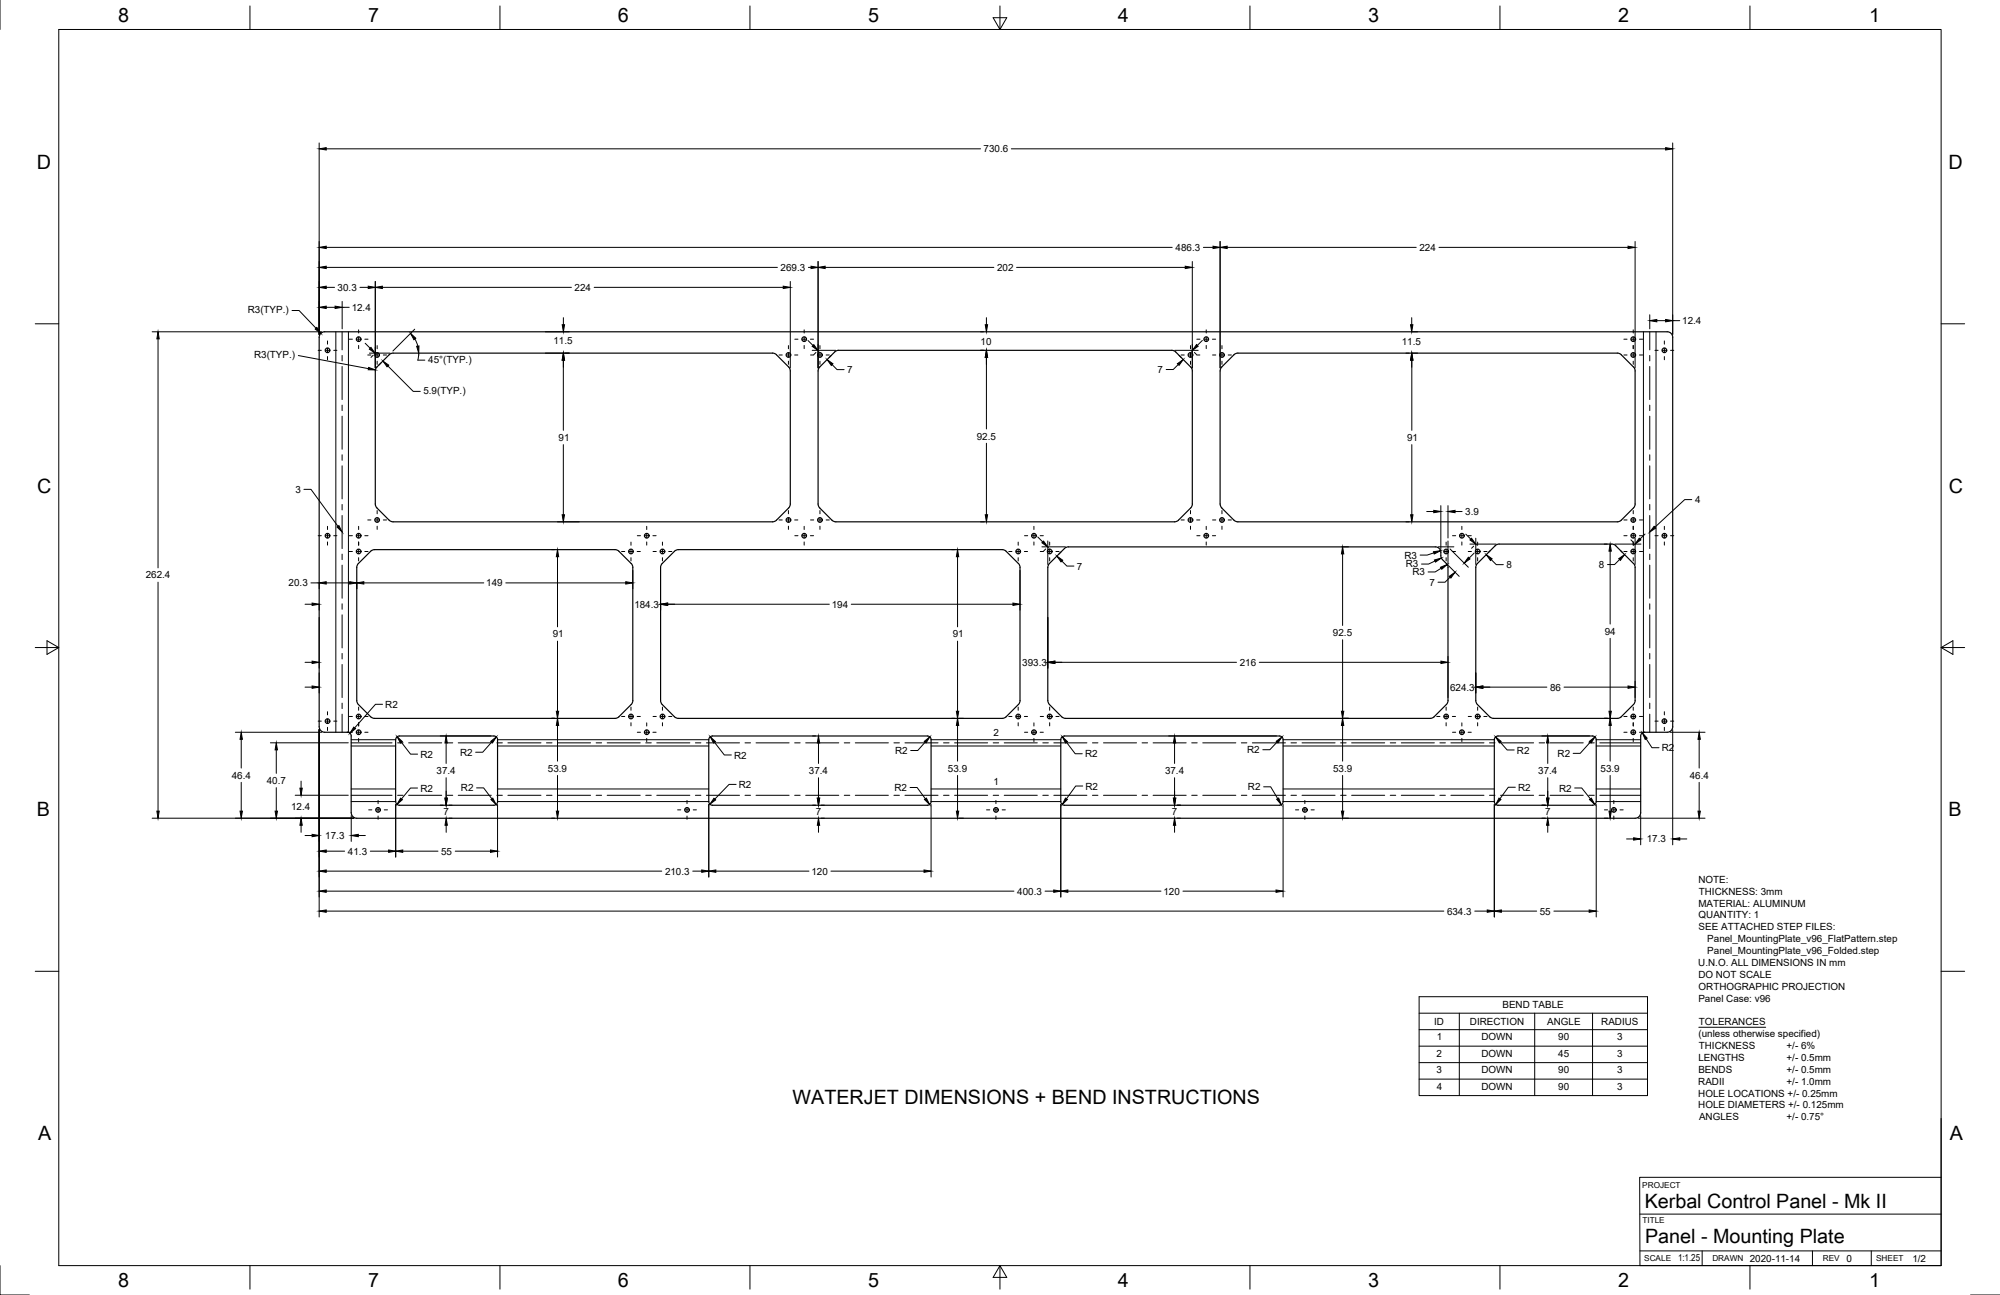
[picture p149: page 1]
SCALE 1:1.25; DRAWN 2020-11-14; REV 0; SHEET 1/2; THICKNESS; LENGTHS; BENDS; RADII; ANGLES; 45°(TYP.) R3(TYP.); BEND TABLE

NOTE:
THICKNESS: 3mm
MATERIAL: ALUMINUM
QUANTITY: 1
SEE ATTACHED STEP FILES:
Panel_MountingPlate_v96_FlatPattern.step
Panel_MountingPlate_v96_Folded.step
U.N.O. ALL DIMENSIONS IN mm
DO NOT SCALE
ORTHOGRAPHIC PROJECTION
Panel Case: v96

ID | DIRECTION | ANGLE | RADIUS
1 | DOWN | 90 | 3
2 | DOWN | 45 | 3
3 | DOWN | 90 | 3
4 | DOWN | 90 | 3

TOLERANCES
(unless otherwise specified)
HOLE LOCATIONS +/- 0.25mm
HOLE DIAMETERS +/- 0.125mm

WATERJET DIMENSIONS + BEND INSTRUCTIONS

PROJECT
Kerbal Control Panel - Mk II

TITLE
Panel - Mounting Plate

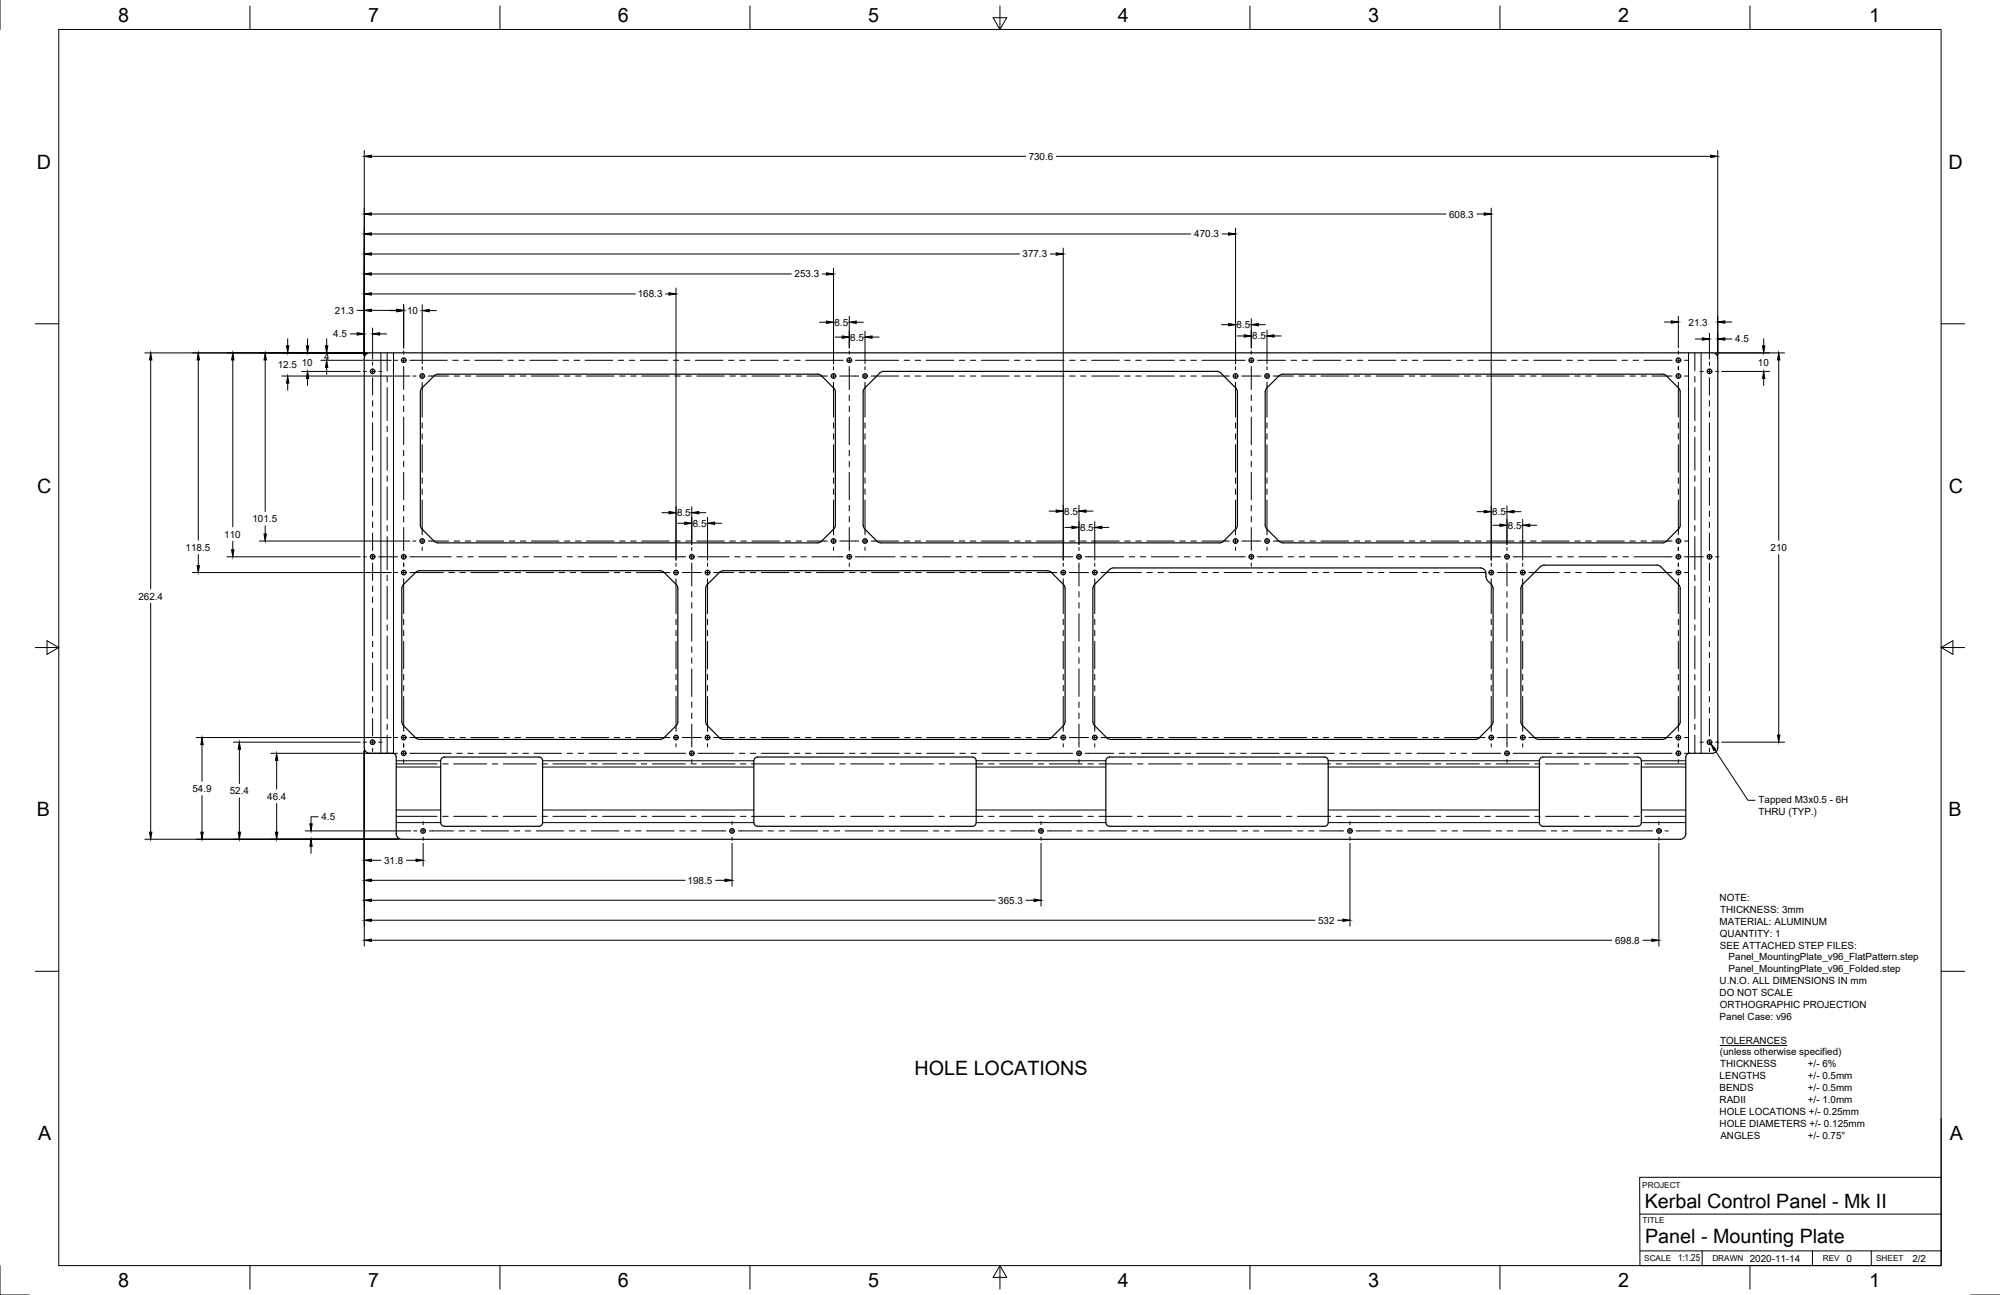
[picture p150: page 2]
SCALE 1:1.25; DRAWN 2020-11-14; REV 0; SHEET 2/2; THICKNESS; LENGTHS; BENDS; RADII; ANGLES; HOLE LOCATIONS; Tapped M3x0.5 - 6H THRU (TYP.)

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

TOLERANCES
(unless otherwise specified)
HOLE LOCATIONS +/- 0.25mm
HOLE DIAMETERS +/- 0.125mm

PROJECT
Kerbal Control Panel - Mk II

TITLE
Panel - Mounting Plate
