mountaineerman/KCP2/KCP2-physical/CAD/ForManufacture/Aluminum/Panel Top Plate/Panel_TopPlate_Rev1.pdf

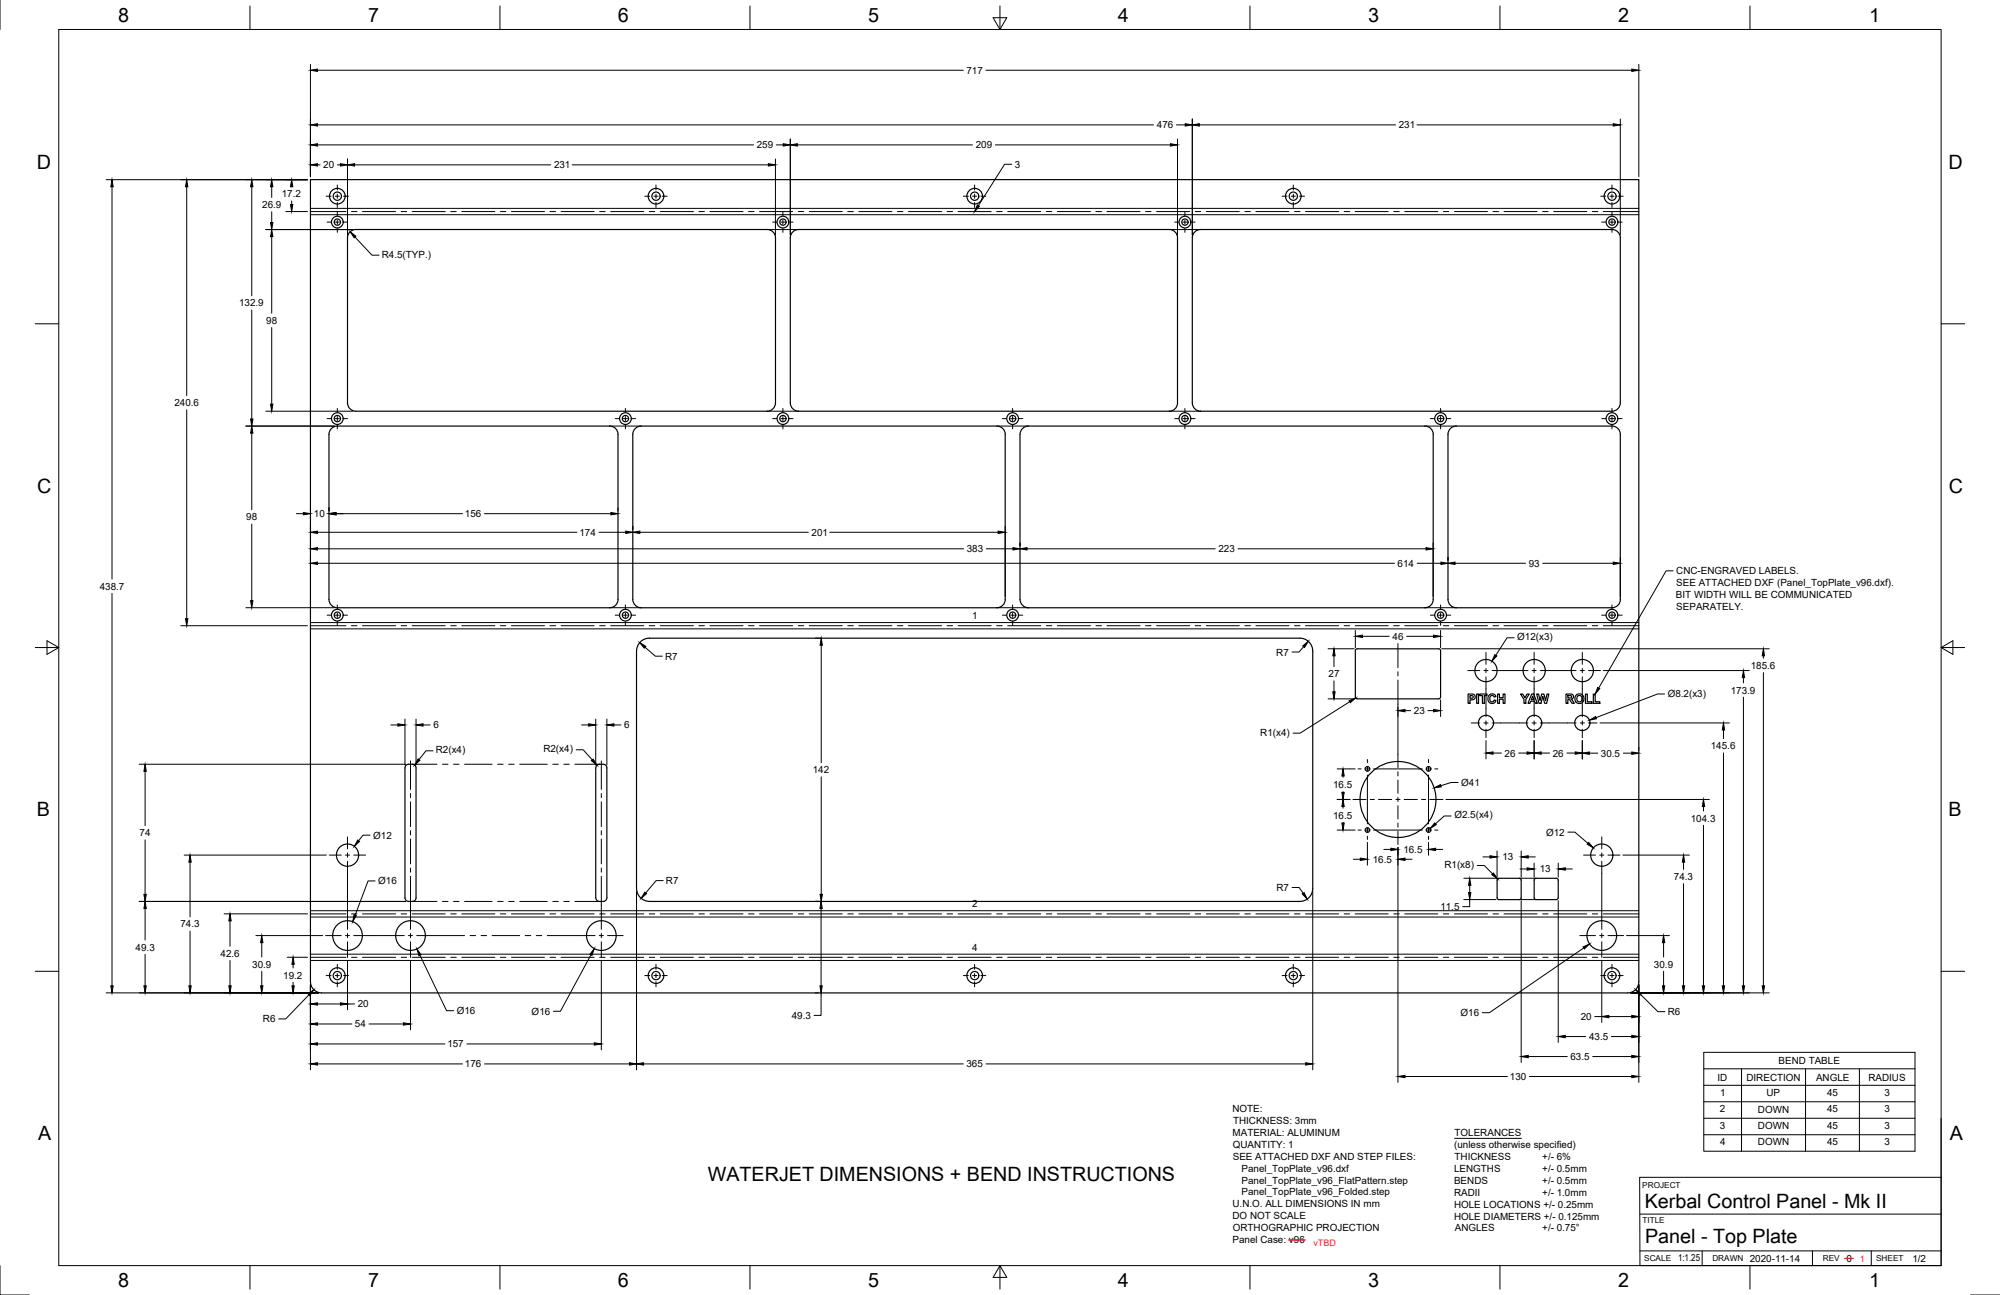
[picture p153: page 1]
SCALE 1:1.25; DRAWN 2020-11-14; REV 0; SHEET 1/2; THICKNESS; LENGTHS; BENDS; RADII; ANGLES; BEND TABLE

CNC-ENGRAVED LABELS.
SEE ATTACHED DXF (Panel_TopPlate_v96.dxf).
BIT WIDTH WILL BE COMMUNICATED
SEPARATELY.

ID | DIRECTION | ANGLE | RADIUS
1 | UP | 45 | 3
2 | DOWN | 45 | 3
3 | DOWN | 45 | 3
4 | DOWN | 45 | 3

NOTE:
THICKNESS: 3mm
MATERIAL: ALUMINUM
QUANTITY: 1
SEE ATTACHED DXF AND STEP FILES:
Panel_TopPlate_v96.dxf
Panel_TopPlate_v96_FlatPattern.step
Panel_TopPlate_v96_Folded.step
U.N.O. ALL DIMENSIONS IN mm
DO NOT SCALE
ORTHOGRAPHIC PROJECTION
Panel Case: v96

TOLERANCES
(unless otherwise specified)
HOLE LOCATIONS +/- 0.25mm
HOLE DIAMETERS +/- 0.125mm

WATERJET DIMENSIONS + BEND INSTRUCTIONS

PROJECT
Kerbal Control Panel - Mk II

TITLE
Panel - Top Plate

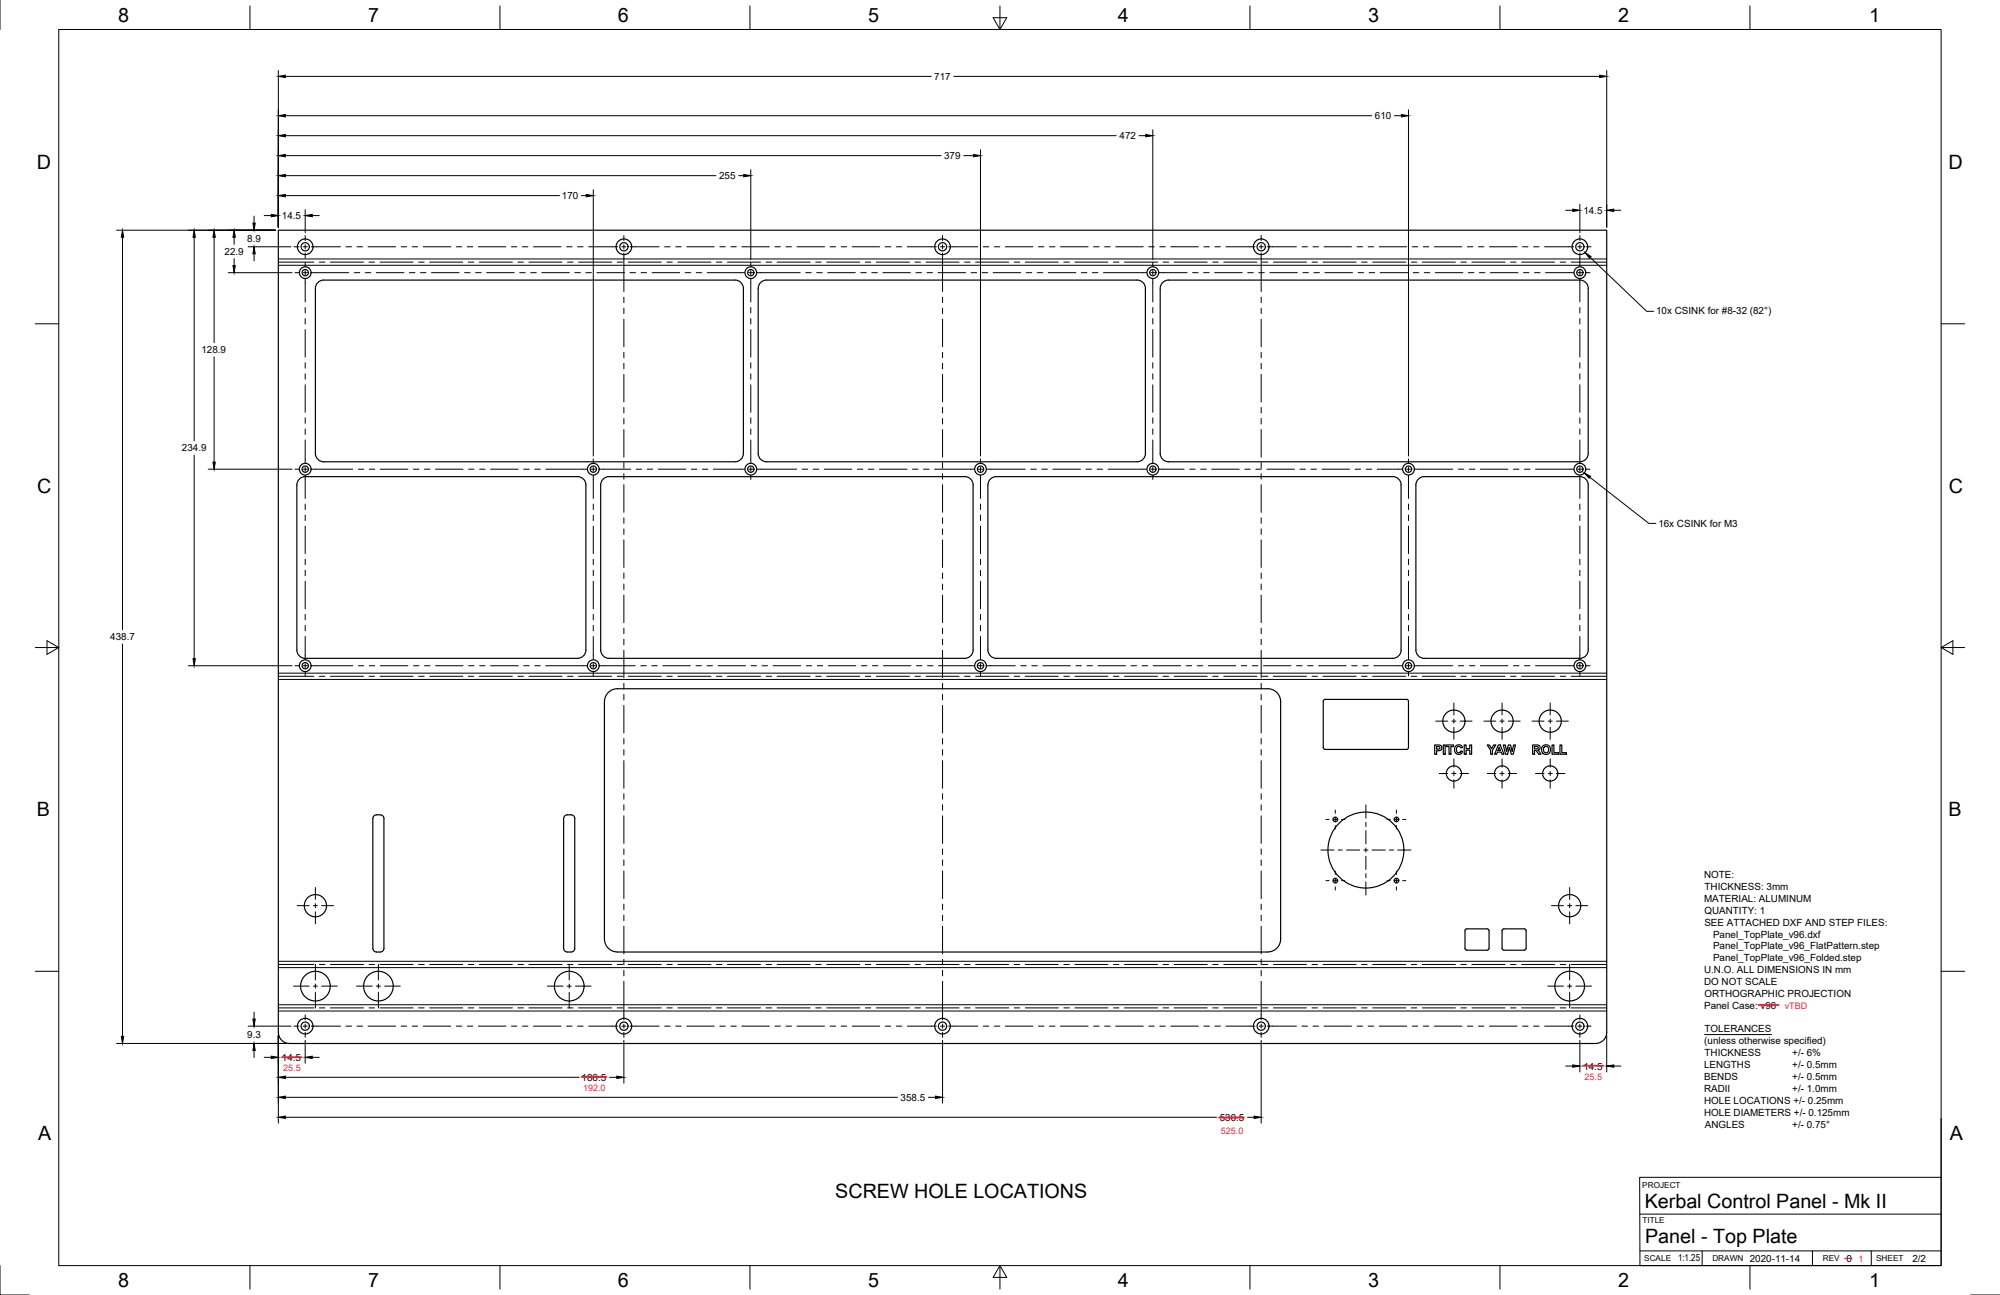
[picture p154: page 2]
SCALE 1:1.25; DRAWN 2020-11-14; REV 0; SHEET 2/2; THICKNESS; LENGTHS; BENDS; RADII; ANGLES; 10x CSINK for #8-32 (82°); 16x CSINK for M3

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

TOLERANCES
(unless otherwise specified)
HOLE LOCATIONS +/- 0.25mm
HOLE DIAMETERS +/- 0.125mm

SCREW HOLE LOCATIONS

PROJECT
Kerbal Control Panel - Mk II

TITLE
Panel - Top Plate
