mountaineerman/KCP2/KCP2-physical/CAD/ForManufacture/Aluminum/Short Column/ShortColumn_Rev0_v5.pdf

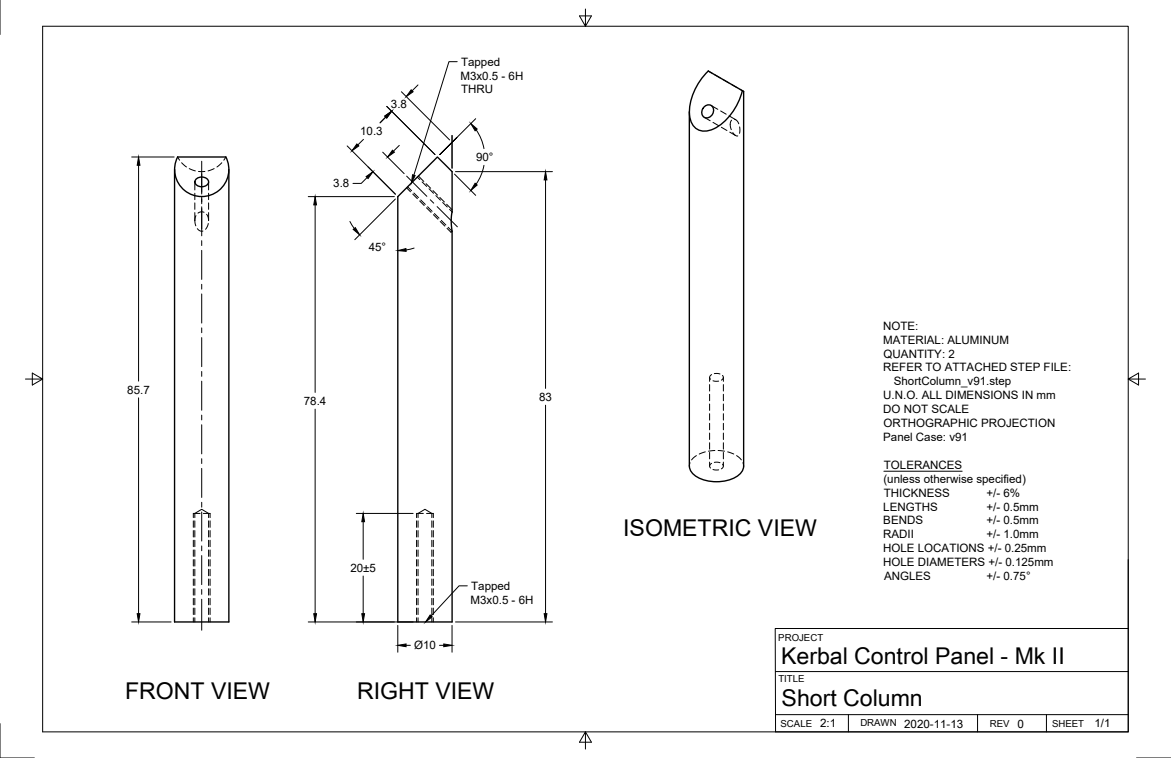
[picture p155: page 1]
SCALE 2:1; DRAWN 2020-11-13; REV 0; SHEET 1/1; Short Column FRONT VIEW; RIGHT VIEW; ISOMETRIC VIEW; THICKNESS; LENGTHS; BENDS; RADII; ANGLES

NOTE:
MATERIAL: ALUMINUM
QUANTITY: 2
REFER TO ATTACHED STEP FILE:
ShortColumn_v91.step
U.N.O. ALL DIMENSIONS IN mm
DO NOT SCALE
ORTHOGRAPHIC PROJECTION
Panel Case: v91

TOLERANCES
(unless otherwise specified)
HOLE LOCATIONS +/- 0.25mm
HOLE DIAMETERS +/- 0.125mm

PROJECT
Kerbal Control Panel - Mk II
