mountaineerman/KCP2/KCP2-physical/CAD/ForManufacture/Aluminum/Throttle Bracket/ThrottleBracket_Rev0_v9.pdf

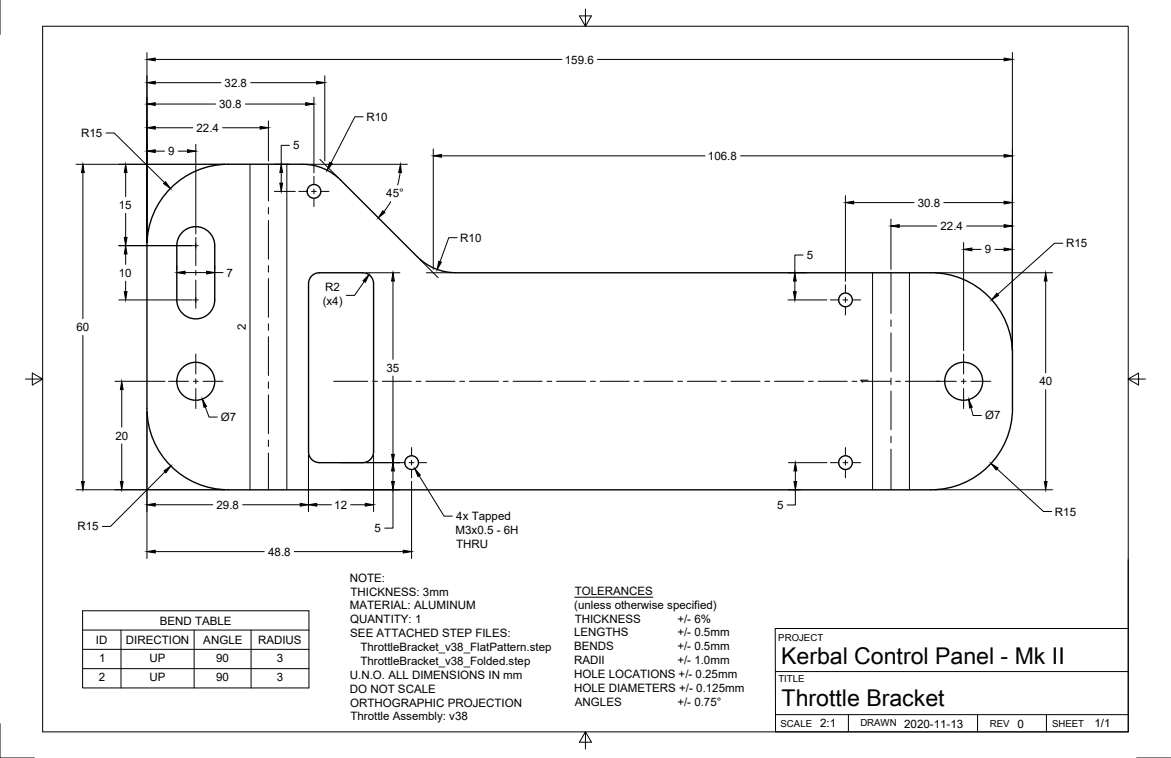
[picture p156: page 1]
SCALE 2:1; DRAWN 2020-11-13; REV 0; SHEET 1/1; Throttle Bracket; THICKNESS; LENGTHS; BENDS; RADII; ANGLES; 4x Tapped M3x0.5 - 6H; BEND TABLE

NOTE:
THICKNESS: 3mm
MATERIAL: ALUMINUM
QUANTITY: 1
SEE ATTACHED STEP FILES:
ThrottleBracket_v38_FlatPattern.step
ThrottleBracket_v38_Folded.step
U.N.O. ALL DIMENSIONS IN mm
DO NOT SCALE
ORTHOGRAPHIC PROJECTION
Throttle Assembly: v38

TOLERANCES
(unless otherwise specified)
HOLE LOCATIONS +/- 0.25mm
HOLE DIAMETERS +/- 0.125mm

PROJECT
Kerbal Control Panel - Mk II

1 | UP | 90 | 3
2 | UP | 90 | 3
