mountaineerman/KCP2/KCP2-physical/CAD/ForManufacture/Aluminum/Throttle Handlebar/ThrottleHandlebar_Rev0_v5.pdf

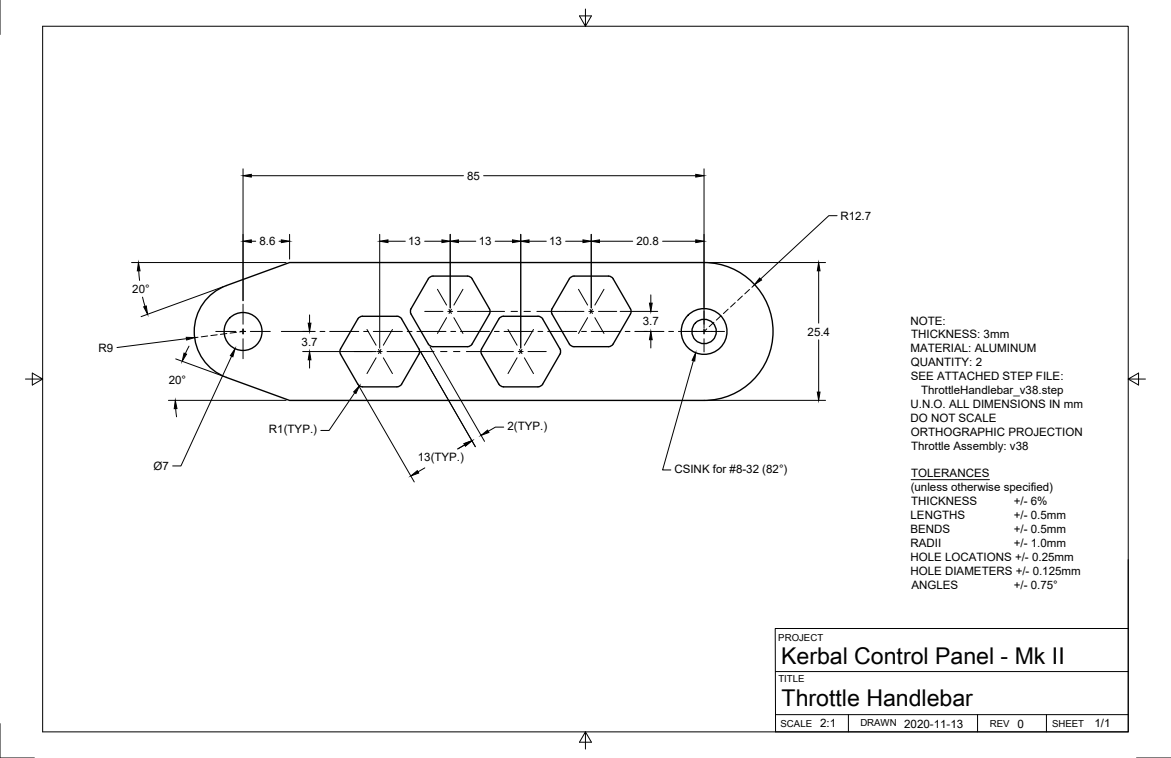
[picture p157: page 1]
SCALE 2:1; DRAWN 2020-11-13; REV 0; SHEET 1/1; Throttle Handlebar; THICKNESS; LENGTHS; BENDS; RADII; ANGLES; CSINK for #8-32 (82°)

NOTE:
THICKNESS: 3mm
MATERIAL: ALUMINUM
QUANTITY: 2
SEE ATTACHED STEP FILE:
ThrottleHandlebar_v38.step
U.N.O. ALL DIMENSIONS IN mm
DO NOT SCALE
ORTHOGRAPHIC PROJECTION
Throttle Assembly: v38

TOLERANCES
(unless otherwise specified)
HOLE LOCATIONS +/- 0.25mm
HOLE DIAMETERS +/- 0.125mm

PROJECT
Kerbal Control Panel - Mk II
