mountaineerman/KCP2/KCP2-physical/CAD/ForManufacture/ClearAcrylic/Gauge Tower Acrylic Panel/GaugeTower_AcrylicPanel_Rev0_v6.pdf

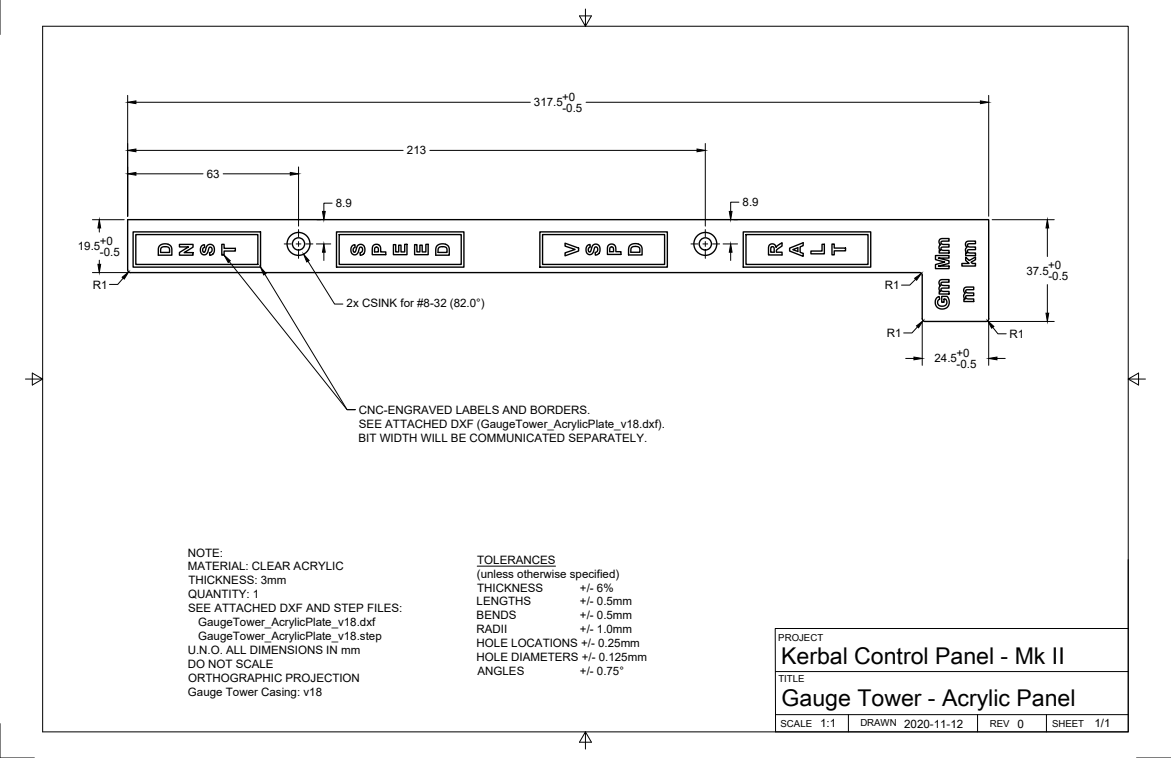
[picture p158: page 1]
SCALE 1:1; DRAWN 2020-11-12; REV 0; SHEET 1/1; THICKNESS; LENGTHS; BENDS; RADII; ANGLES; 2x CSINK for #8-32 (82.0°)

CNC-ENGRAVED LABELS AND BORDERS.
SEE ATTACHED DXF (GaugeTower_AcrylicPlate_v18.dxf).
BIT WIDTH WILL BE COMMUNICATED SEPARATELY.

NOTE:
MATERIAL: CLEAR ACRYLIC
THICKNESS: 3mm
QUANTITY: 1
SEE ATTACHED DXF AND STEP FILES:
GaugeTower_AcrylicPlate_v18.dxf
GaugeTower_AcrylicPlate_v18.step
U.N.O. ALL DIMENSIONS IN mm
DO NOT SCALE
ORTHOGRAPHIC PROJECTION
Gauge Tower Casing: v18

TOLERANCES
(unless otherwise specified)
HOLE LOCATIONS +/- 0.25mm
HOLE DIAMETERS +/- 0.125mm

PROJECT
Kerbal Control Panel - Mk II

TITLE
Gauge Tower - Acrylic Panel
