mountaineerman/KCP2/KCP2-physical/CAD/ForManufacture/ClearAcrylic/Module C/ModuleC_Rev0_v4.pdf

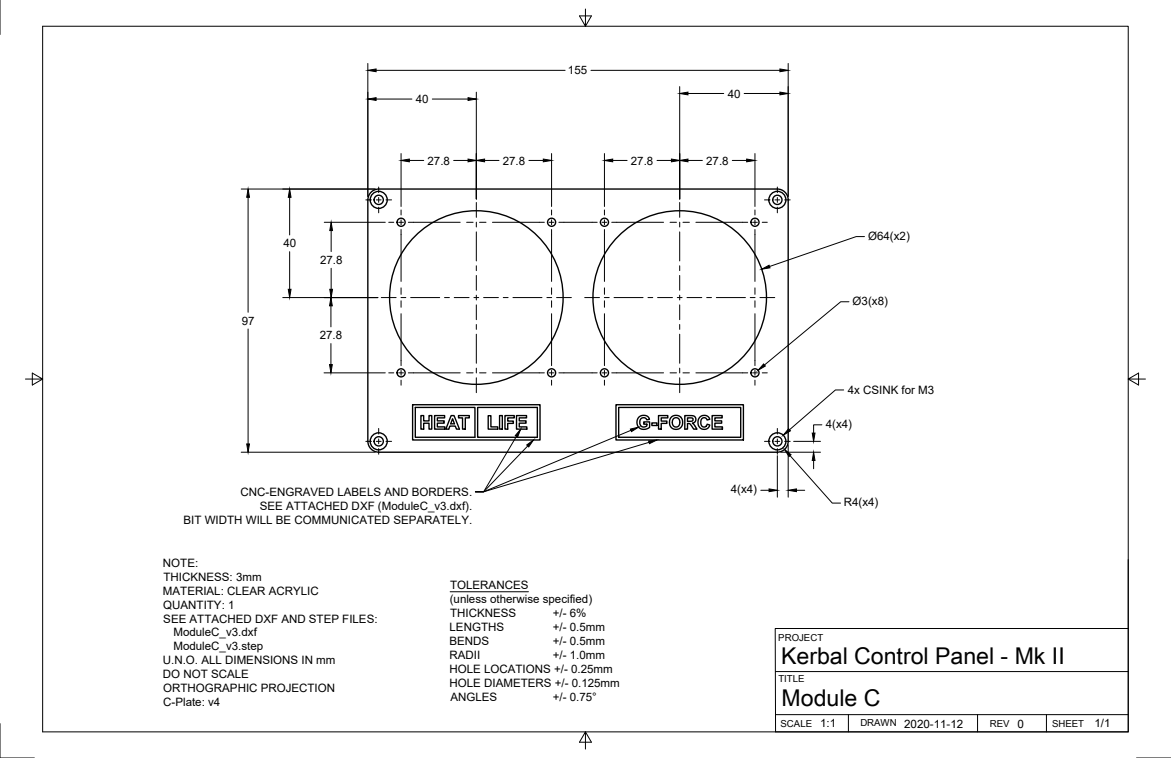
[picture p159: page 1]
SCALE 1:1; DRAWN 2020-11-12; REV 0; SHEET 1/1; Module C; 4x CSINK for M3; THICKNESS; LENGTHS; BENDS; RADII; ANGLES

CNC-ENGRAVED LABELS AND BORDERS.
SEE ATTACHED DXF (ModuleC_v3.dxf).

BIT WIDTH WILL BE COMMUNICATED SEPARATELY.

NOTE:
THICKNESS: 3mm
MATERIAL: CLEAR ACRYLIC
QUANTITY: 1
SEE ATTACHED DXF AND STEP FILES:
ModuleC_v3.dxf
ModuleC_v3.step
U.N.O. ALL DIMENSIONS IN mm
DO NOT SCALE
ORTHOGRAPHIC PROJECTION
C-Plate: v4

TOLERANCES
(unless otherwise specified)
HOLE LOCATIONS +/- 0.25mm
HOLE DIAMETERS +/- 0.125mm

PROJECT
Kerbal Control Panel - Mk II
