mountaineerman/KCP2/KCP2-physical/CAD/ForManufacture/ClearAcrylic/Module D/ModuleD_Rev0_v6.pdf

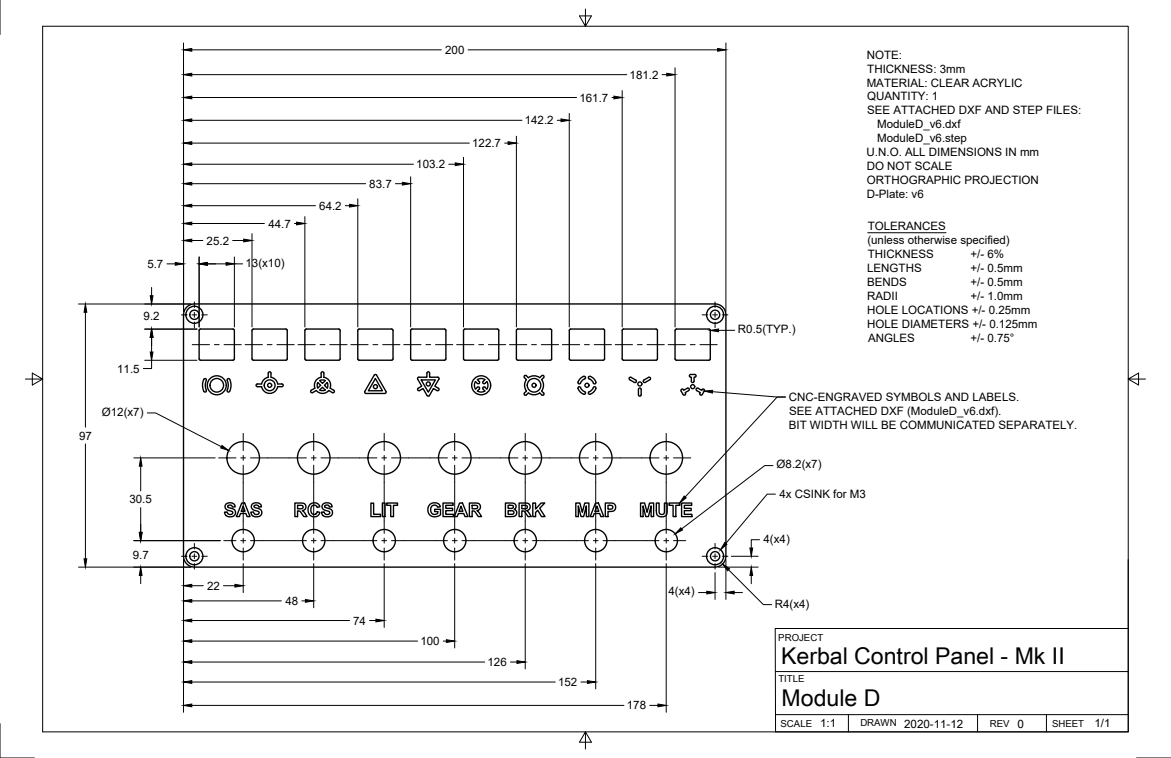
[picture p160: page 1]
SCALE 1:1; DRAWN 2020-11-12; REV 0; SHEET 1/1; Module D; THICKNESS; LENGTHS; BENDS; RADII; ANGLES; 4x CSINK for M3

NOTE:
THICKNESS: 3mm
MATERIAL: CLEAR ACRYLIC
QUANTITY: 1
SEE ATTACHED DXF AND STEP FILES:
ModuleD_v6.dxf
ModuleD_v6.step
U.N.O. ALL DIMENSIONS IN mm
DO NOT SCALE
ORTHOGRAPHIC PROJECTION
D-Plate: v6

TOLERANCES
(unless otherwise specified)
HOLE LOCATIONS +/- 0.25mm
HOLE DIAMETERS +/- 0.125mm

CNC-ENGRAVED SYMBOLS AND LABELS.
SEE ATTACHED DXF (ModuleD_v6.dxf).
BIT WIDTH WILL BE COMMUNICATED SEPARATELY.

PROJECT
Kerbal Control Panel - Mk II
