mountaineerman/KCP2/KCP2-physical/CAD/ForManufacture/ClearAcrylic/Module E/ModuleE_Rev0_v4.pdf

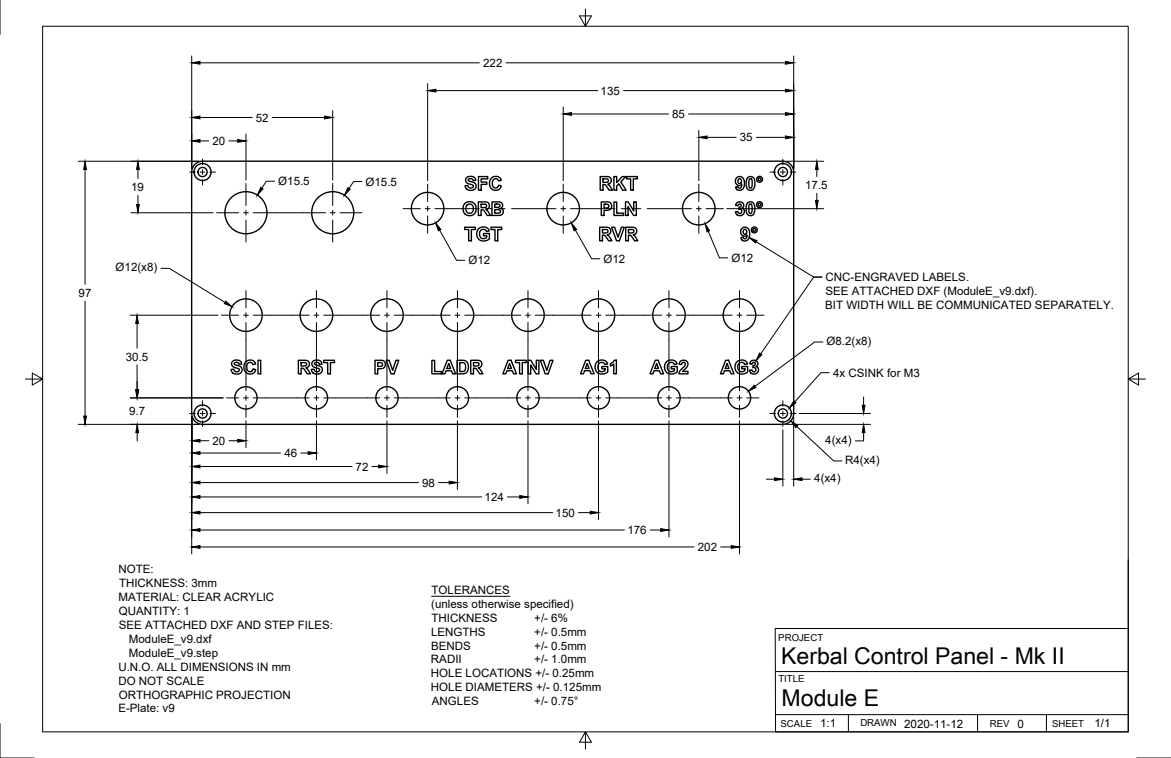
[picture p161: page 1]
SCALE 1:1; DRAWN 2020-11-12; REV 0; SHEET 1/1; Module E; 4x CSINK for M3; CNC-ENGRAVED LABELS.; THICKNESS; LENGTHS; BENDS; RADII; ANGLES

SEE ATTACHED DXF (ModuleE_v9.dxf).
BIT WIDTH WILL BE COMMUNICATED SEPARATELY.

NOTE:
THICKNESS: 3mm
MATERIAL: CLEAR ACRYLIC
QUANTITY: 1
SEE ATTACHED DXF AND STEP FILES:
ModuleE_v9.dxf
ModuleE_v9.step
U.N.O. ALL DIMENSIONS IN mm
DO NOT SCALE
ORTHOGRAPHIC PROJECTION
E-Plate: v9

TOLERANCES
(unless otherwise specified)
HOLE LOCATIONS +/- 0.25mm
HOLE DIAMETERS +/- 0.125mm

PROJECT
Kerbal Control Panel - Mk II
