mountaineerman/KCP2/KCP2-physical/CAD/ForManufacture/ClearAcrylic/Module F/ModuleF_Rev0_v6.pdf

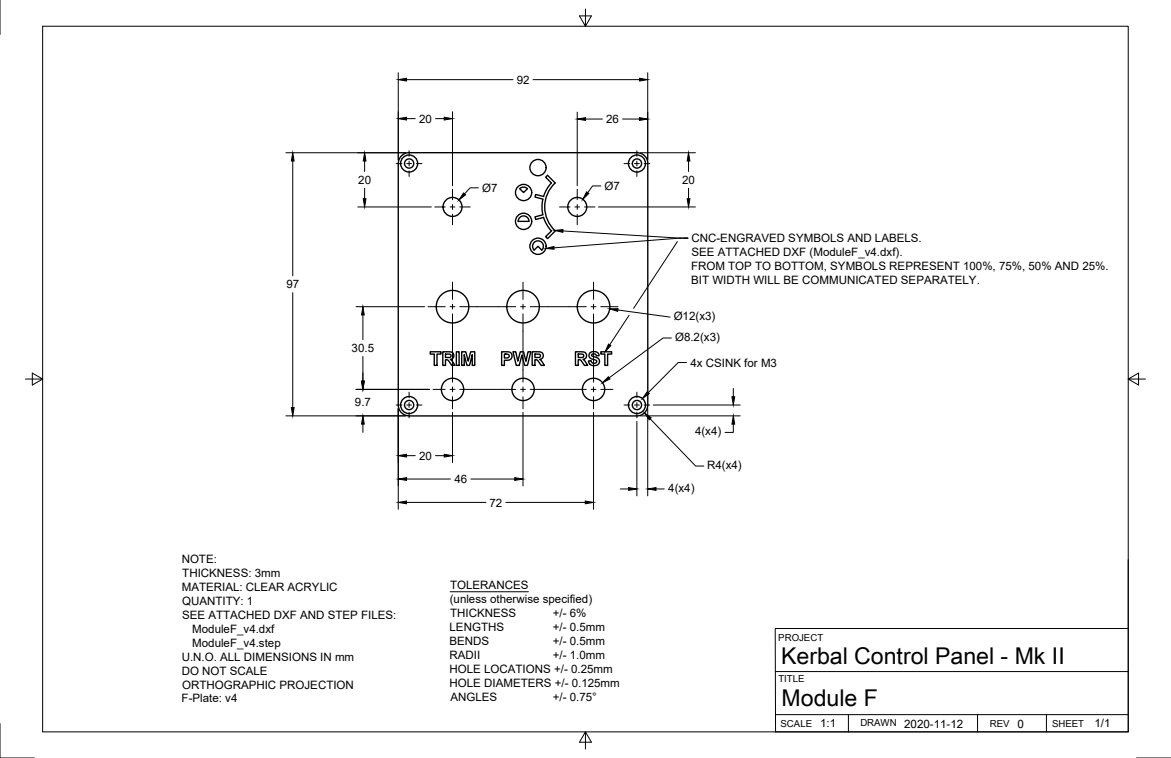
[picture p162: page 1]
SCALE 1:1; DRAWN 2020-11-12; REV 0; SHEET 1/1; Module F; 4x CSINK for M3; THICKNESS; LENGTHS; BENDS; RADII; ANGLES

CNC-ENGRAVED SYMBOLS AND LABELS.
SEE ATTACHED DXF (ModuleF_v4.dxf).
FROM TOP TO BOTTOM, SYMBOLS REPRESENT 100%, 75%, 50% AND 25%.
BIT WIDTH WILL BE COMMUNICATED SEPARATELY.

NOTE:
THICKNESS: 3mm
MATERIAL: CLEAR ACRYLIC
QUANTITY: 1
SEE ATTACHED DXF AND STEP FILES:
ModuleF_v4.dxf
ModuleF_v4.step
U.N.O. ALL DIMENSIONS IN mm
DO NOT SCALE
ORTHOGRAPHIC PROJECTION
F-Plate: v4

TOLERANCES
(unless otherwise specified)
HOLE LOCATIONS +/- 0.25mm
HOLE DIAMETERS +/- 0.125mm

PROJECT
Kerbal Control Panel - Mk II
