mountaineerman/KCP2/KCP2-physical/CAD/ForManufacture/ClearAcrylic/Module G/ModuleG_Rev0_v7.pdf

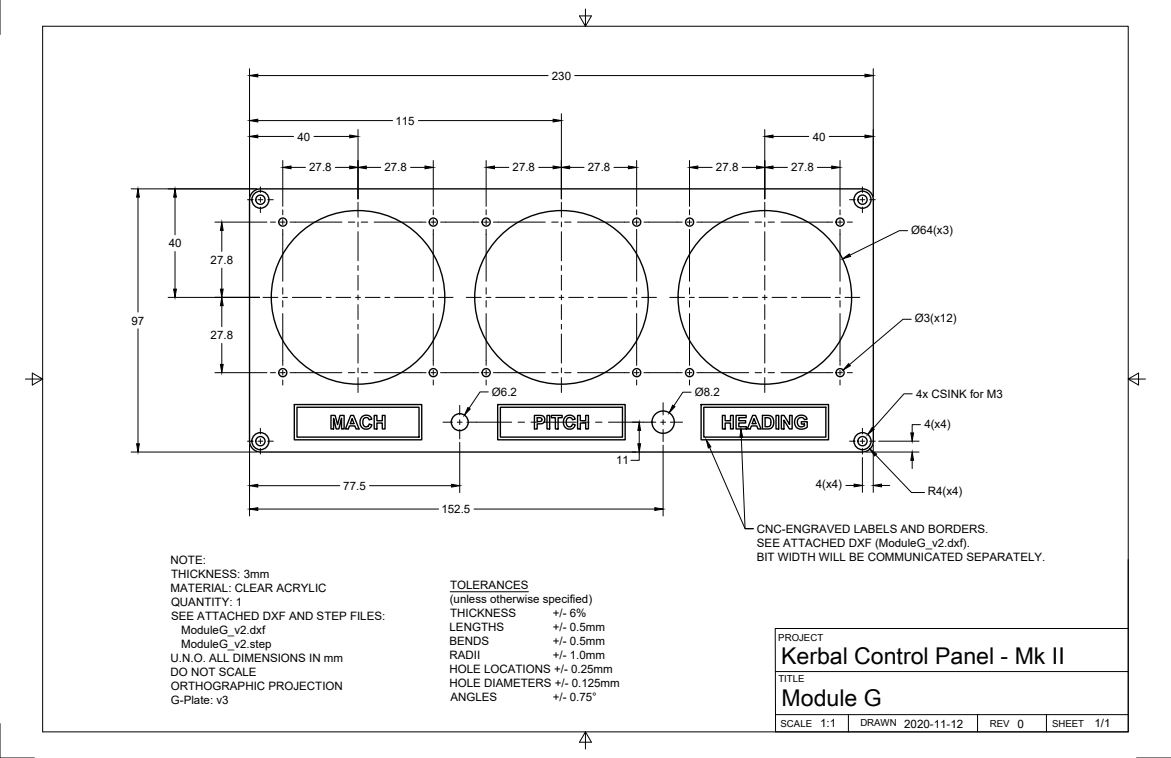
[picture p163: page 1]
SCALE 1:1; DRAWN 2020-11-12; REV 0; SHEET 1/1; Module G; 4x CSINK for M3; THICKNESS; LENGTHS; BENDS; RADII; ANGLES

CNC-ENGRAVED LABELS AND BORDERS.
SEE ATTACHED DXF (ModuleG_v2.dxf).
BIT WIDTH WILL BE COMMUNICATED SEPARATELY.

NOTE:
THICKNESS: 3mm
MATERIAL: CLEAR ACRYLIC
QUANTITY: 1
SEE ATTACHED DXF AND STEP FILES:
ModuleG_v2.dxf
ModuleG_v2.step
U.N.O. ALL DIMENSIONS IN mm
DO NOT SCALE
ORTHOGRAPHIC PROJECTION
G-Plate: v3

TOLERANCES
(unless otherwise specified)
HOLE LOCATIONS +/- 0.25mm
HOLE DIAMETERS +/- 0.125mm

PROJECT
Kerbal Control Panel - Mk II
