mountaineerman/KCP2/KCP2-physical/CAD/ForManufacture/ClearAcrylic/Module H/ModuleH_Rev0_v8.pdf

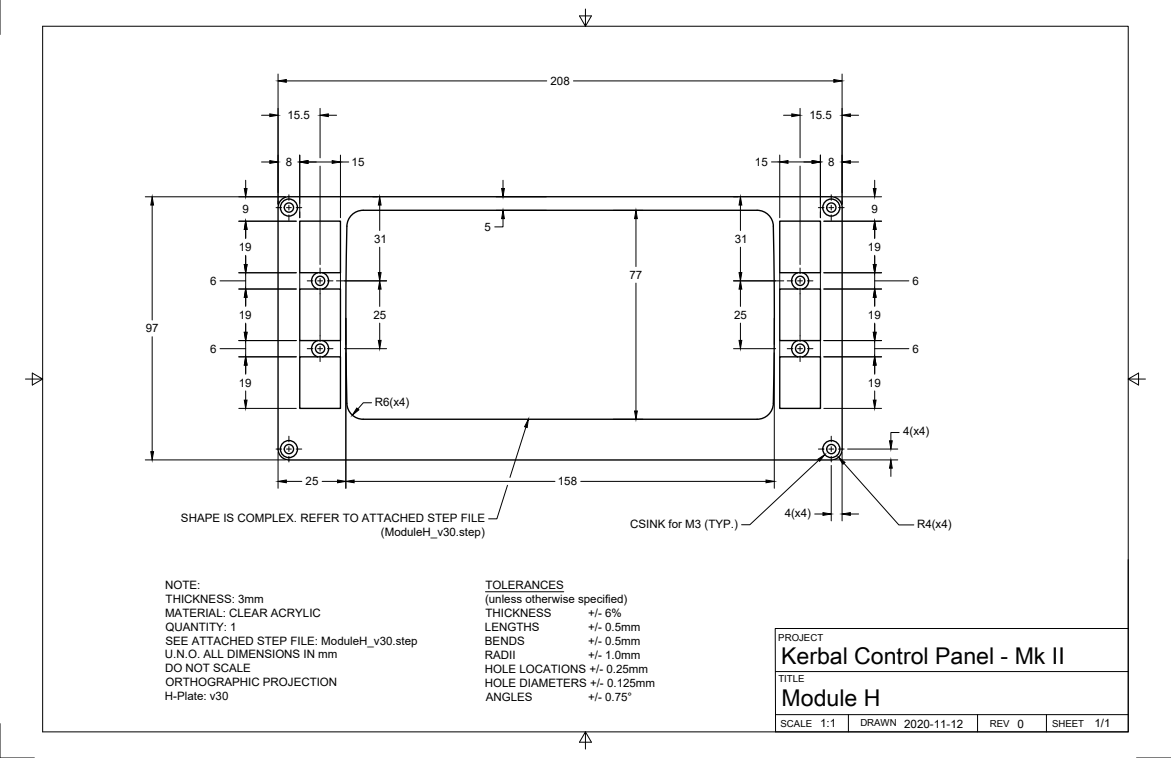
[picture p164: page 1]
SCALE 1:1; DRAWN 2020-11-12; REV 0; SHEET 1/1; Module H; CSINK for M3 (TYP.); THICKNESS; LENGTHS; BENDS; RADII; ANGLES

SHAPE IS COMPLEX. REFER TO ATTACHED STEP FILE

NOTE:
THICKNESS: 3mm
MATERIAL: CLEAR ACRYLIC
QUANTITY: 1
SEE ATTACHED STEP FILE: ModuleH_v30.step
U.N.O. ALL DIMENSIONS IN mm
DO NOT SCALE
ORTHOGRAPHIC PROJECTION
H-Plate: v30

TOLERANCES
(unless otherwise specified)
HOLE LOCATIONS +/- 0.25mm
HOLE DIAMETERS +/- 0.125mm

PROJECT
Kerbal Control Panel - Mk II
