mountaineerman/KCP2/KCP2-physical/CAD/ForManufacture/ClearAcrylic/Module I/ModuleI_Rev0_v6.pdf

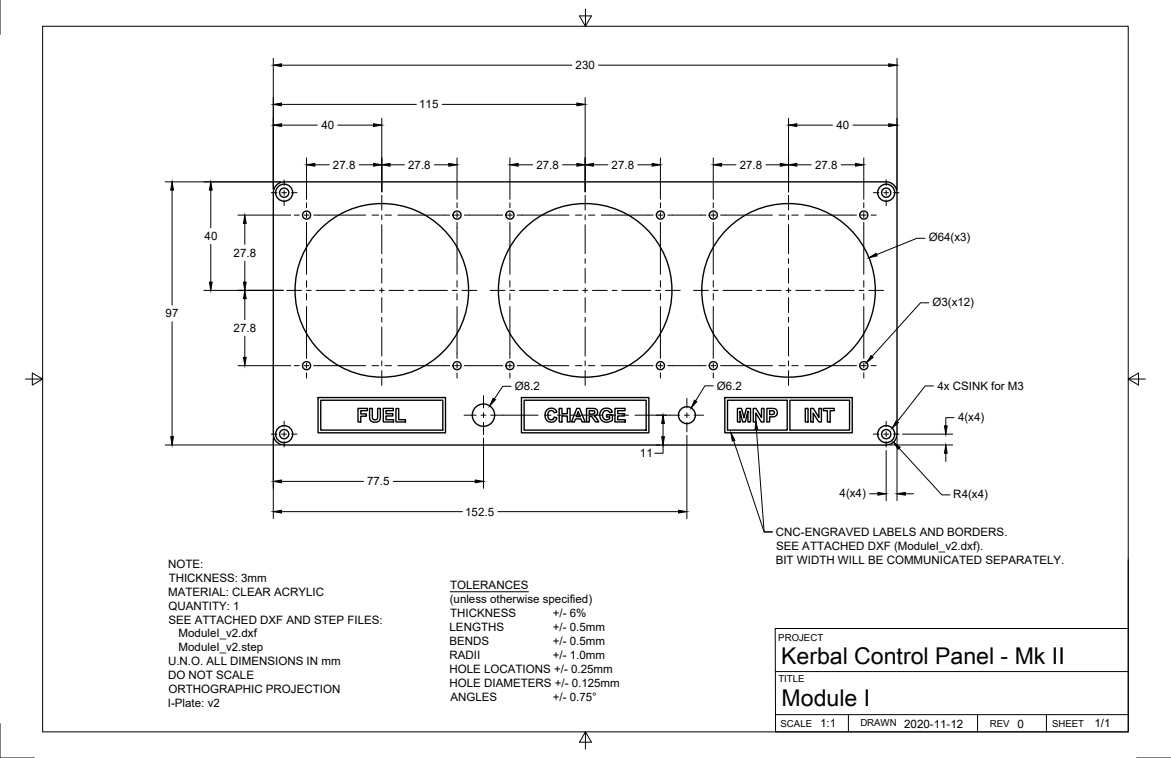
[picture p165: page 1]
SCALE 1:1; DRAWN 2020-11-12; REV 0; SHEET 1/1; Module I; 4x CSINK for M3; NOTE:; BIT WIDTH WILL BE COMMUNICATED SEPARATELY.; THICKNESS; LENGTHS; BENDS; RADII; ANGLES

CNC-ENGRAVED LABELS AND BORDERS.
SEE ATTACHED DXF (ModuleI_v2.dxf).

THICKNESS: 3mm
MATERIAL: CLEAR ACRYLIC
QUANTITY: 1
SEE ATTACHED DXF AND STEP FILES:
ModuleI_v2.dxf
ModuleI_v2.step
U.N.O. ALL DIMENSIONS IN mm
DO NOT SCALE
ORTHOGRAPHIC PROJECTION
I-Plate: v2

TOLERANCES
(unless otherwise specified)
HOLE LOCATIONS +/- 0.25mm
HOLE DIAMETERS +/- 0.125mm

PROJECT
Kerbal Control Panel - Mk II
